olofos/rv321/hardware/memory-ram/memory-ram.kicad_pcb

## KiCad design hardware/memory-ram/memory-ram.kicad_pcb (2022-06-17)

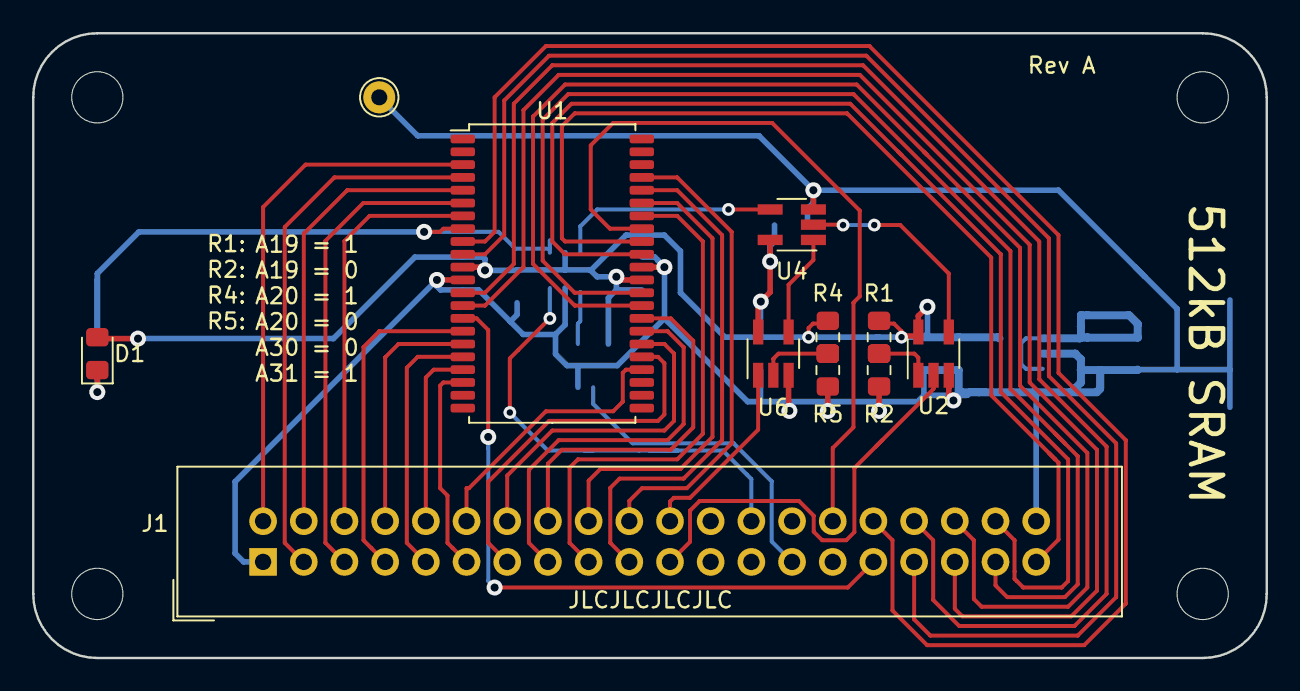
[picture p21: board memory-ram.kicad_pcb from above]

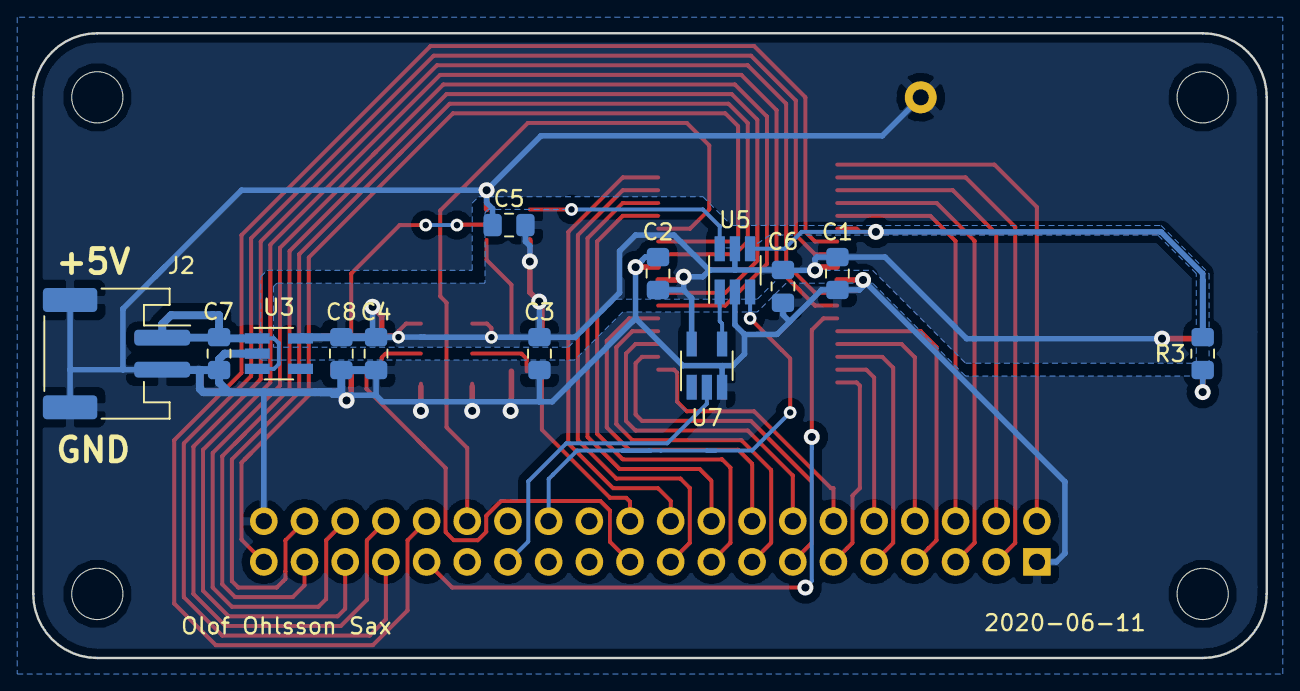
[picture p22: board memory-ram.kicad_pcb from below]

Board: 2 copper layers, 77.0 x 39.0 mm, 28 parts (13 on the bottom side), 44 nets.

Parts:
C1, C2, C3, C4, C5, C6: 100n; C_0805_2012Metric_Pad1.15x1.40mm_HandSolder
C7, C8: 1u; C_0805_2012Metric_Pad1.15x1.40mm_HandSolder
D1: LED; LED_0805_2012Metric_Pad1.15x1.40mm_HandSolder
H1, H2, H3, H4: MountingHole; MountingHole_3.2mm_M3
J1: Conn_Mem_Ext; IDC-Header_2x20_P2.54mm_Vertical
J2: Conn_Power; JST_PH_S2B-PH-SM4-TB_1x02-1MP_P2.00mm_Horizontal
R1, R2, R4, R5: 0; R_0805_2012Metric_Pad1.15x1.40mm_HandSolder
R3: 330; R_0805_2012Metric_Pad1.15x1.40mm_HandSolder
TP1: TestPoint; TestPoint_THTPad_D2.0mm_Drill1.0mm
U1: IS61WV5128EDBLL-10TLI; TSOP-II-44_10.16x18.41mm_P0.8mm
U2, U6: 74LVC1G86; SOT-23-5_HandSoldering
U3: MIC5504-3.3YM5; SOT-23-5_HandSoldering
U4: 74LVC1G32; SOT-23-5_HandSoldering
U5: 74LVC1G332; SOT-23-6_Handsoldering
U7: 74LVC1G04; SOT-23-5_HandSoldering

Connections:
/A0: J1.2, U1.3
/A1: J1.3, U1.4
/A2: J1.4, U1.5
/A3: J1.5, U1.6
/A4: J1.6, U1.7
/A5: J1.7, U1.16
/A6: J1.8, U1.17
/A7: J1.9, U1.18
/A8: J1.10, U1.19
/A9: J1.11, U1.20
/A10: J1.12, U1.26
/A11: J1.13, U1.27
/A12: J1.14, U1.28
/A13: J1.15, U1.29
/A14: J1.16, U1.30
/A15: J1.17, U1.38
/A16: J1.18, U1.39
/A17: J1.19, U1.40
/A18: J1.20, U1.41
/A19: J1.21, U2.2
/A19-20: U4.4, U5.6
/A20: J1.22, U6.1
/A30: J1.26, U5.3
/A31: J1.27, U7.2
/B19: R1.2, R2.1, U2.1
/B20: R4.2, R5.1, U6.2
/D0: J1.32, U1.9
/D1: J1.33, U1.10
/D2: J1.34, U1.13
/D3: J1.35, U1.14
/D4: J1.36, U1.31
/D5: J1.37, U1.32
/D6: J1.38, U1.35
/D7: J1.39, U1.36
/V_IN: C7.2, J2.1, U3.1, U3.3
/X19: U2.4, U4.2
/X20: U4.1, U6.4
/~A31: U5.1, U7.4
/~CE: R3.2, U1.8, U5.4
/~MEM_OE: J1.30, U1.37
/~MEM_WE: J1.31, U1.15
GND: C1.1, C2.1, C3.1, C4.1, C5.1, C6.1, C7.1, C8.1, J1.1, J1.40, J2.2, J2.MP, R2.2, R5.2, TP1.1, U1.12, U1.34, U2.3, U3.2, U4.3, U5.2, U6.3, U7.3
unnamed: D1.1, R3.1
VCC: C1.2, C2.2, C3.2, C4.2, C5.2, C6.2, C8.2, D1.2, R1.1, R4.1, U1.11, U1.33, U2.5, U3.5, U4.5, U5.5, U6.5, U7.5
