olofos/rv321/hardware/pc/pc.kicad_pcb

## KiCad design hardware/pc/pc.kicad_pcb (2022-06-17)

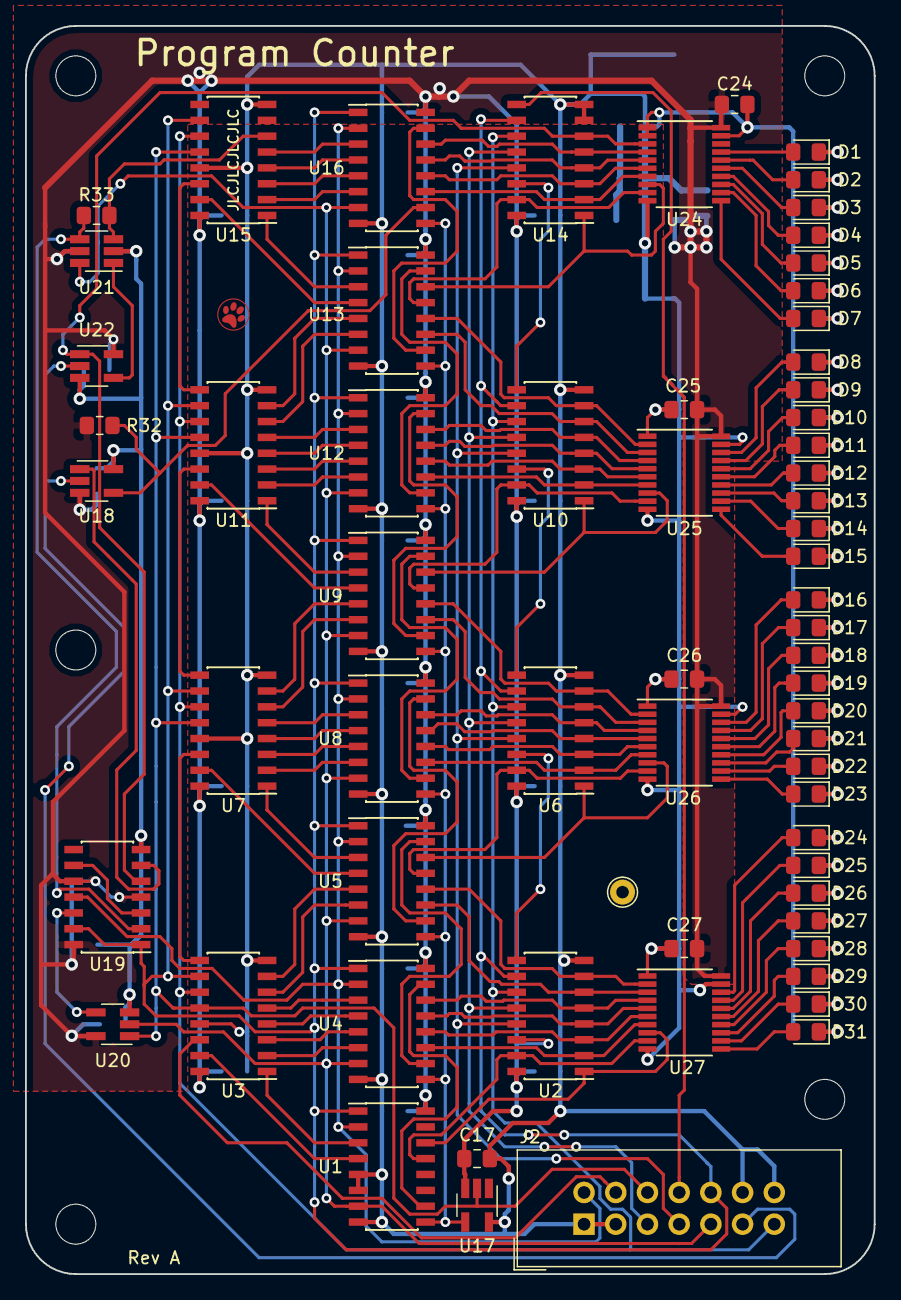
[picture p23: board pc.kicad_pcb from above]

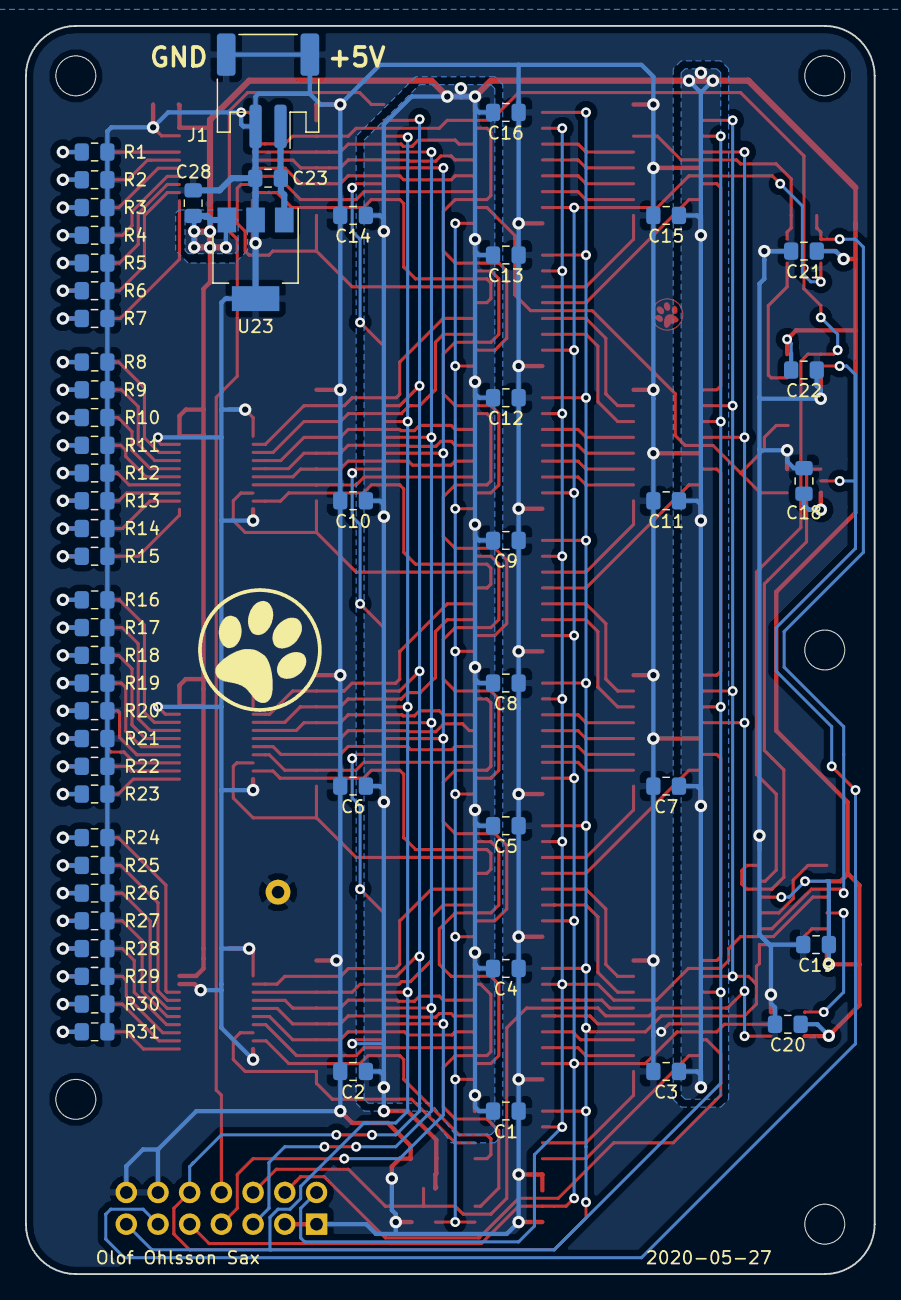
[picture p24: board pc.kicad_pcb from below]

Board: 2 copper layers, 68.0 x 100.0 mm, 127 parts (56 on the bottom side), 157 nets.

Parts:
C1, C2, C3, C4, C5, C6, C7, C8, C9, C10, C11, C12, C13, C14, C15, C16, C17, C18, C19, C20, C21, C22, C24, C25, C26, C27: 100n; C_0805_2012Metric_Pad1.15x1.40mm_HandSolder
C23: 4u7; C_0805_2012Metric_Pad1.15x1.40mm_HandSolder
C28: 1u; C_0805_2012Metric_Pad1.15x1.40mm_HandSolder
D1, D2, D3, D4, D5, D6, D7, D8, D9, D10, D11, D12, D13, D14, D15, D16, D17, D18, D19, D20, D21, D22, D23, D24, D25, D26, D27, D28, D29, D30, D31: LED; LED_0805_2012Metric_Pad1.15x1.40mm_HandSolder
H1, H2, H3, H5, H6: MountingHole; MountingHole_3.2mm_M3
J1: Conn_Power; JST_PH_S2B-PH-SM4-TB_1x02-1MP_P2.00mm_Horizontal
J2: Conn_PC; IDC-Header_2x07_P2.54mm_Vertical
R1, R2, R3, R4, R5, R6, R7, R8, R9, R10, R11, R12, R13, R14, R15, R16, R17, R18, R19, R20, R21, R22, R23, R24, R25, R26, R27, R28, R29, R30, R31: 330; R_0805_2012Metric_Pad1.15x1.40mm_HandSolder
R32, R33: 0; R_0805_2012Metric_Pad1.15x1.40mm_HandSolder
TP1: TestPoint; TestPoint_THTPad_D2.0mm_Drill1.0mm
U1, U4, U5, U8, U9, U12, U13, U16: 74HC161; SOIC-16_3.9x9.9mm_P1.27mm
U2, U6, U10, U14: 74HC597; SOIC-16_3.9x9.9mm_P1.27mm
U3, U7, U11, U15: 74HC595; SOIC-16_3.9x9.9mm_P1.27mm
U17: 74LVC1G04; SOT-23-5_HandSoldering
U18: 74LVC1G38; SOT-23-5_HandSoldering
U19: 74HC74; SOIC-14_3.9x8.7mm_P1.27mm
U20: 74LVC1G32; SOT-23-5_HandSoldering
U21: 74LVC1G157; SOT-23-6_Handsoldering
U22: 74LVC1G86; SOT-23-5_HandSoldering
U23: MCP1825S; SOT-223-3_TabPin2
U24, U25, U26, U27: 74HC541; TSSOP-20_4.4x6.5mm_P0.65mm

Connections:
/BUS_CLK: J2.13, U2.11, U3.11, U6.11, U7.11, U10.11, U11.11, U14.11, U15.11
/CLK: J2.2, U1.2, U4.2, U5.2, U8.2, U9.2, U12.2, U13.2, U16.2, U19.11
/CNT_2: J2.11, U18.2, U22.2
/CNT_EN: J2.9, U1.7, U4.7, U5.7, U8.7, U9.7, U12.7, U13.7, U16.7, U20.2, U21.6
/CNT_~PE: U1.9, U4.9, U5.9, U8.9, U9.9, U12.9, U13.9, U16.9, U17.4
/D1: R33.2, U15.6, U21.3
/D2: U15.5, U16.3
/D3: U15.4, U16.4
/D4: U15.3, U16.5
/D5: U15.2, U16.6
/D6: U13.3, U15.1
/D7: U13.4, U15.15
/D8: U11.7, U13.5
/D8': U11.9, U15.14
/D9: U11.6, U13.6
/D10: U11.5, U12.3
/D11: U11.4, U12.4
/D12: U11.3, U12.5
/D13: U11.2, U12.6
/D14: U9.3, U11.1
/D15: U9.4, U11.15
/D16: U7.7, U9.5
/D16': U7.9, U11.14
/D17: U7.6, U9.6
/D18: U7.5, U8.3
/D19: U7.4, U8.4
/D20: U7.3, U8.5
/D21: U7.2, U8.6
/D22: U5.3, U7.1
/D23: U5.4, U7.15
/D24: U3.7, U5.5
/D24': U3.9, U7.14
/D25: U3.6, U5.6
/D26: U3.5, U4.3
/D27: U3.4, U4.4
/D28: U3.3, U4.5
/D29: U3.2, U4.6
/D30: U1.3, U3.1
/D31: U1.4, U3.15
/IN: J2.4, U3.14
/IN_LATCH: J2.6, U3.12, U7.12, U11.12, U15.12, U17.2, U20.1
/OUT: J2.8, U14.9
/OUT_LATCH: J2.5, U2.12, U6.12, U10.12, U14.12
/OUT_S~P: J2.7, U2.13, U6.13, U10.13, U14.13
/Q1: U14.6, U19.5, U22.1, U24.3
/Q1_CLK: U19.12, U20.4
/Q1_FF_C: U19.3, U19.9
/Q1_FF_D: R33.1, U19.2, U21.4
/Q1_OR_~Q1: U21.1, U22.4
/Q2: U14.5, U16.14, U24.4
/Q3: U14.4, U16.13, U24.5
/Q4: U14.3, U16.12, U24.6
/Q5: U14.2, U16.11, U24.7
/Q6: U13.14, U14.1, U24.8
/Q7: U13.13, U14.15, U24.9
/Q8: U10.7, U13.12, U25.2
/Q8': U10.9, U14.14
/Q9: U10.6, U13.11, U25.3
/Q10: U10.5, U12.14, U25.4
/Q11: U10.4, U12.13, U25.5
/Q12: U10.3, U12.12, U25.6
/Q13: U10.2, U12.11, U25.7
/Q14: U9.14, U10.1, U25.8
/Q15: U9.13, U10.15, U25.9
/Q16: U6.7, U9.12, U26.2
/Q16': U6.9, U10.14
/Q17: U6.6, U9.11, U26.3
/Q18: U6.5, U8.14, U26.4
/Q19: U6.4, U8.13, U26.5
/Q20: U6.3, U8.12, U26.6
/Q21: U6.2, U8.11, U26.7
/Q22: U5.14, U6.1, U26.8
/Q23: U5.13, U6.15, U26.9
/Q24: U2.7, U5.12, U27.2
/Q24': U2.9, U6.14
/Q25: U2.6, U5.11, U27.3
/Q26: U2.5, U4.14, U27.4
/Q27: U2.4, U4.13, U27.5
/Q28: U2.3, U4.12, U27.6
/Q29: U2.2, U4.11, U27.7
/Q30: U1.14, U2.1, U27.8
/Q31: U1.13, U2.15, U27.9
/TC1: R32.2, U16.10, U18.4
/TC5: U13.10, U16.15
/TC9: U12.10, U13.15
/TC13: U9.10, U12.15
/TC17: U8.10, U9.15
/TC21: U5.10, U8.15
/TC25: U4.10, U5.15
/TC29: U1.10, U4.15
/V_IN: C23.1, J1.1, U23.1
/~Q1: U18.1, U19.6
/~RESET: J2.10, U1.1, U2.10, U3.10, U4.1, U5.1, U6.10, U7.10, U8.1, U9.1, U10.10, U11.10, U12.1, U13.1, U14.10, U15.10, U16.1, U19.1, U19.13
GND: C1.2, C2.2, C3.2, C4.2, C5.2, C6.2, C7.2, C8.2, C9.2, C10.2, C11.2, C12.2, C13.2, C14.2, C15.2, C16.2, C17.2, C18.2, C19.2, C20.2, C21.2, C22.2, C23.2, C24.2, C25.2, C26.2, C27.2, C28.2, J1.2, J1.MP, J2.1, J2.3, J2.12, J2.14, R1.2, R2.2, R3.2, R4.2, R5.2, R6.2, R7.2, R8.2, R9.2, R10.2, R11.2, R12.2, R13.2, R14.2, R15.2, R16.2, R17.2, R18.2, R19.2, R20.2, R21.2, R22.2, R23.2, R24.2, R25.2, R26.2, R27.2, R28.2, R29.2, R30.2, R31.2, TP1.1, U1.5, U1.6, U1.8, U2.8, U3.8, U3.13, U4.8, U5.8, U6.8, U7.8, U7.13, U8.8, U9.8, U10.8, U11.8, U11.13, U12.8, U13.8, U14.7, U14.8, U15.8, U15.13, U16.8, U17.5, U18.5, U19.7, U20.3, U21.2, U22.3, U23.2, U24.1, U24.2, U24.10, U24.19, U25.1, U25.10, U25.19, U26.1, U26.10, U26.19, U27.1, U27.10, U27.19
unnamed: D1.1, R1.1
unnamed: D1.2, U24.17
unnamed: D2.1, R2.1
unnamed: D2.2, U24.16
unnamed: D3.1, R3.1
unnamed: D3.2, U24.15
unnamed: D4.1, R4.1
unnamed: D4.2, U24.14
unnamed: D5.1, R5.1
unnamed: D5.2, U24.13
unnamed: D6.1, R6.1
unnamed: D6.2, U24.12
unnamed: D7.1, R7.1
unnamed: D7.2, U24.11
unnamed: D8.1, R8.1
unnamed: D8.2, U25.18
unnamed: D9.1, R9.1
unnamed: D9.2, U25.17
unnamed: D10.1, R10.1
unnamed: D10.2, U25.16
unnamed: D11.1, R11.1
unnamed: D11.2, U25.15
unnamed: D12.1, R12.1
unnamed: D12.2, U25.14
unnamed: D13.1, R13.1
unnamed: D13.2, U25.13
unnamed: D14.1, R14.1
unnamed: D14.2, U25.12
unnamed: D15.1, R15.1
unnamed: D15.2, U25.11
unnamed: D16.1, R16.1
unnamed: D16.2, U26.18
unnamed: D17.1, R17.1
unnamed: D17.2, U26.17
unnamed: D18.1, R18.1
unnamed: D18.2, U26.16
unnamed: D19.1, R19.1
unnamed: D19.2, U26.15
unnamed: D20.1, R20.1
unnamed: D20.2, U26.14
unnamed: D21.1, R21.1
unnamed: D21.2, U26.13
unnamed: D22.1, R22.1
unnamed: D22.2, U26.12
unnamed: D23.1, R23.1
unnamed: D23.2, U26.11
unnamed: D24.1, R24.1
unnamed: D24.2, U27.18
unnamed: D25.1, R25.1
unnamed: D25.2, U27.17
unnamed: D26.1, R26.1
unnamed: D26.2, U27.16
unnamed: D27.1, R27.1
unnamed: D27.2, U27.15
unnamed: D28.1, R28.1
unnamed: D28.2, U27.14
unnamed: D29.1, R29.1
unnamed: D29.2, U27.13
unnamed: D30.1, R30.1
unnamed: D30.2, U27.12
unnamed: D31.1, R31.1
unnamed: D31.2, U27.11
VCC: C1.1, C2.1, C3.1, C4.1, C5.1, C6.1, C7.1, C8.1, C9.1, C10.1, C11.1, C12.1, C13.1, C14.1, C15.1, C16.1, C17.1, C18.1, C19.1, C20.1, C21.1, C22.1, C24.1, C25.1, C26.1, C27.1, C28.1, R32.1, U1.16, U2.14, U2.16, U3.16, U4.16, U5.16, U6.16, U7.16, U8.16, U9.16, U10.16, U11.16, U12.16, U13.16, U14.16, U15.16, U16.16, U17.3, U18.3, U19.4, U19.10, U19.14, U20.5, U21.5, U22.5, U23.3, U24.20, U25.20, U26.20, U27.20
