olofos/rv321/hardware/alu/alu.kicad_pcb

## KiCad design hardware/alu/alu.kicad_pcb (2022-06-17)

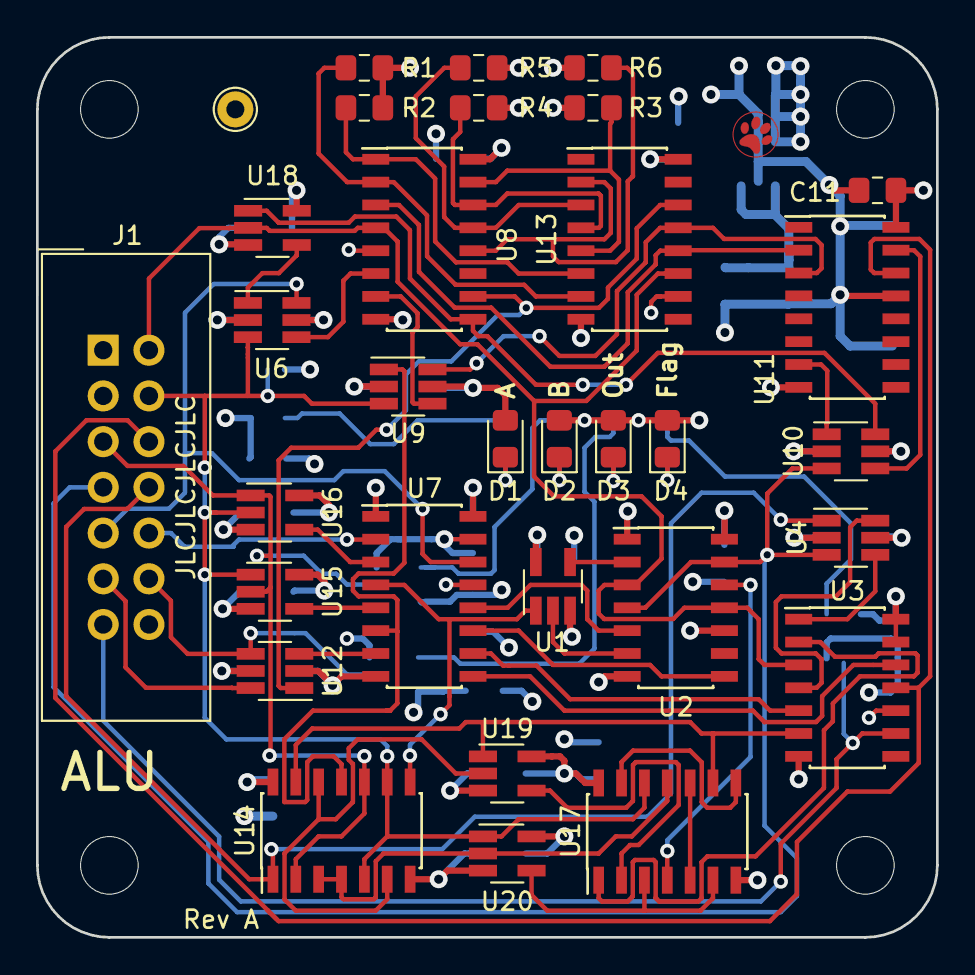
[picture p25: board alu.kicad_pcb from above]

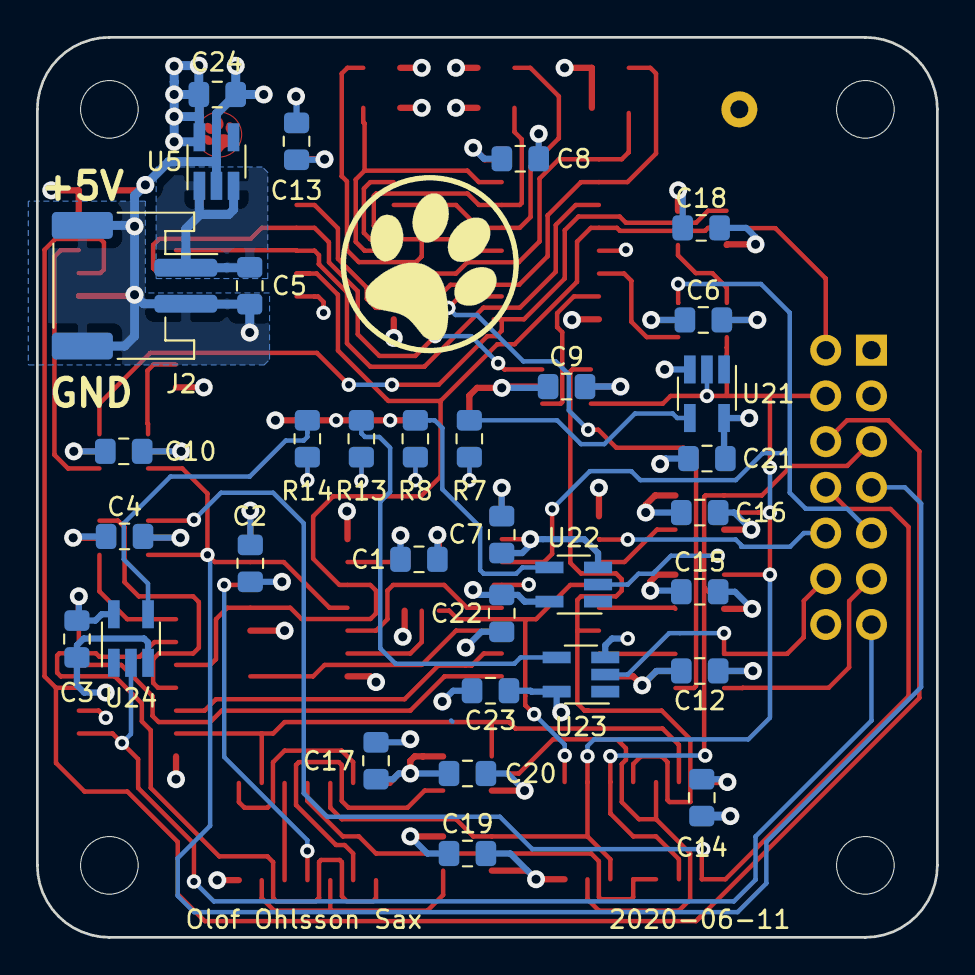
[picture p26: board alu.kicad_pcb from below]

Board: 4 copper layers, 50.0 x 50.0 mm, 69 parts (33 on the bottom side), 59 nets.

Parts:
C1, C2, C3, C4, C6, C7, C8, C9, C10, C11, C12, C13, C14, C15, C16, C17, C18, C19, C20, C21, C22, C23: 100n; C_0805_2012Metric_Pad1.15x1.40mm_HandSolder
C5, C24: 1u; C_0805_2012Metric_Pad1.15x1.40mm_HandSolder
D1, D2, D3, D4: LED; LED_0805_2012Metric_Pad1.15x1.40mm_HandSolder
H1, H2, H3, H4: MountingHole; MountingHole_3.2mm_M3
J1: Conn_ALU; IDC-Header_2x07_P2.54mm_Vertical
J2: Conn_Power; JST_PH_S2B-PH-SM4-TB_1x02-1MP_P2.00mm_Horizontal
R1, R2, R3, R4, R5, R6: 10k; R_0805_2012Metric_Pad1.15x1.40mm_HandSolder
R7, R8, R13, R14: 330; R_0805_2012Metric_Pad1.15x1.40mm_HandSolder
TP1: TestPoint; TestPoint_THTPad_D2.0mm_Drill1.0mm
U1: 74LVC1G02; SOT-23-5_HandSoldering
U2, U3: 74HC74; SOIC-14_3.9x8.7mm_P1.27mm
U4: 74LVC1G19; SOT-23-6_Handsoldering
U5: MIC5504-3.3YM5; SOT-23-5_HandSoldering
U6: 74LVC1G175; SOT-23-6_Handsoldering
U7: 74HC253; SOIC-16_3.9x9.9mm_P1.27mm
U8: HEF4557B; SOIC-16_3.9x9.9mm_P1.27mm
U9, U12: 74LVC1G157; SOT-23-6_Handsoldering
U10: 74AUC2G04; SOT-23-6_Handsoldering
U11: 74HC4017; SOIC-16_3.9x9.9mm_P1.27mm
U13: 74HC595; SOIC-16_3.9x9.9mm_P1.27mm
U14: 74HC86; SOIC-14_3.9x8.7mm_P1.27mm
U15: 74LVC1G32; SOT-23-5_HandSoldering
U16, U18, U19, U20: 74LVC1G08; SOT-23-5_HandSoldering
U17: 74HC02; SOIC-14_3.9x8.7mm_P1.27mm
U21, U22, U23, U24: 74LVC1G04; SOT-23-5_HandSoldering

Connections:
/(A+B)&C: U17.2, U19.4
/A&~B: U17.3, U17.6, U20.4
/A+B: U14.6, U14.12, U19.2
/ALU_AUX: J1.6, U3.11, U11.14
/ALU_S0: J1.9, U6.6, U7.14
/ALU_S1: J1.10, U7.2
/ALU_S2: J1.11, U12.6
/BUS_CLK: J1.2, U2.3, U2.11, U3.3, U8.4, U13.11, U18.2
/B_OR_~B: U14.3, U14.4, U17.11, U20.2
/C_TO_NEG: U17.5, U17.10
/DAH: D1.1, R7.2
/DAL: R7.1, U21.4
/DBH: D2.1, R8.2
/DBL: R8.1, U22.4
/DFH: D4.1, R14.2
/DFL: R14.1, U24.4
/DOH: D3.1, R13.2
/DOL: R13.1, U23.4
/EQUAL: U2.5, U7.12
/EQ_FF_D: U1.4, U2.2
/EQ_FF_~Q: U1.2, U2.6
/FLAG: U3.12, U7.9
/IN_A: J1.4, U6.3, U9.3, U14.5, U14.9, U15.1, U16.2, U17.12, U20.1, U21.2
/IN_B: J1.5, U14.2, U14.10, U15.2, U16.1, U22.2
/IN_C: U3.6, U14.13, U17.9, U19.1
/IN_N: J1.8, U4.1, U14.1
/L1: R1.2, U8.2, U13.7
/L2: R2.2, U8.1, U13.6
/L4: R3.2, U8.15, U13.5
/L8: R4.1, U8.14, U13.4
/L16: R5.2, U8.13, U13.3
/L32: R6.1, U8.12, U13.2
/LT: U2.8, U7.11
/LTU: U3.5, U7.10
/OUT: J1.12, U12.4, U23.2
/OUT_AND: U7.3, U16.4
/OUT_BIN: U7.7, U12.3
/OUT_FLAG: J1.13, U3.9, U24.2
/OUT_OR: U7.5, U15.4
/OUT_SHIFT: U8.10, U12.1, U13.14
/OUT_SUM: U7.6, U9.1, U14.11
/OUT_XOR: U1.1, U7.4, U14.8
/SH_4017_MR: U10.4, U11.15
/SH_IN: U8.7, U9.4
/SH_LOADLEN: U9.6, U11.3, U13.13
/SH_OUTPUT: U10.1, U11.7
/SH_RESET: U8.3, U11.2, U13.12
/SH_S_FF_C: U6.1, U18.4
/SH_S_FF_Q: U6.4, U8.6
/V_IN: C5.1, J2.1, U5.1, U5.3
/~ALU_RESET: J1.7, U2.4, U2.13, U4.3, U10.3
/~A&B: U17.8, U17.13
/~C_FF_~R: U3.1, U4.4
/~C_FF_~S: U3.4, U4.6
/~OUT_C: U3.2, U17.1
/~OUT_NEG: U2.12, U17.4
/~SH_OUTPUT: U8.9, U10.6, U18.1
GND: C1.2, C2.2, C3.2, C4.2, C5.2, C6.2, C7.2, C8.2, C9.2, C10.2, C11.2, C12.2, C13.2, C14.2, C15.2, C16.2, C17.2, C18.2, C19.2, C20.2, C21.2, C22.2, C23.2, C24.2, J1.1, J1.3, J1.14, J2.2, J2.MP, R4.2, R6.2, TP1.1, U1.3, U2.7, U3.7, U4.2, U5.2, U6.2, U7.1, U7.8, U7.13, U7.15, U8.5, U8.8, U9.2, U10.2, U11.8, U11.13, U12.2, U13.8, U14.7, U15.3, U16.3, U17.7, U18.3, U19.3, U20.3, U21.3, U22.3, U23.3, U24.3
VCC: C1.1, C2.1, C3.1, C4.1, C6.1, C7.1, C8.1, C9.1, C10.1, C11.1, C12.1, C13.1, C14.1, C15.1, C16.1, C17.1, C18.1, C19.1, C20.1, C21.1, C22.1, C23.1, C24.1, D1.2, D2.2, D3.2, D4.2, R1.1, R2.1, R3.1, R5.1, U1.5, U2.1, U2.10, U2.14, U3.10, U3.13, U3.14, U4.5, U5.5, U6.5, U7.16, U8.16, U9.5, U10.5, U11.16, U12.5, U13.10, U13.16, U14.14, U15.5, U16.5, U17.14, U18.5, U19.5, U20.5, U21.5, U22.5, U23.5, U24.5
