olofos/rv321/hardware/register-bank/register-bank.kicad_pcb

## KiCad design hardware/register-bank/register-bank.kicad_pcb (2022-06-17)

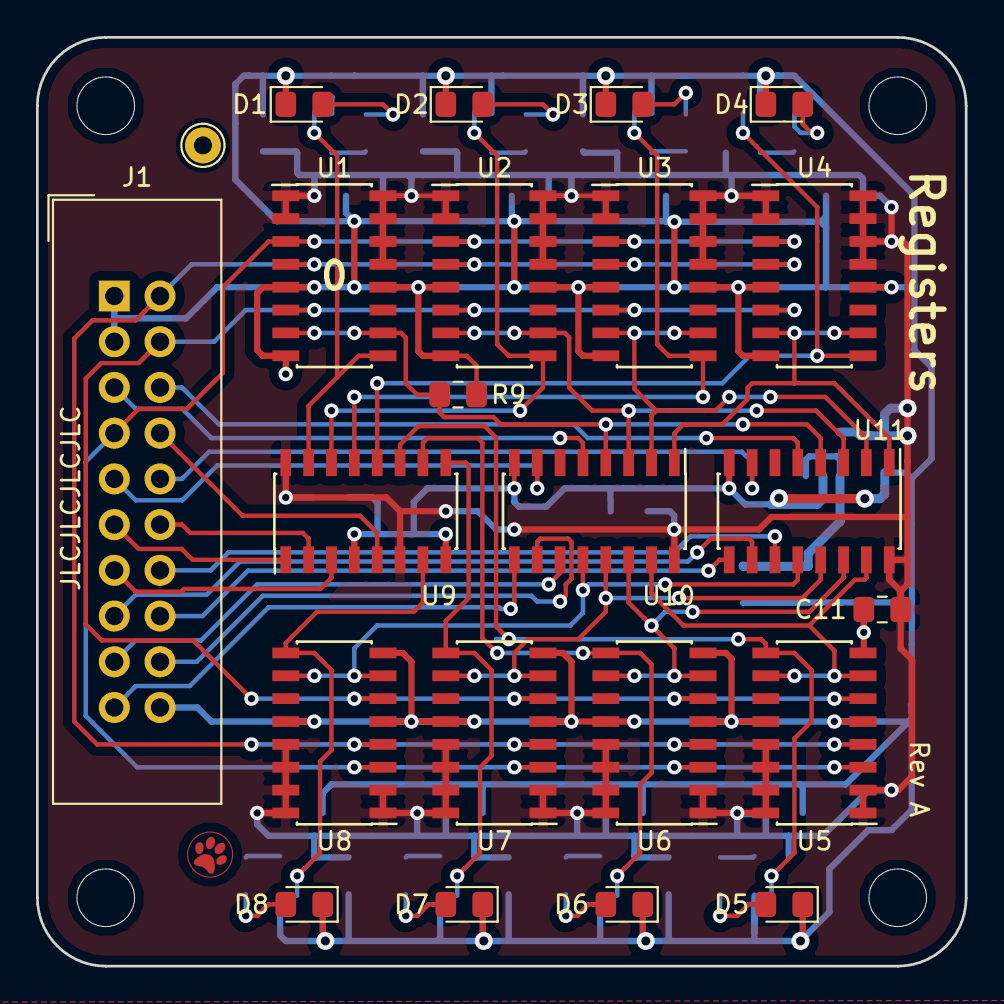
[picture p27: board register-bank.kicad_pcb from above]

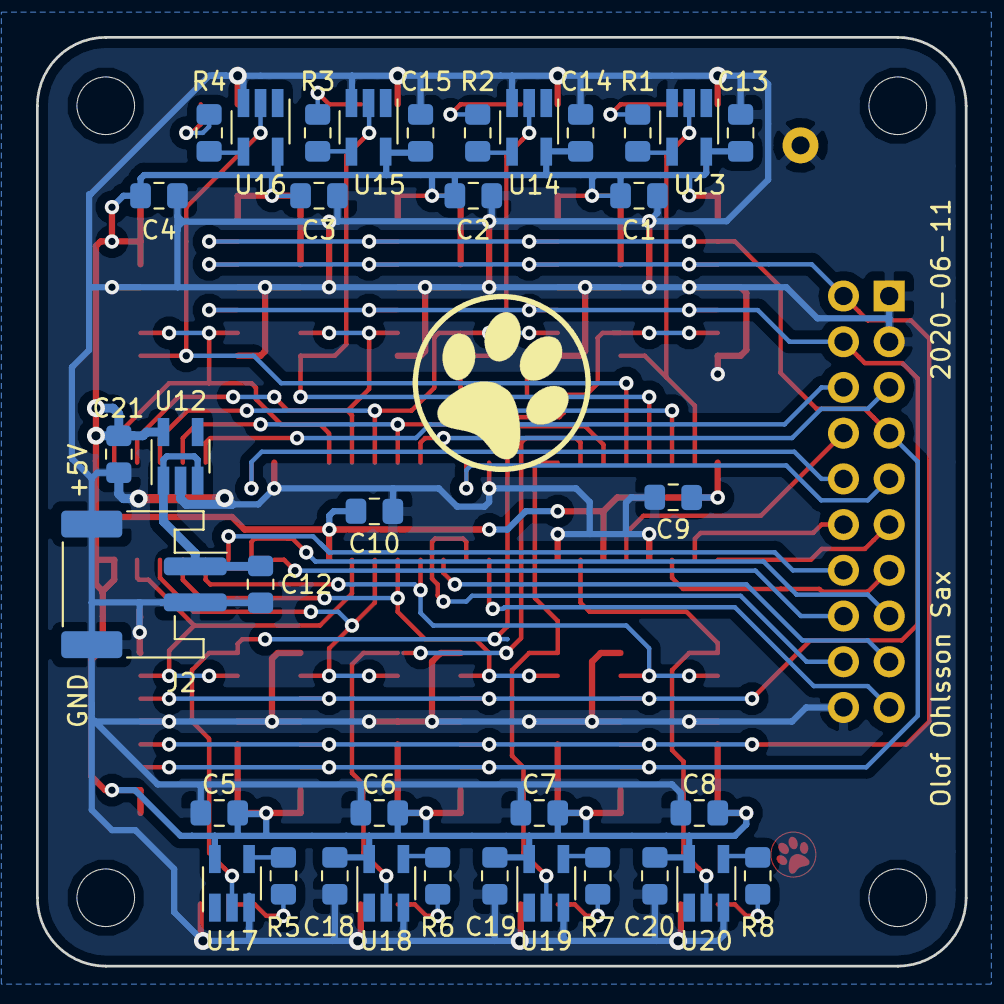
[picture p28: board register-bank.kicad_pcb from below]

Board: 2 copper layers, 51.6 x 51.6 mm, 63 parts (36 on the bottom side), 52 nets.

Parts:
C1, C2, C3, C4, C5, C6, C7, C8, C9, C10, C11, C13, C14, C15, C18, C19, C20: 100n; C_0805_2012Metric_Pad1.15x1.40mm_HandSolder
C12, C21: 1u; C_0805_2012Metric_Pad1.15x1.40mm_HandSolder
D1, D2, D3, D4, D5, D6, D7, D8: LED; LED_0805_2012Metric_Pad1.15x1.40mm_HandSolder
H1, H2, H3, H4: MountingHole; MountingHole_3.2mm_M3
J1: Conn_Reg; IDC-Header_2x10_P2.54mm_Vertical
J2: Conn_Power; JST_PH_S2B-PH-SM4-TB_1x02-1MP_P2.00mm_Horizontal
R1, R2, R3, R4, R5, R6, R7, R8: 330; R_0805_2012Metric_Pad1.15x1.40mm_HandSolder
R9: 0; R_0805_2012Metric_Pad1.15x1.40mm_HandSolder
TP1: TestPoint; TestPoint_THTPad_D2.0mm_Drill1.0mm
U1, U2, U3, U4, U5, U6, U7, U8: HEF4557B; SOIC-16_3.9x9.9mm_P1.27mm
U9: 74HC138; SOIC-16_3.9x9.9mm_P1.27mm
U10, U11: 74HC251; SOIC-16_3.9x9.9mm_P1.27mm
U12: MIC5504-3.3YM5; SOT-23-5_HandSoldering
U13, U14, U15, U16, U17, U18, U19, U20: 74LVC1G04; SOT-23-5_HandSoldering

Connections:
/BUS_CLK: J1.2, U1.4, U2.4, U3.4, U4.4, U5.4, U6.4, U7.4, U8.4
/RAOUT: J1.5, U10.5
/RAS0: J1.17, U10.11
/RAS1: J1.18, U10.10
/RAS2: J1.19, U10.9
/RBOUT: J1.6, U11.5
/RBS0: J1.14, U11.11
/RBS1: J1.15, U11.10
/RBS2: J1.16, U11.9
/RESET: J1.7, U1.3, U2.3, U3.3, U4.3, U5.3, U6.3, U7.3, U8.3
/RIN: J1.4, U1.6, U2.6, U3.6, U4.6, U5.6, U6.6, U7.6, U8.6
/RINS0: J1.11, U9.1
/RINS1: J1.12, U9.2
/RINS2: J1.13, U9.3
/ROUT0: R9.1, U1.7, U1.10, U10.4, U11.4
/ROUT1: U2.7, U2.10, U10.3, U11.3
/ROUT2: U3.7, U3.10, U10.2, U11.2
/ROUT3: U4.7, U4.10, U10.1, U11.1
/ROUT4: U5.7, U5.10, U10.15, U11.15
/ROUT5: U6.7, U6.10, U10.14, U11.14
/ROUT6: U7.7, U7.10, U10.13, U11.13
/ROUT7: U8.7, U8.10, U10.12, U11.12
/V_IN: C12.1, J2.1, U12.1, U12.3
/~RIN_EN0: U1.9, U9.15, U13.2
/~RIN_EN1: U2.9, U9.14, U14.2
/~RIN_EN2: U3.9, U9.13, U15.2
/~RIN_EN3: U4.9, U9.12, U16.2
/~RIN_EN4: U5.9, U9.11, U17.2
/~RIN_EN5: U6.9, U9.10, U18.2
/~RIN_EN6: U7.9, U9.9, U19.2
/~RIN_EN7: U8.9, U9.7, U20.2
/~RIN_EN: J1.8, U9.5
/~ROUT_EN_A: J1.9, U10.7
/~ROUT_EN_B: J1.10, U11.7
GND: C1.2, C2.2, C3.2, C4.2, C5.2, C6.2, C7.2, C8.2, C9.2, C10.2, C11.2, C12.2, C13.2, C14.2, C15.2, C18.2, C19.2, C20.2, C21.2, D1.1, D2.1, D3.1, D4.1, D5.1, D6.1, D7.1, D8.1, J1.1, J1.3, J1.20, J2.2, J2.MP, R9.2, TP1.1, U1.5, U1.8, U1.12, U2.5, U2.8, U2.12, U3.5, U3.8, U3.12, U4.5, U4.8, U4.12, U5.5, U5.8, U5.12, U6.5, U6.8, U6.12, U7.5, U7.8, U7.12, U8.5, U8.8, U8.12, U9.4, U9.8, U10.8, U11.8, U12.2, U13.3, U14.3, U15.3, U16.3, U17.3, U18.3, U19.3, U20.3
unnamed: D1.2, R1.1
unnamed: D2.2, R2.1
unnamed: D3.2, R3.1
unnamed: D4.2, R4.1
unnamed: D5.2, R5.1
unnamed: D6.2, R6.1
unnamed: D7.2, R7.1
unnamed: D8.2, R8.1
unnamed: R1.2, U13.4
unnamed: R2.2, U14.4
unnamed: R3.2, U15.4
unnamed: R4.2, U16.4
unnamed: R5.2, U17.4
unnamed: R6.2, U18.4
unnamed: R7.2, U19.4
unnamed: R8.2, U20.4
VCC: C1.1, C2.1, C3.1, C4.1, C5.1, C6.1, C7.1, C8.1, C9.1, C10.1, C11.1, C13.1, C14.1, C15.1, C18.1, C19.1, C20.1, C21.1, U1.1, U1.2, U1.13, U1.14, U1.15, U1.16, U2.1, U2.2, U2.13, U2.14, U2.15, U2.16, U3.1, U3.2, U3.13, U3.14, U3.15, U3.16, U4.1, U4.2, U4.13, U4.14, U4.15, U4.16, U5.1, U5.2, U5.13, U5.14, U5.15, U5.16, U6.1, U6.2, U6.13, U6.14, U6.15, U6.16, U7.1, U7.2, U7.13, U7.14, U7.15, U7.16, U8.1, U8.2, U8.13, U8.14, U8.15, U8.16, U9.6, U9.16, U10.16, U11.16, U12.5, U13.5, U14.5, U15.5, U16.5, U17.5, U18.5, U19.5, U20.5
