olofos/rv321/hardware/memory/memory.kicad_pcb

## KiCad design hardware/memory/memory.kicad_pcb (2022-06-17)

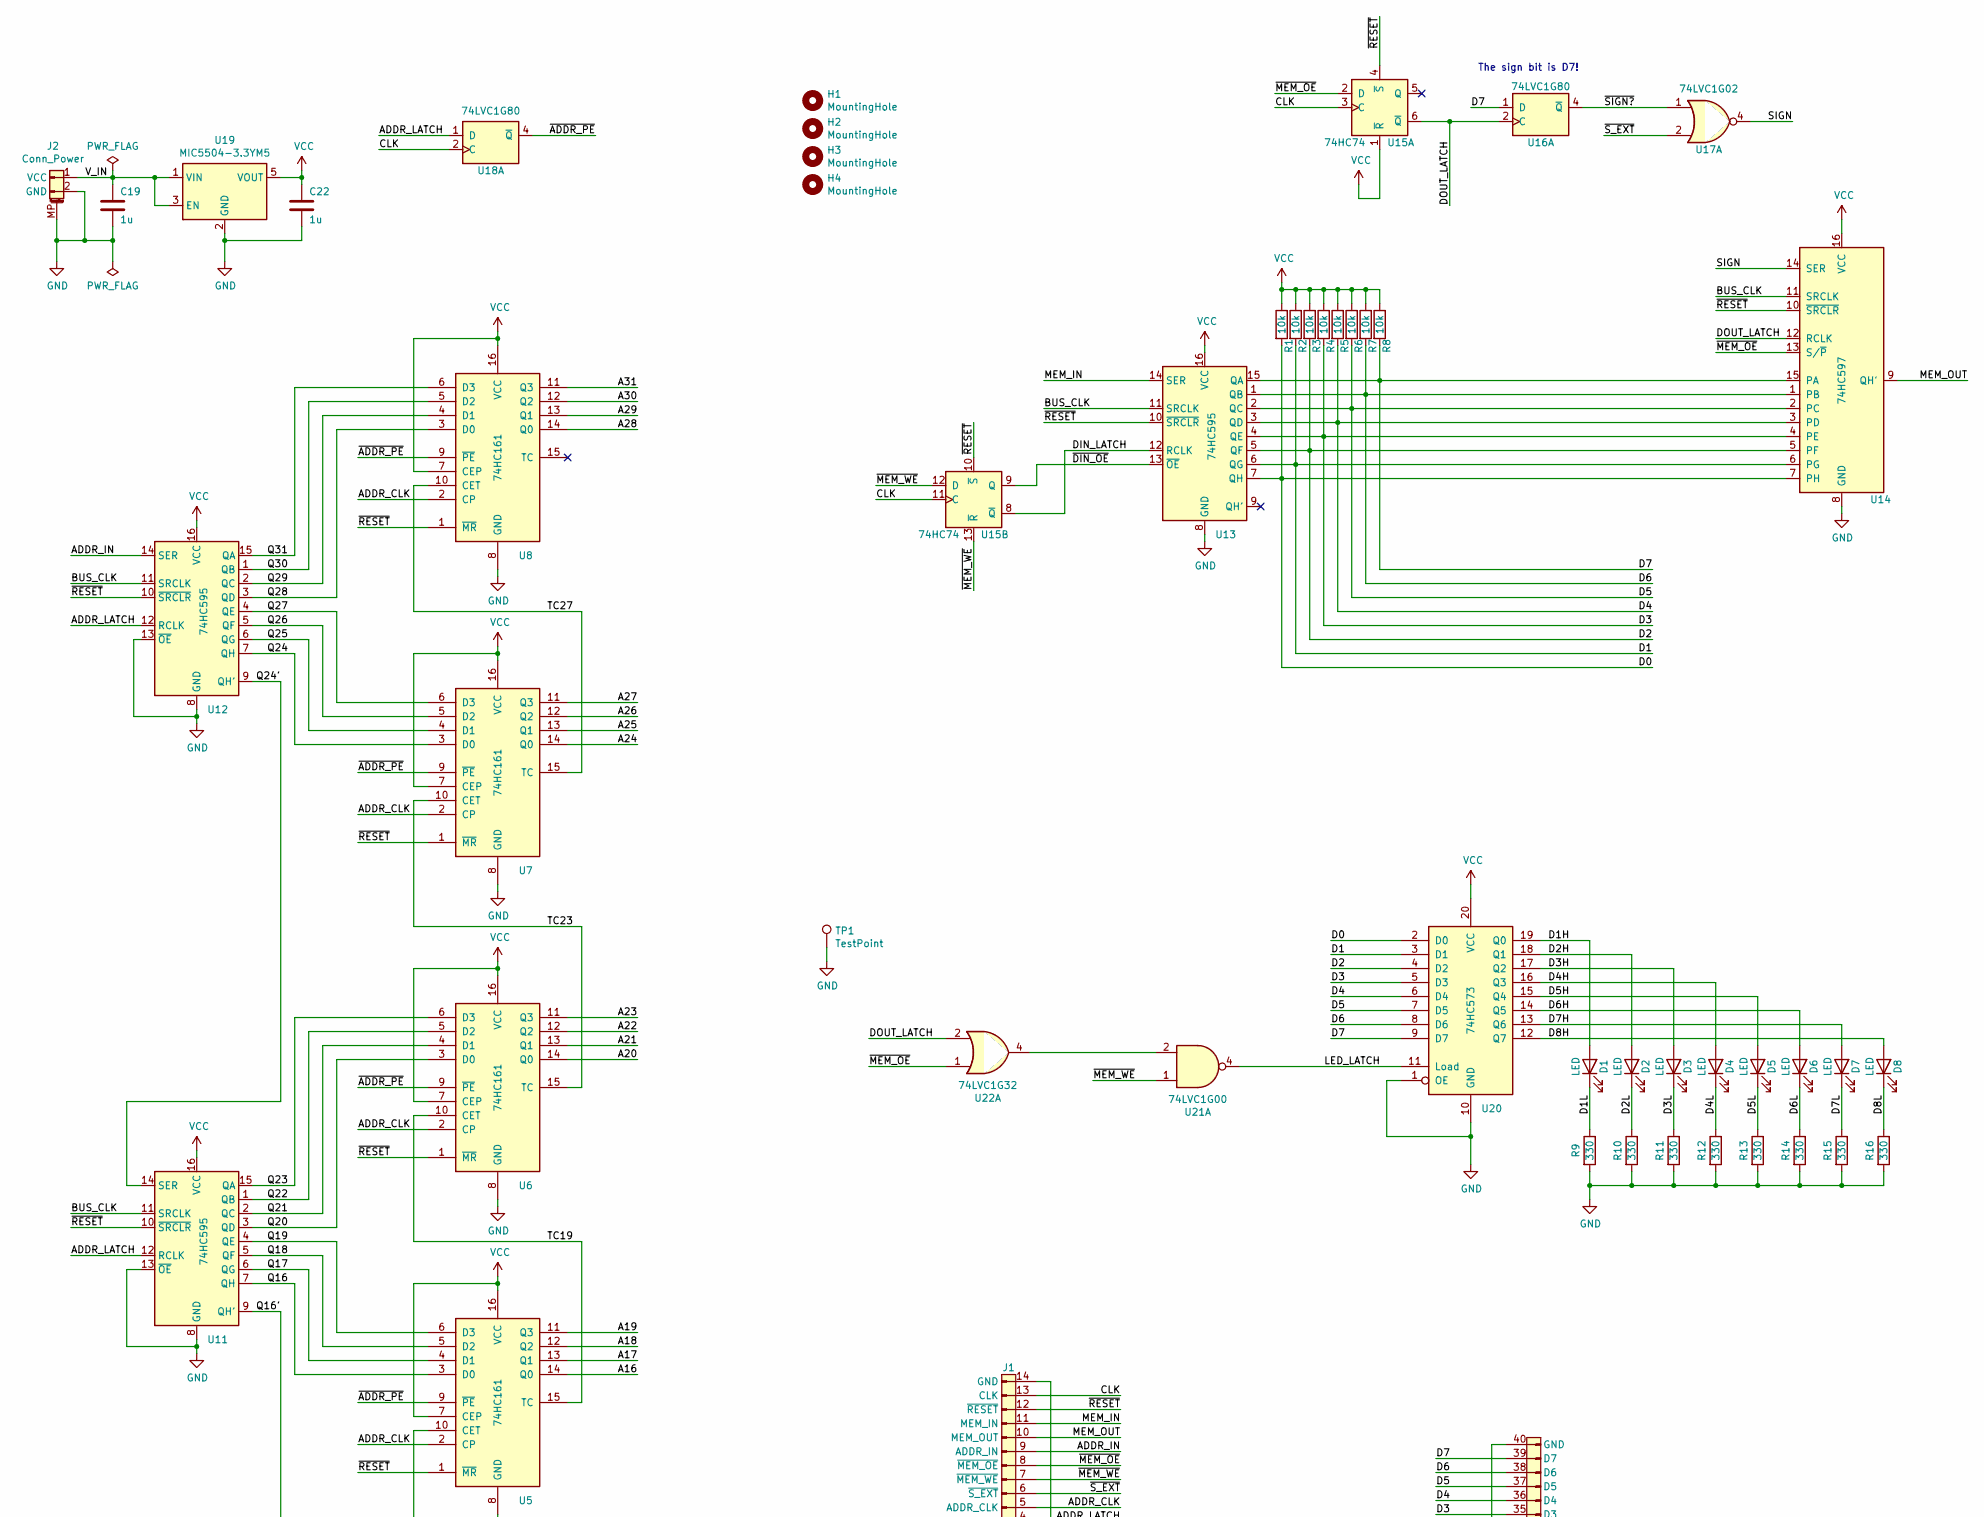
[picture p29: schematic memory.kicad_sch, part in row 1, column 1]

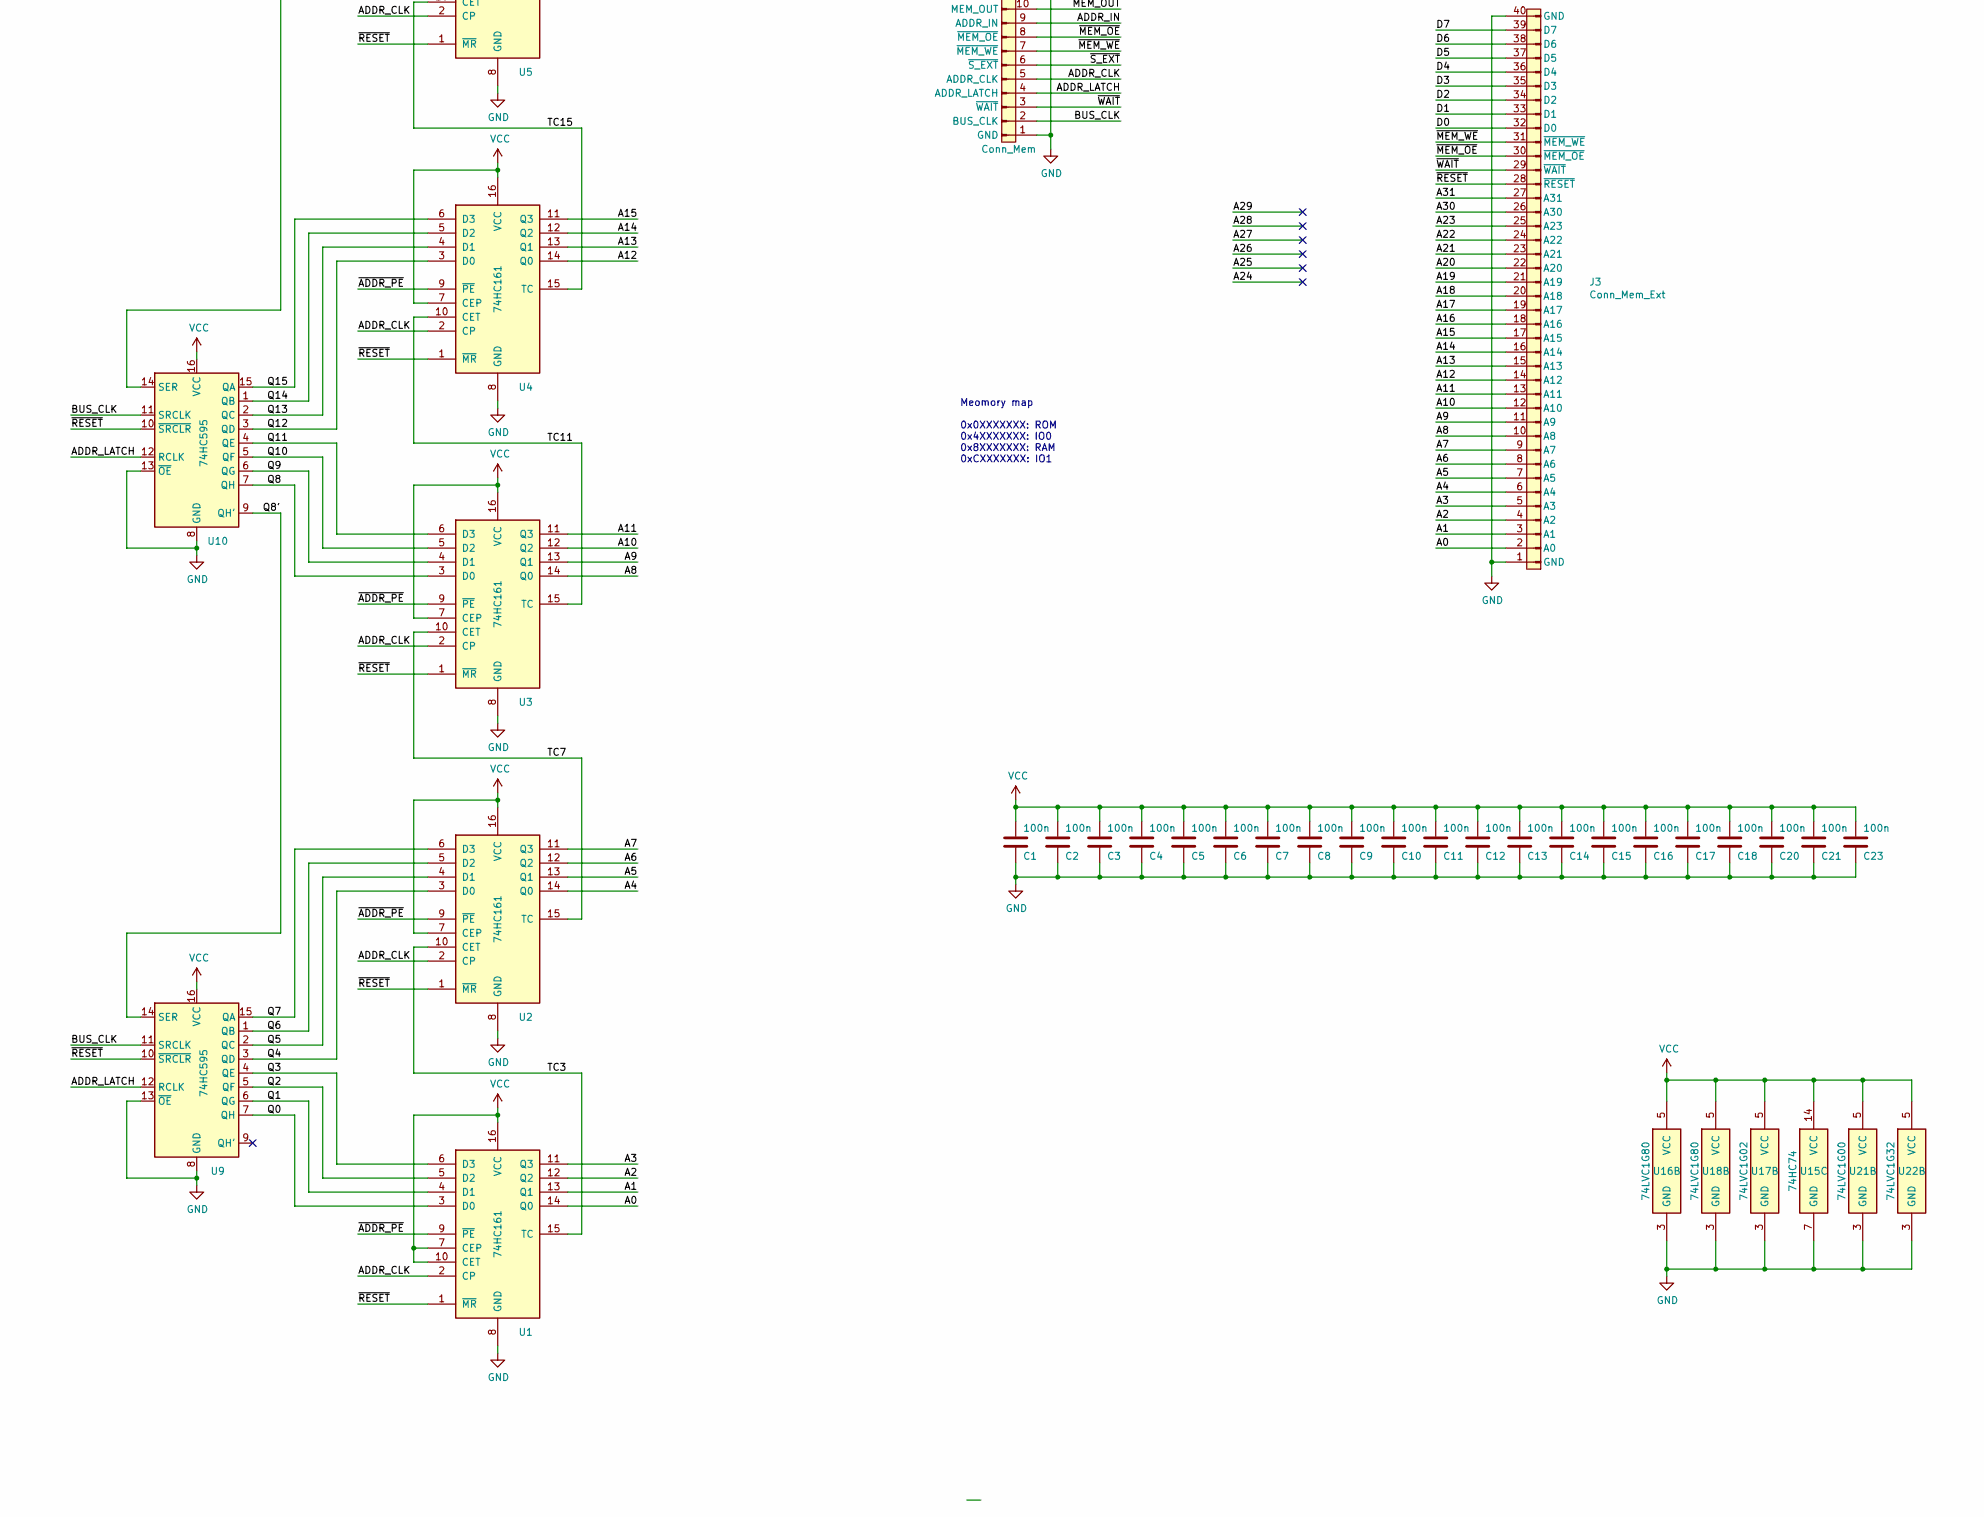
[picture p30: schematic memory.kicad_sch, part in row 2, column 1]

Parts:
C1, C2, C3, C4, C5, C6, C7, C8, C9, C10, C11, C12, C13, C14, C15, C16, C17, C18, C20, C21: 100n; C_0805_2012Metric_Pad1.15x1.40mm_HandSolder
C19, C22: 1u; C_0805_2012Metric_Pad1.15x1.40mm_HandSolder
C23: 100n; C_0805_2012Metric_Pad1.18x1.45mm_HandSolder
D1, D2, D3, D4, D5, D6, D7, D8: LED; LED_0805_2012Metric_Pad1.15x1.40mm_HandSolder
H1, H2, H3, H4: MountingHole; MountingHole_3.2mm_M3
J1: Conn_Mem; IDC-Header_2x07_P2.54mm_Vertical
J2: Conn_Power; JST_PH_S2B-PH-SM4-TB_1x02-1MP_P2.00mm_Horizontal
J3: Conn_Mem_Ext; IDC-Header_2x20_P2.54mm_Vertical
R1, R2, R3, R4, R5, R6, R7, R8: 10k; R_0805_2012Metric_Pad1.15x1.40mm_HandSolder
R9, R10, R11, R12, R13, R14, R15, R16: 330; R_0805_2012Metric_Pad1.15x1.40mm_HandSolder
TP1: TestPoint; TestPoint_THTPad_D2.0mm_Drill1.0mm
U1, U2, U3, U4, U5, U6, U7, U8: 74HC161; SOIC-16_3.9x9.9mm_P1.27mm
U9, U10, U11, U12, U13: 74HC595; SOIC-16_3.9x9.9mm_P1.27mm
U14: 74HC597; SOIC-16_3.9x9.9mm_P1.27mm
U15: 74HC74; SOIC-14_3.9x8.7mm_P1.27mm
U16, U18: 74LVC1G80; SOT-23-5_HandSoldering
U17: 74LVC1G02; SOT-23-5_HandSoldering
U19: MIC5504-3.3YM5; SOT-23-5_HandSoldering
U20: 74HC573; TSSOP-20_4.4x6.5mm_P0.65mm
U21: 74LVC1G00; SOT-23-5_HandSoldering
U22: 74LVC1G32; SOT-23-5_HandSoldering

Connections:
/A0: J3.2 (A0), U1.14 (Q0)
/A1: J3.3 (A1), U1.13 (Q1)
/A2: J3.4 (A2), U1.12 (Q2)
/A3: J3.5 (A3), U1.11 (Q3)
/A4: J3.6 (A4), U2.14 (Q0)
/A5: J3.7 (A5), U2.13 (Q1)
/A6: J3.8 (A6), U2.12 (Q2)
/A7: J3.9 (A7), U2.11 (Q3)
/A8: J3.10 (A8), U3.14 (Q0)
/A9: J3.11 (A9), U3.13 (Q1)
/A10: J3.12 (A10), U3.12 (Q2)
/A11: J3.13 (A11), U3.11 (Q3)
/A12: J3.14 (A12), U4.14 (Q0)
/A13: J3.15 (A13), U4.13 (Q1)
/A14: J3.16 (A14), U4.12 (Q2)
/A15: J3.17 (A15), U4.11 (Q3)
/A16: J3.18 (A16), U5.14 (Q0)
/A17: J3.19 (A17), U5.13 (Q1)
/A18: J3.20 (A18), U5.12 (Q2)
/A19: J3.21 (A19), U5.11 (Q3)
/A20: J3.22 (A20), U6.14 (Q0)
/A21: J3.23 (A21), U6.13 (Q1)
/A22: J3.24 (A22), U6.12 (Q2)
/A23: J3.25 (A23), U6.11 (Q3)
/A24: U7.14 (Q0)
/A25: U7.13 (Q1)
/A26: U7.12 (Q2)
/A27: U7.11 (Q3)
/A28: U8.14 (Q0)
/A29: U8.13 (Q1)
/A30: J3.26 (A30), U8.12 (Q2)
/A31: J3.27 (A31), U8.11 (Q3)
/ADDR_CLK: J1.5 (ADDR_CLK), U1.2 (CP), U2.2 (CP), U3.2 (CP), U4.2 (CP), U5.2 (CP), U6.2 (CP), U7.2 (CP), U8.2 (CP)
/ADDR_IN: J1.9 (ADDR_IN), U12.14 (SER)
/ADDR_LATCH: J1.4 (ADDR_LATCH), U9.12 (RCLK), U10.12 (RCLK), U11.12 (RCLK), U12.12 (RCLK), U18.1 (D)
/BUS_CLK: J1.2 (BUS_CLK), U9.11 (SRCLK), U10.11 (SRCLK), U11.11 (SRCLK), U12.11 (SRCLK), U13.11 (SRCLK), U14.11 (SRCLK)
/CLK: J1.13 (CLK), U15.3 (C), U15.11 (C), U18.2 (C)
/D0: J3.32 (D0), R1.2, U13.7 (QH), U14.7 (PH), U20.2 (D0)
/D1: J3.33 (D1), R2.2, U13.6 (QG), U14.6 (PG), U20.3 (D1)
/D1H: D1.2 (A), U20.19 (Q0)
/D1L: D1.1 (K), R9.1
/D2: J3.34 (D2), R3.2, U13.5 (QF), U14.5 (PF), U20.4 (D2)
/D2H: D2.2 (A), U20.18 (Q1)
/D2L: D2.1 (K), R10.1
/D3: J3.35 (D3), R4.2, U13.4 (QE), U14.4 (PE), U20.5 (D3)
/D3H: D3.2 (A), U20.17 (Q2)
/D3L: D3.1 (K), R11.1
/D4: J3.36 (D4), R5.2, U13.3 (QD), U14.3 (PD), U20.6 (D4)
/D4H: D4.2 (A), U20.16 (Q3)
/D4L: D4.1 (K), R12.1
/D5: J3.37 (D5), R6.2, U13.2 (QC), U14.2 (PC), U20.7 (D5)
/D5H: D5.2 (A), U20.15 (Q4)
/D5L: D5.1 (K), R13.1
/D6: J3.38 (D6), R7.2, U13.1 (QB), U14.1 (PB), U20.8 (D6)
/D6H: D6.2 (A), U20.14 (Q5)
/D6L: D6.1 (K), R14.1
/D7: J3.39 (D7), R8.2, U13.15 (QA), U14.15 (PA), U16.1 (D), U20.9 (D7)
/D7H: D7.2 (A), U20.13 (Q6)
/D7L: D7.1 (K), R15.1
/D8H: D8.2 (A), U20.12 (Q7)
/D8L: D8.1 (K), R16.1
/DIN_LATCH: U13.12 (RCLK), U15.8 (~Q)
/DOUT_LATCH: U14.12 (RCLK), U15.6 (~Q), U16.2 (C), U22.2
/LED_LATCH: U20.11 (Load), U21.4
/MEM_IN: J1.11 (MEM_IN), U13.14 (SER)
/MEM_OUT: J1.10 (MEM_OUT), U14.9 (QH')
/Q0: U1.3 (D0), U9.7 (QH)
/Q1: U1.4 (D1), U9.6 (QG)
/Q2: U1.5 (D2), U9.5 (QF)
/Q3: U1.6 (D3), U9.4 (QE)
/Q4: U2.3 (D0), U9.3 (QD)
/Q5: U2.4 (D1), U9.2 (QC)
/Q6: U2.5 (D2), U9.1 (QB)
/Q7: U2.6 (D3), U9.15 (QA)
/Q8: U3.3 (D0), U10.7 (QH)
/Q8': U9.14 (SER), U10.9 (QH')
/Q9: U3.4 (D1), U10.6 (QG)
/Q10: U3.5 (D2), U10.5 (QF)
/Q11: U3.6 (D3), U10.4 (QE)
/Q12: U4.3 (D0), U10.3 (QD)
/Q13: U4.4 (D1), U10.2 (QC)
/Q14: U4.5 (D2), U10.1 (QB)
/Q15: U4.6 (D3), U10.15 (QA)
/Q16: U5.3 (D0), U11.7 (QH)
/Q16': U10.14 (SER), U11.9 (QH')
/Q17: U5.4 (D1), U11.6 (QG)
/Q18: U5.5 (D2), U11.5 (QF)
/Q19: U5.6 (D3), U11.4 (QE)
/Q20: U6.3 (D0), U11.3 (QD)
/Q21: U6.4 (D1), U11.2 (QC)
/Q22: U6.5 (D2), U11.1 (QB)
/Q23: U6.6 (D3), U11.15 (QA)
/Q24: U7.3 (D0), U12.7 (QH)
/Q24': U11.14 (SER), U12.9 (QH')
/Q25: U7.4 (D1), U12.6 (QG)
/Q26: U7.5 (D2), U12.5 (QF)
/Q27: U7.6 (D3), U12.4 (QE)
/Q28: U8.3 (D0), U12.3 (QD)
/Q29: U8.4 (D1), U12.2 (QC)
/Q30: U8.5 (D2), U12.1 (QB)
/Q31: U8.6 (D3), U12.15 (QA)
/SIGN: U14.14 (SER), U17.4
/TC3: U1.15 (TC), U2.10 (CET)
/TC7: U2.15 (TC), U3.10 (CET)
/TC11: U3.15 (TC), U4.10 (CET)
/TC15: U4.15 (TC), U5.10 (CET)
/TC19: U5.15 (TC), U6.10 (CET)
/TC23: U6.15 (TC), U7.10 (CET)
/TC27: U7.15 (TC), U8.10 (CET)
/V_IN: C19.2, J2.1 (VCC), U19.1 (VIN), U19.3 (EN)
/~ADDR_PE: U1.9 (~PE), U2.9 (~PE), U3.9 (~PE), U4.9 (~PE), U5.9 (~PE), U6.9 (~PE), U7.9 (~PE), U8.9 (~PE), U18.4 (~Q)
/~DIN_OE: U13.13 (~OE), U15.9 (Q)
/~MEM_OE: J1.8 (~MEM_OE), J3.30 (~MEM_OE), U14.13 (S/~P), U15.2 (D), U22.1
/~MEM_WE: J1.7 (~MEM_WE), J3.31 (~MEM_WE), U15.12 (D), U15.13 (~R), U21.1
/~RESET: J1.12 (~RESET), J3.28 (~RESET), U1.1 (~MR), U2.1 (~MR), U3.1 (~MR), U4.1 (~MR), U5.1 (~MR), U6.1 (~MR), U7.1 (~MR), U8.1 (~MR), U9.10 (~SRCLR), U10.10 (~SRCLR), U11.10 (~SRCLR), U12.10 (~SRCLR), U13.10 (~SRCLR), U14.10 (~SRCLR), U15.4 (~S), U15.10 (~S)
/~SIGN?: U16.4 (~Q), U17.1
/~S_EXT: J1.6 (~S_EXT), U17.2
/~WAIT: J1.3 (~WAIT), J3.29 (~WAIT)
GND: C1.2, C2.2, C3.2, C4.2, C5.2, C6.2, C7.2, C8.2, C9.2, C10.2, C11.2, C12.2, C13.2, C14.2, C15.2, C16.2, C17.2, C18.2, C19.1, C20.2, C21.2, C22.1, C23.2, J1.1 (GND), J1.14 (GND), J2.2 (GND), J2.MP, J3.1 (GND), J3.40 (GND), R9.2, R10.2, R11.2, R12.2, R13.2, R14.2, R15.2, R16.2, TP1.1, U1.8 (GND), U2.8 (GND), U3.8 (GND), U4.8 (GND), U5.8 (GND), U6.8 (GND), U7.8 (GND), U8.8 (GND), U9.8 (GND), U9.13 (~OE), U10.8 (GND), U10.13 (~OE), U11.8 (GND), U11.13 (~OE), U12.8 (GND), U12.13 (~OE), U13.8 (GND), U14.8 (GND), U15.7 (GND), U16.3 (GND), U17.3 (GND), U18.3 (GND), U19.2 (GND), U20.1 (OE), U20.10 (GND), U21.3 (GND), U22.3 (GND)
unnamed: U21.2, U22.4
VCC: C1.1, C2.1, C3.1, C4.1, C5.1, C6.1, C7.1, C8.1, C9.1, C10.1, C11.1, C12.1, C13.1, C14.1, C15.1, C16.1, C17.1, C18.1, C20.1, C21.1, C22.2, C23.1, R1.1, R2.1, R3.1, R4.1, R5.1, R6.1, R7.1, R8.1, U1.7 (CEP), U1.10 (CET), U1.16 (VCC), U2.7 (CEP), U2.16 (VCC), U3.7 (CEP), U3.16 (VCC), U4.7 (CEP), U4.16 (VCC), U5.7 (CEP), U5.16 (VCC), U6.7 (CEP), U6.16 (VCC), U7.7 (CEP), U7.16 (VCC), U8.7 (CEP), U8.16 (VCC), U9.16 (VCC), U10.16 (VCC), U11.16 (VCC), U12.16 (VCC), U13.16 (VCC), U14.16 (VCC), U15.1 (~R), U15.14 (VCC), U16.5 (VCC), U17.5 (VCC), U18.5 (VCC), U19.5 (VOUT), U20.20 (VCC), U21.5 (VCC), U22.5 (VCC)

Notes on the sheet:
The sign bit is D7!
Meomory map 0x0XXXXXXX: ROM 0x4XXXXXXX: IO0 0x8XXXXXXX: RAM 0xCXXXXXXX: IO1

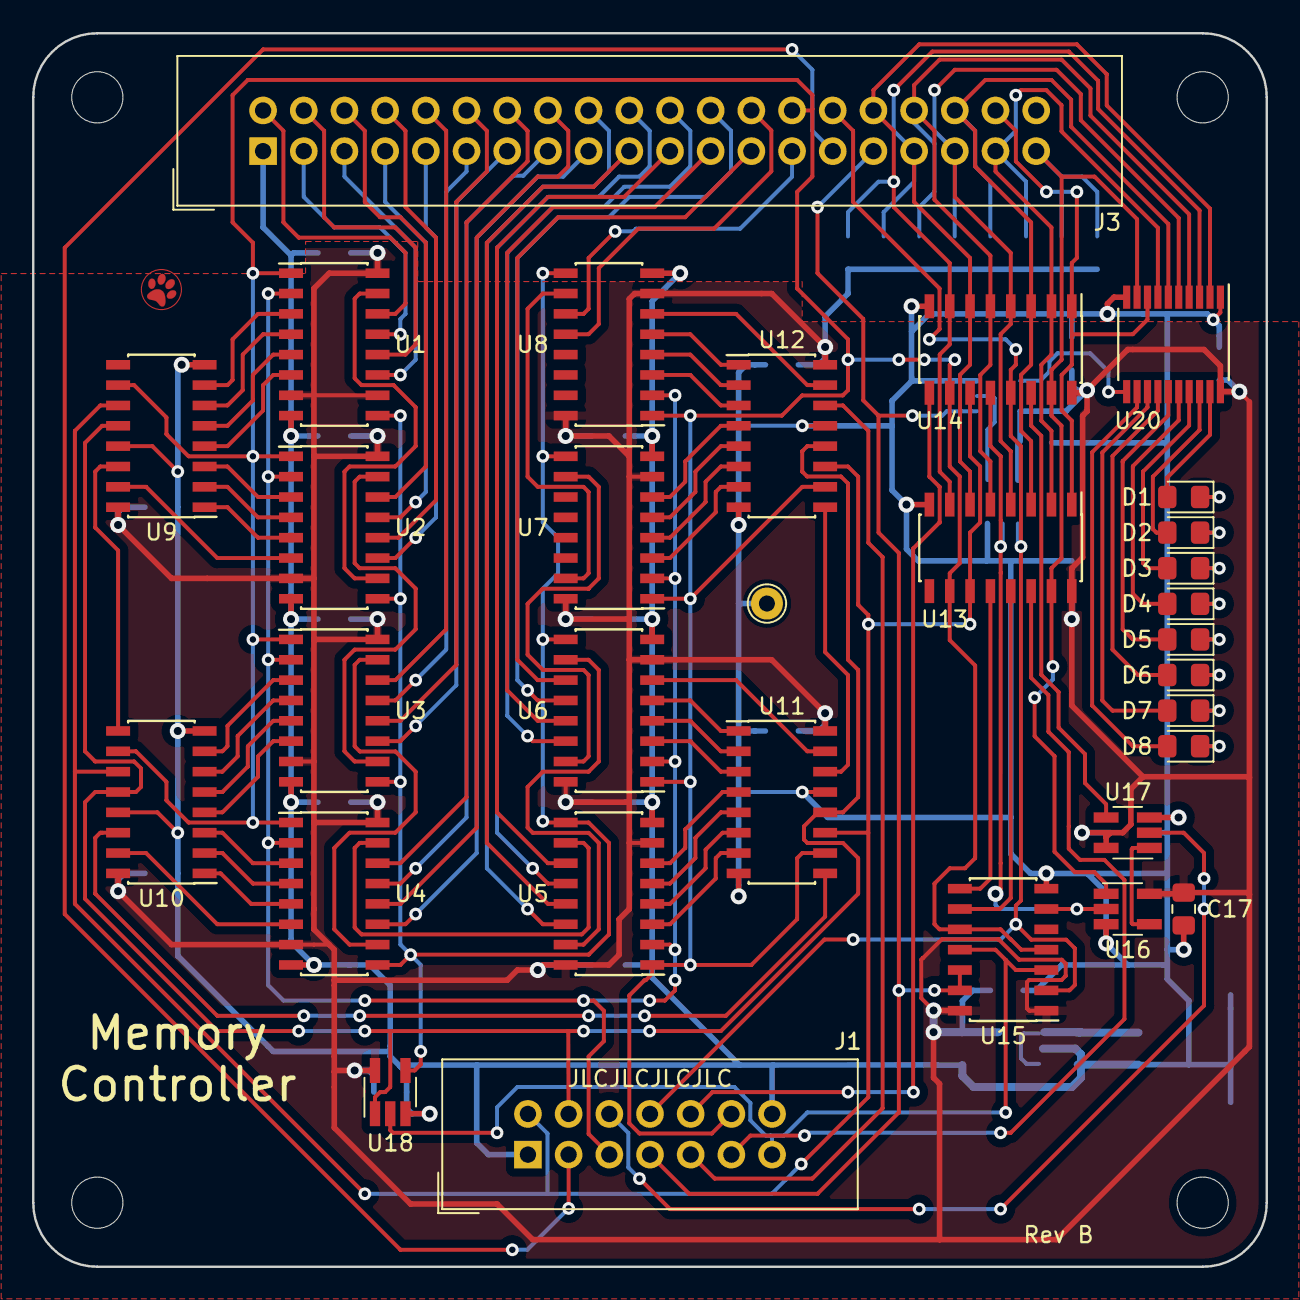
[picture p31: board memory.kicad_pcb from above]

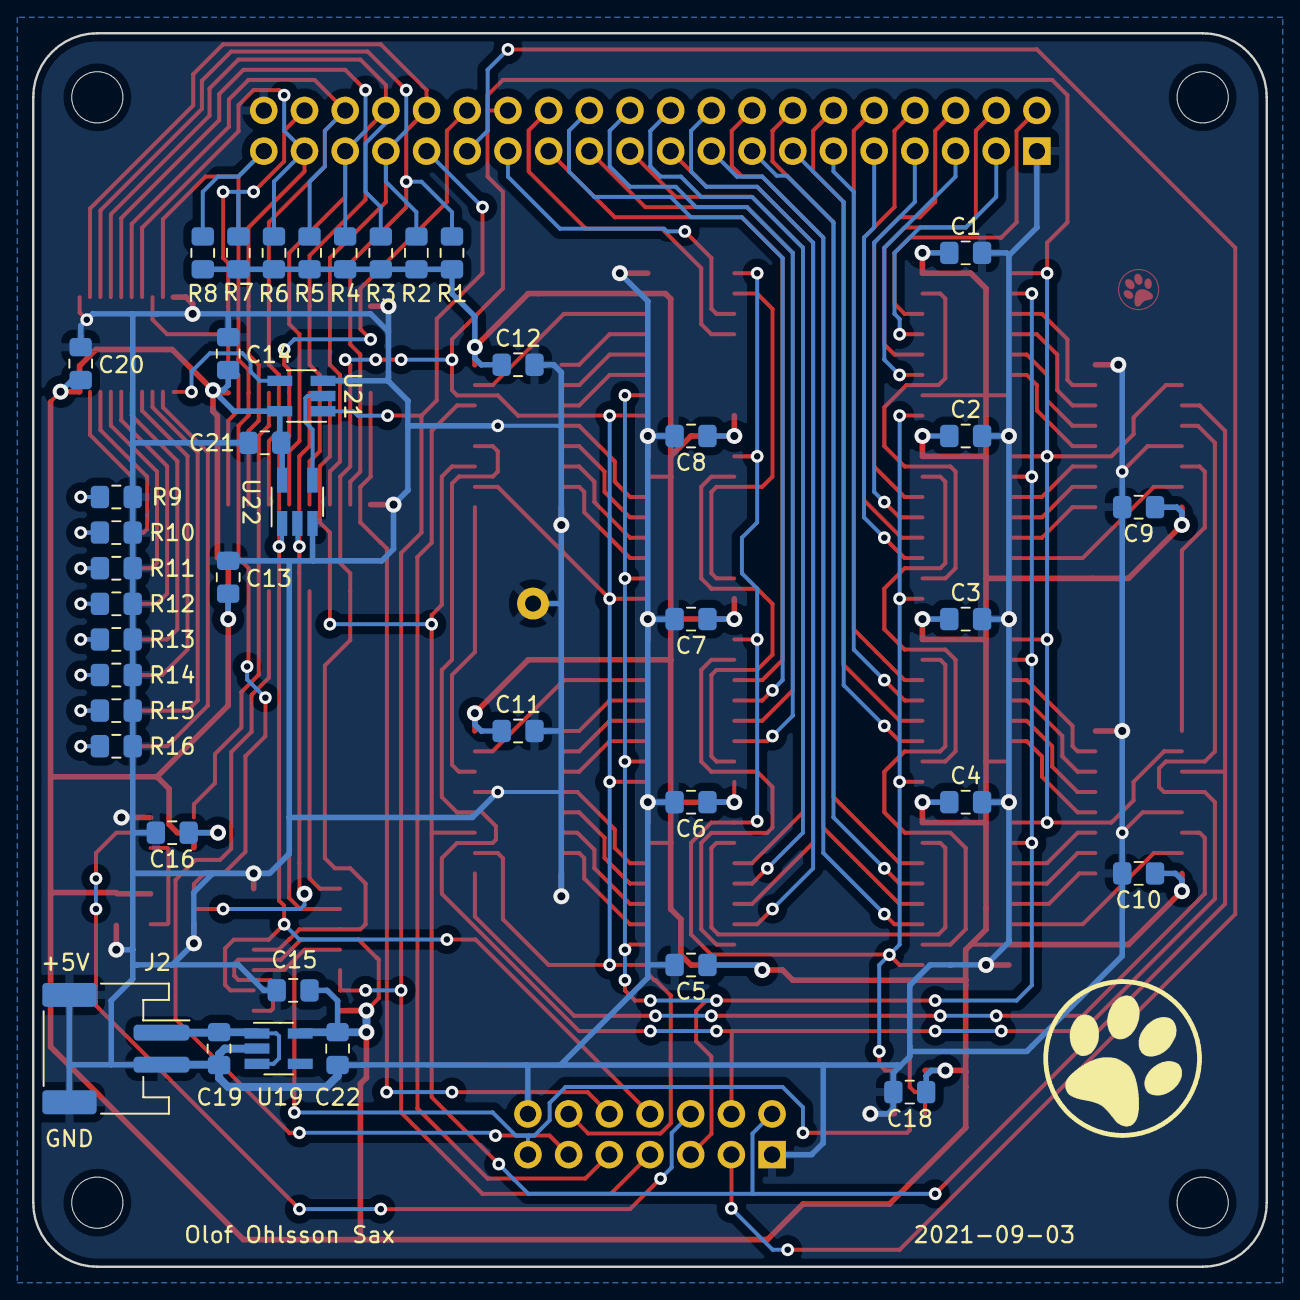
[picture p32: board memory.kicad_pcb from below]

Board: 2 copper layers, 77.0 x 77.0 mm, 76 parts (41 on the bottom side), 115 nets.
