olofos/rv321/hardware/memory-io/memory-io.kicad_pcb

## KiCad design hardware/memory-io/memory-io.kicad_pcb (2022-06-17)

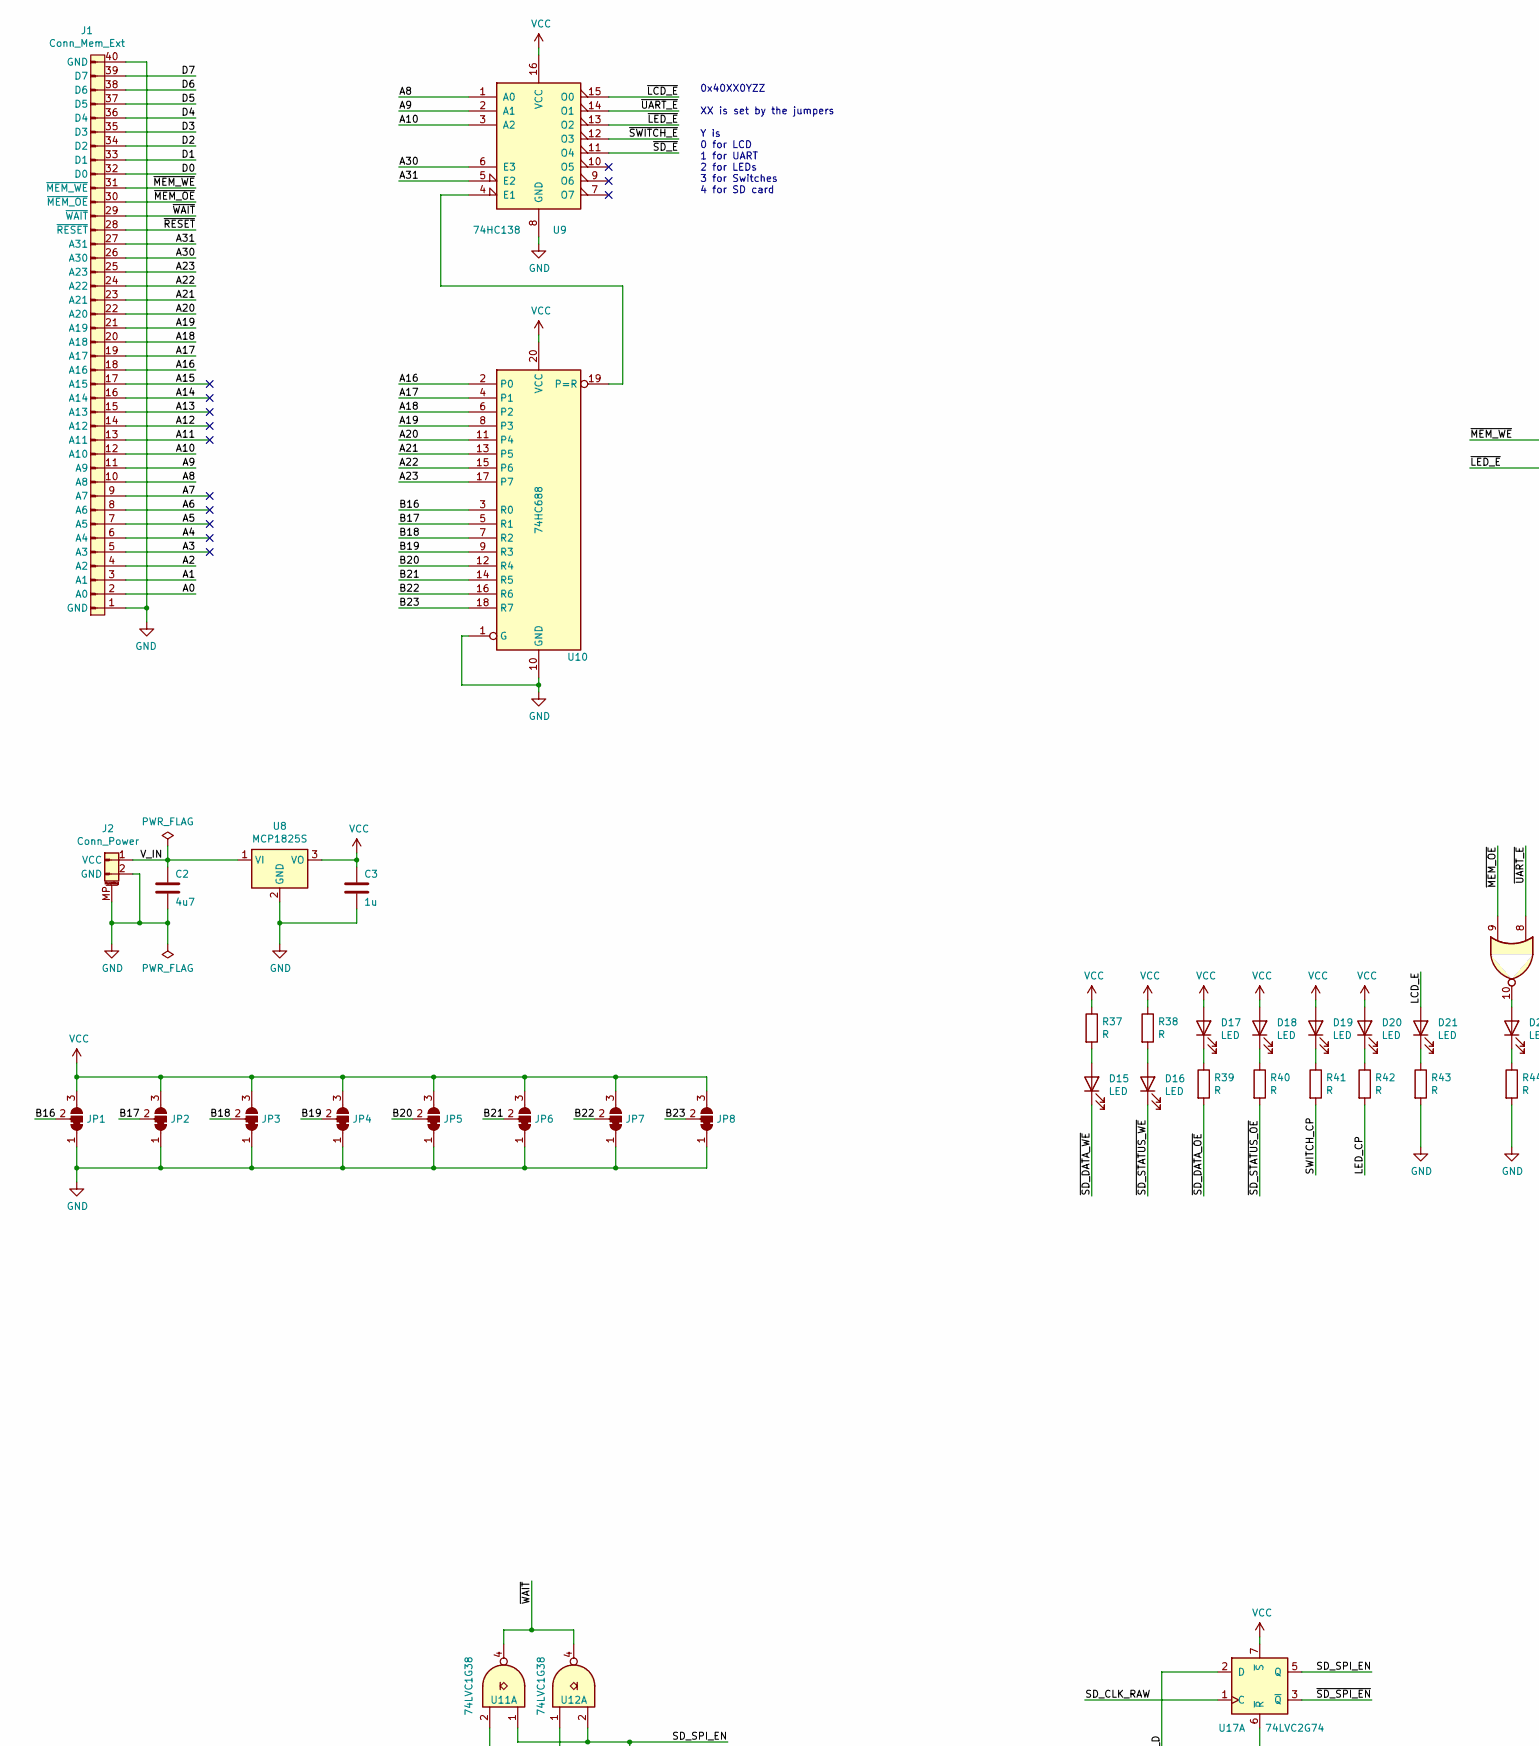
[picture p33: schematic memory-io.kicad_sch, part in row 1, column 1]

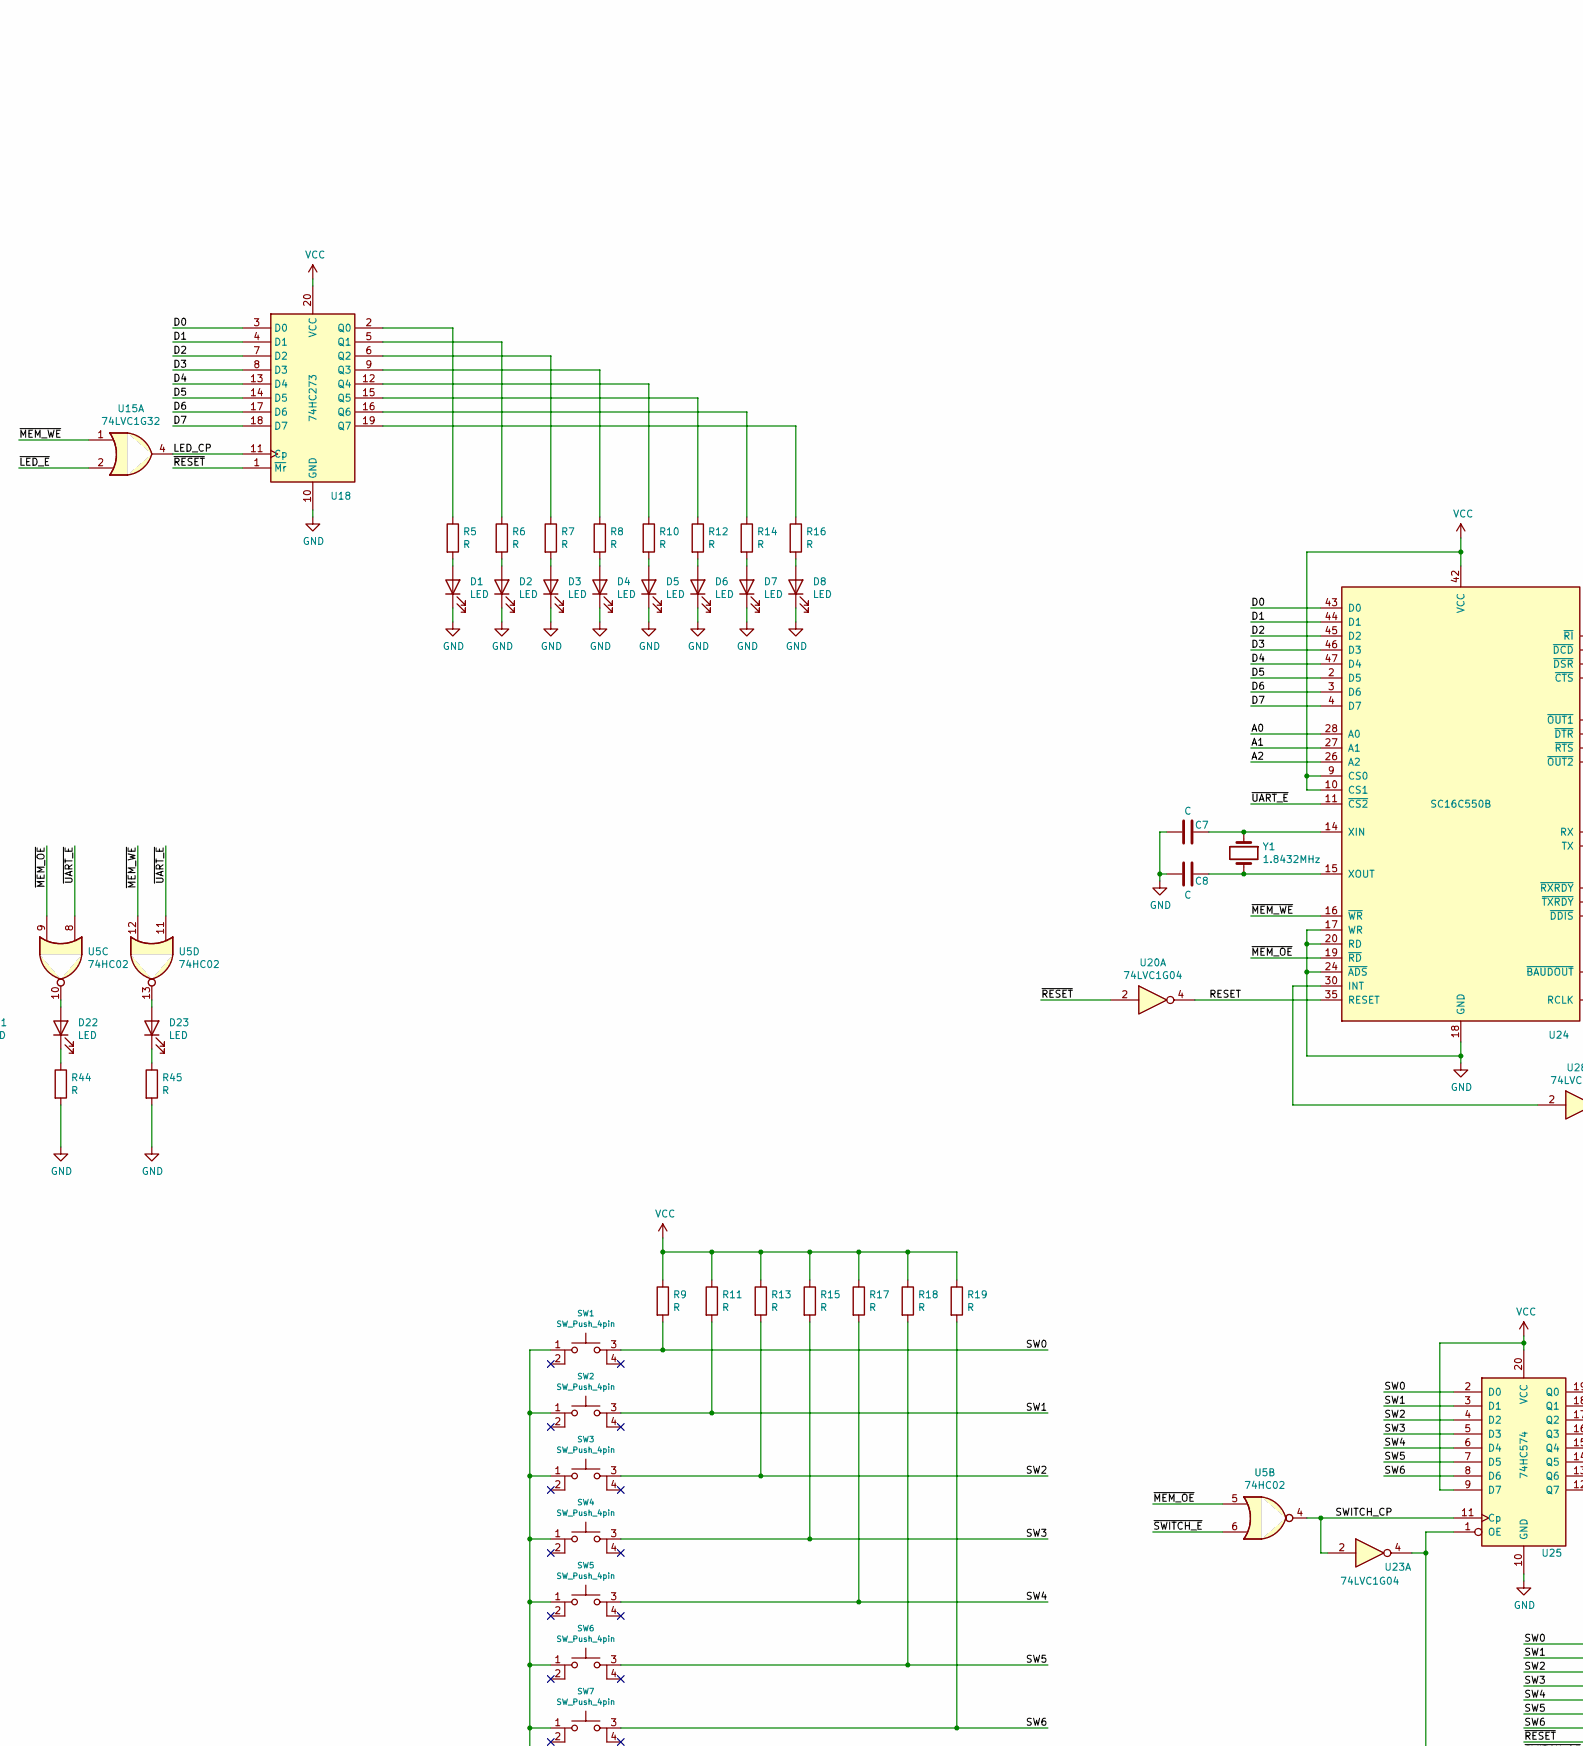
[picture p34: schematic memory-io.kicad_sch, part in row 1, column 2]

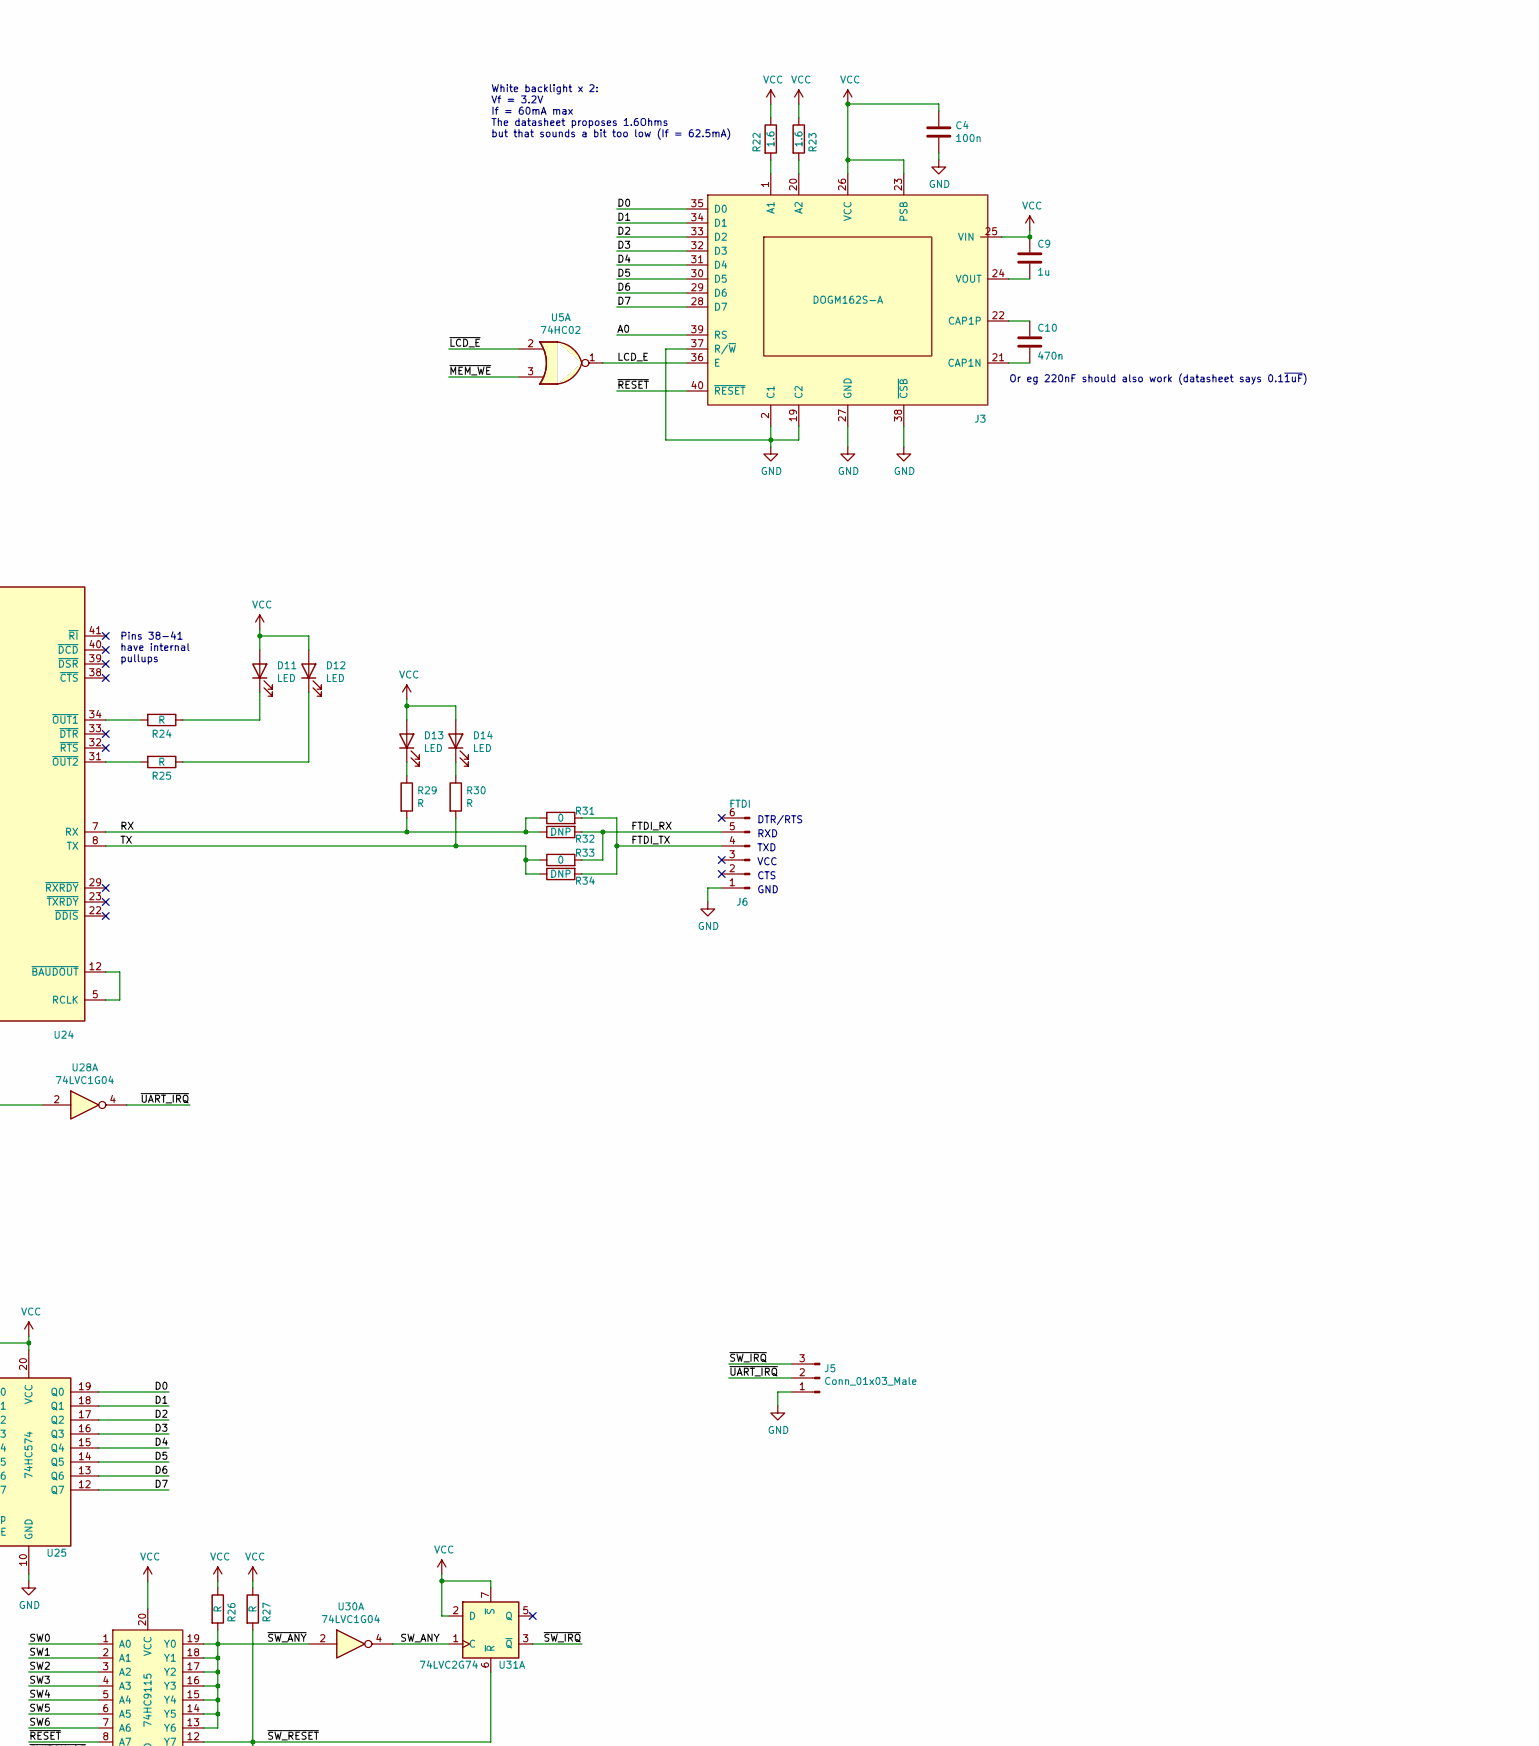
[picture p35: schematic memory-io.kicad_sch, part in row 1, column 3]

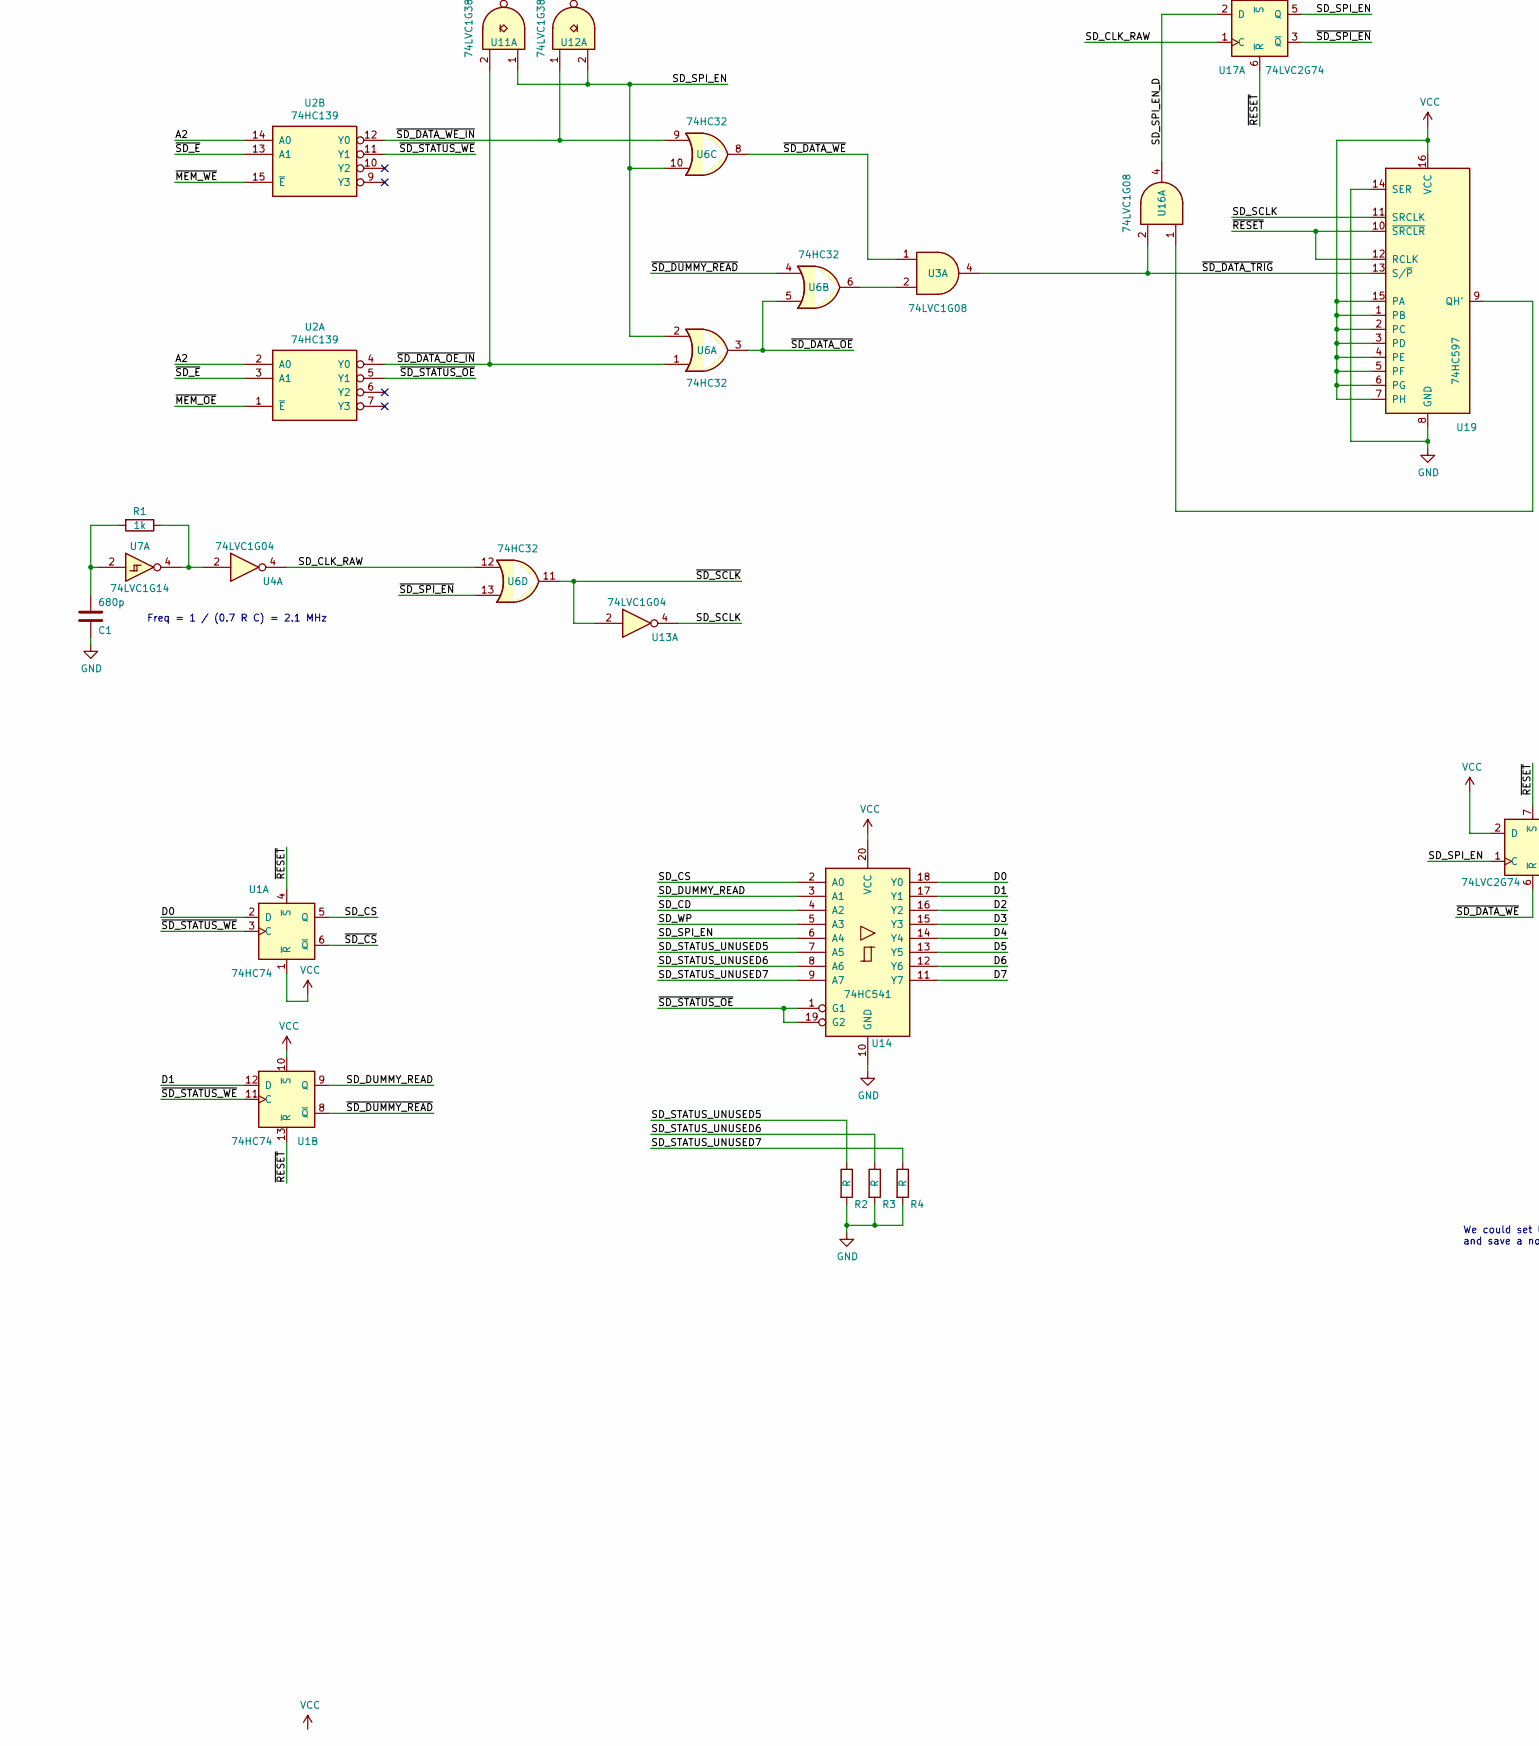
[picture p36: schematic memory-io.kicad_sch, part in row 2, column 1]

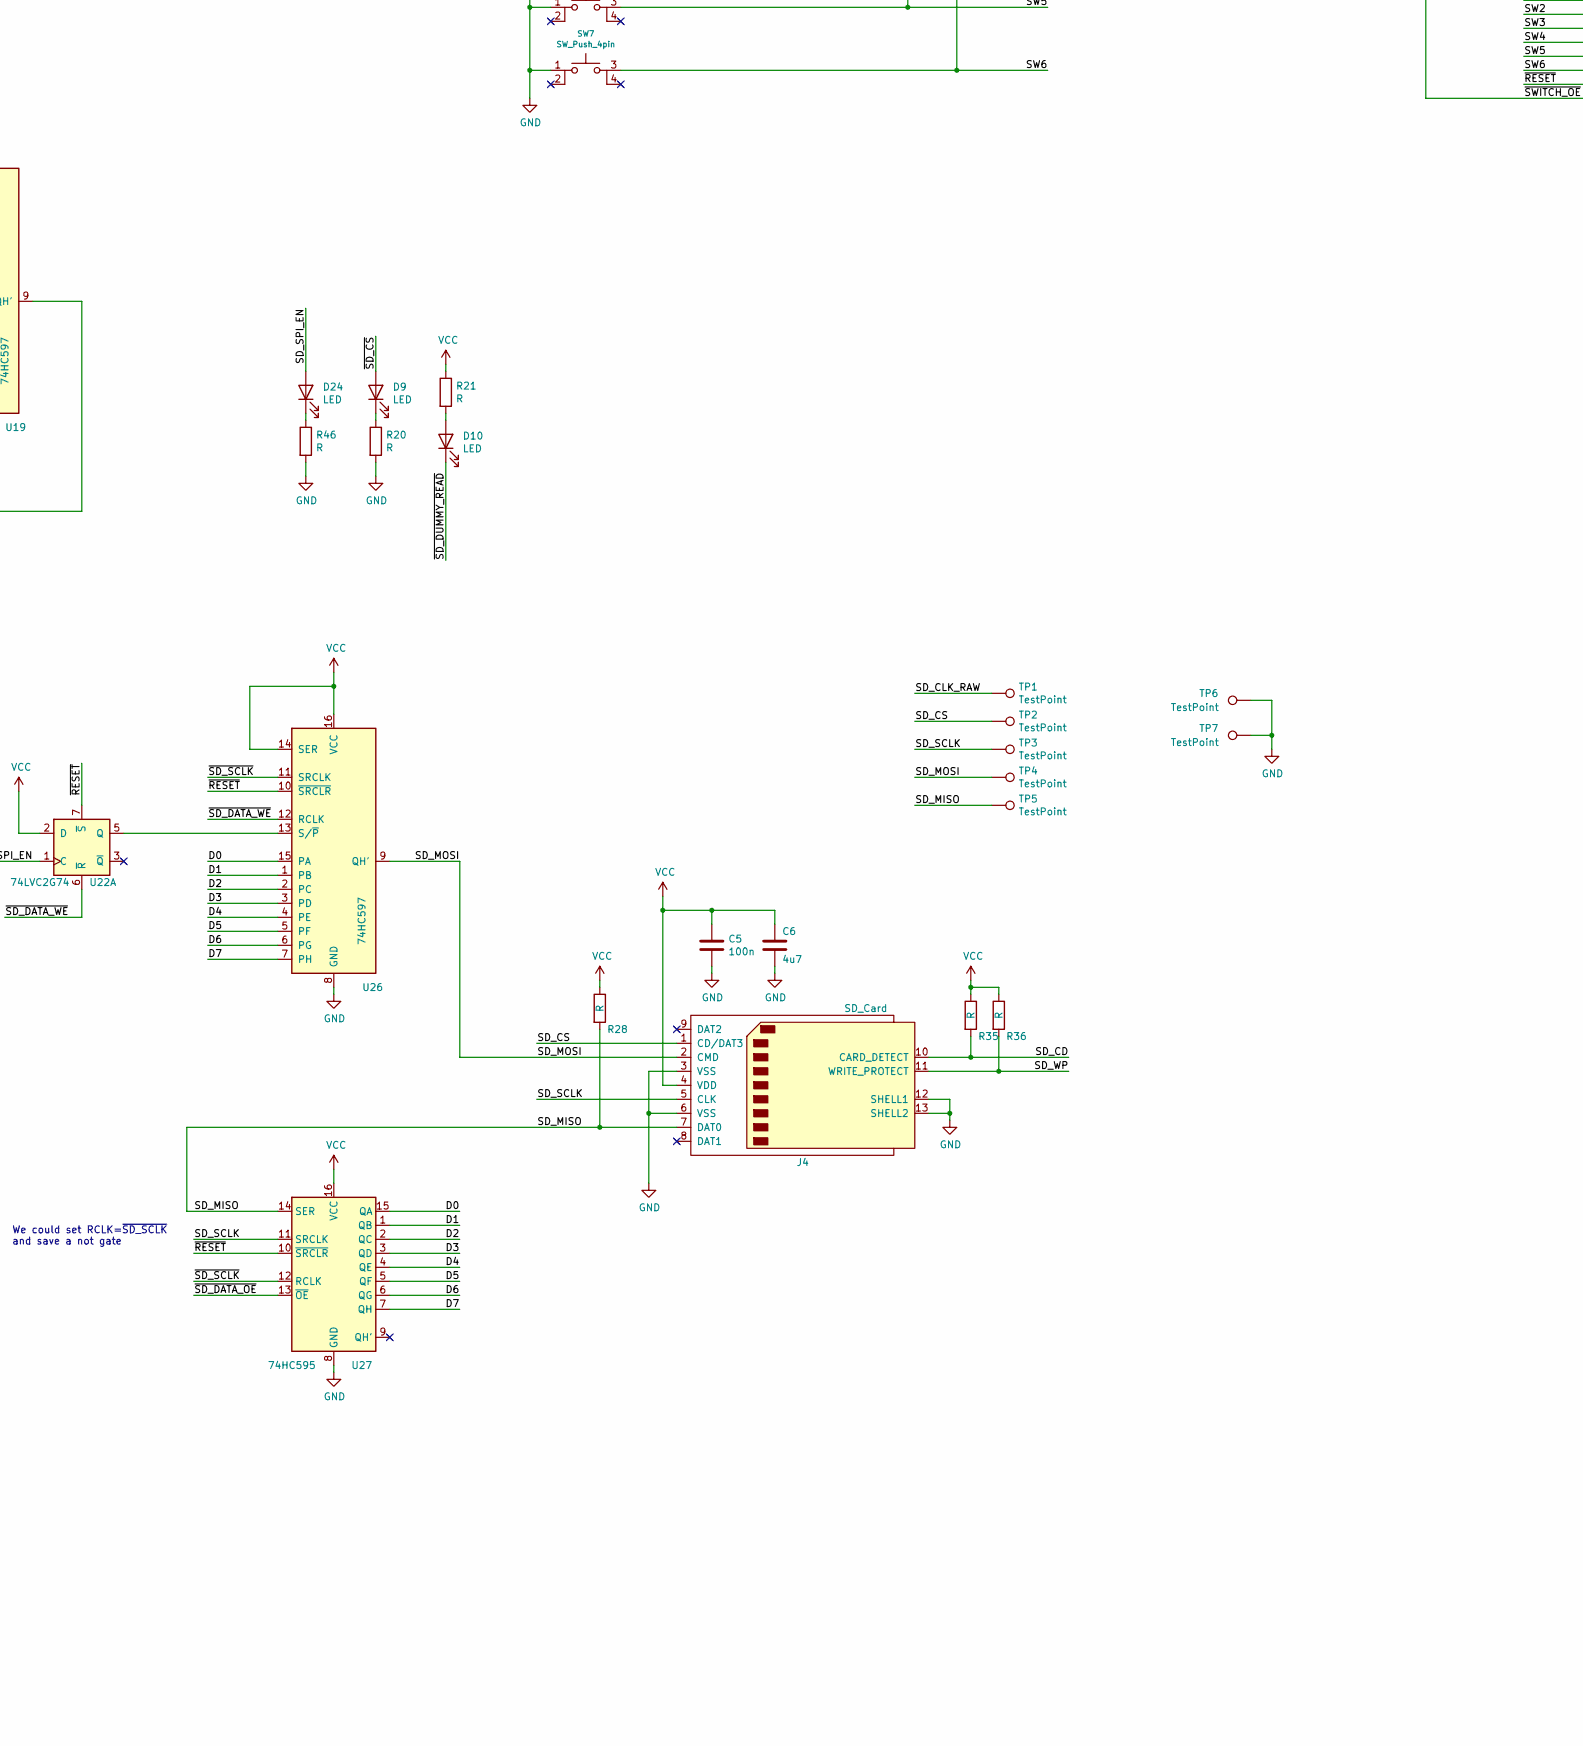
[picture p37: schematic memory-io.kicad_sch, part in row 2, column 2]

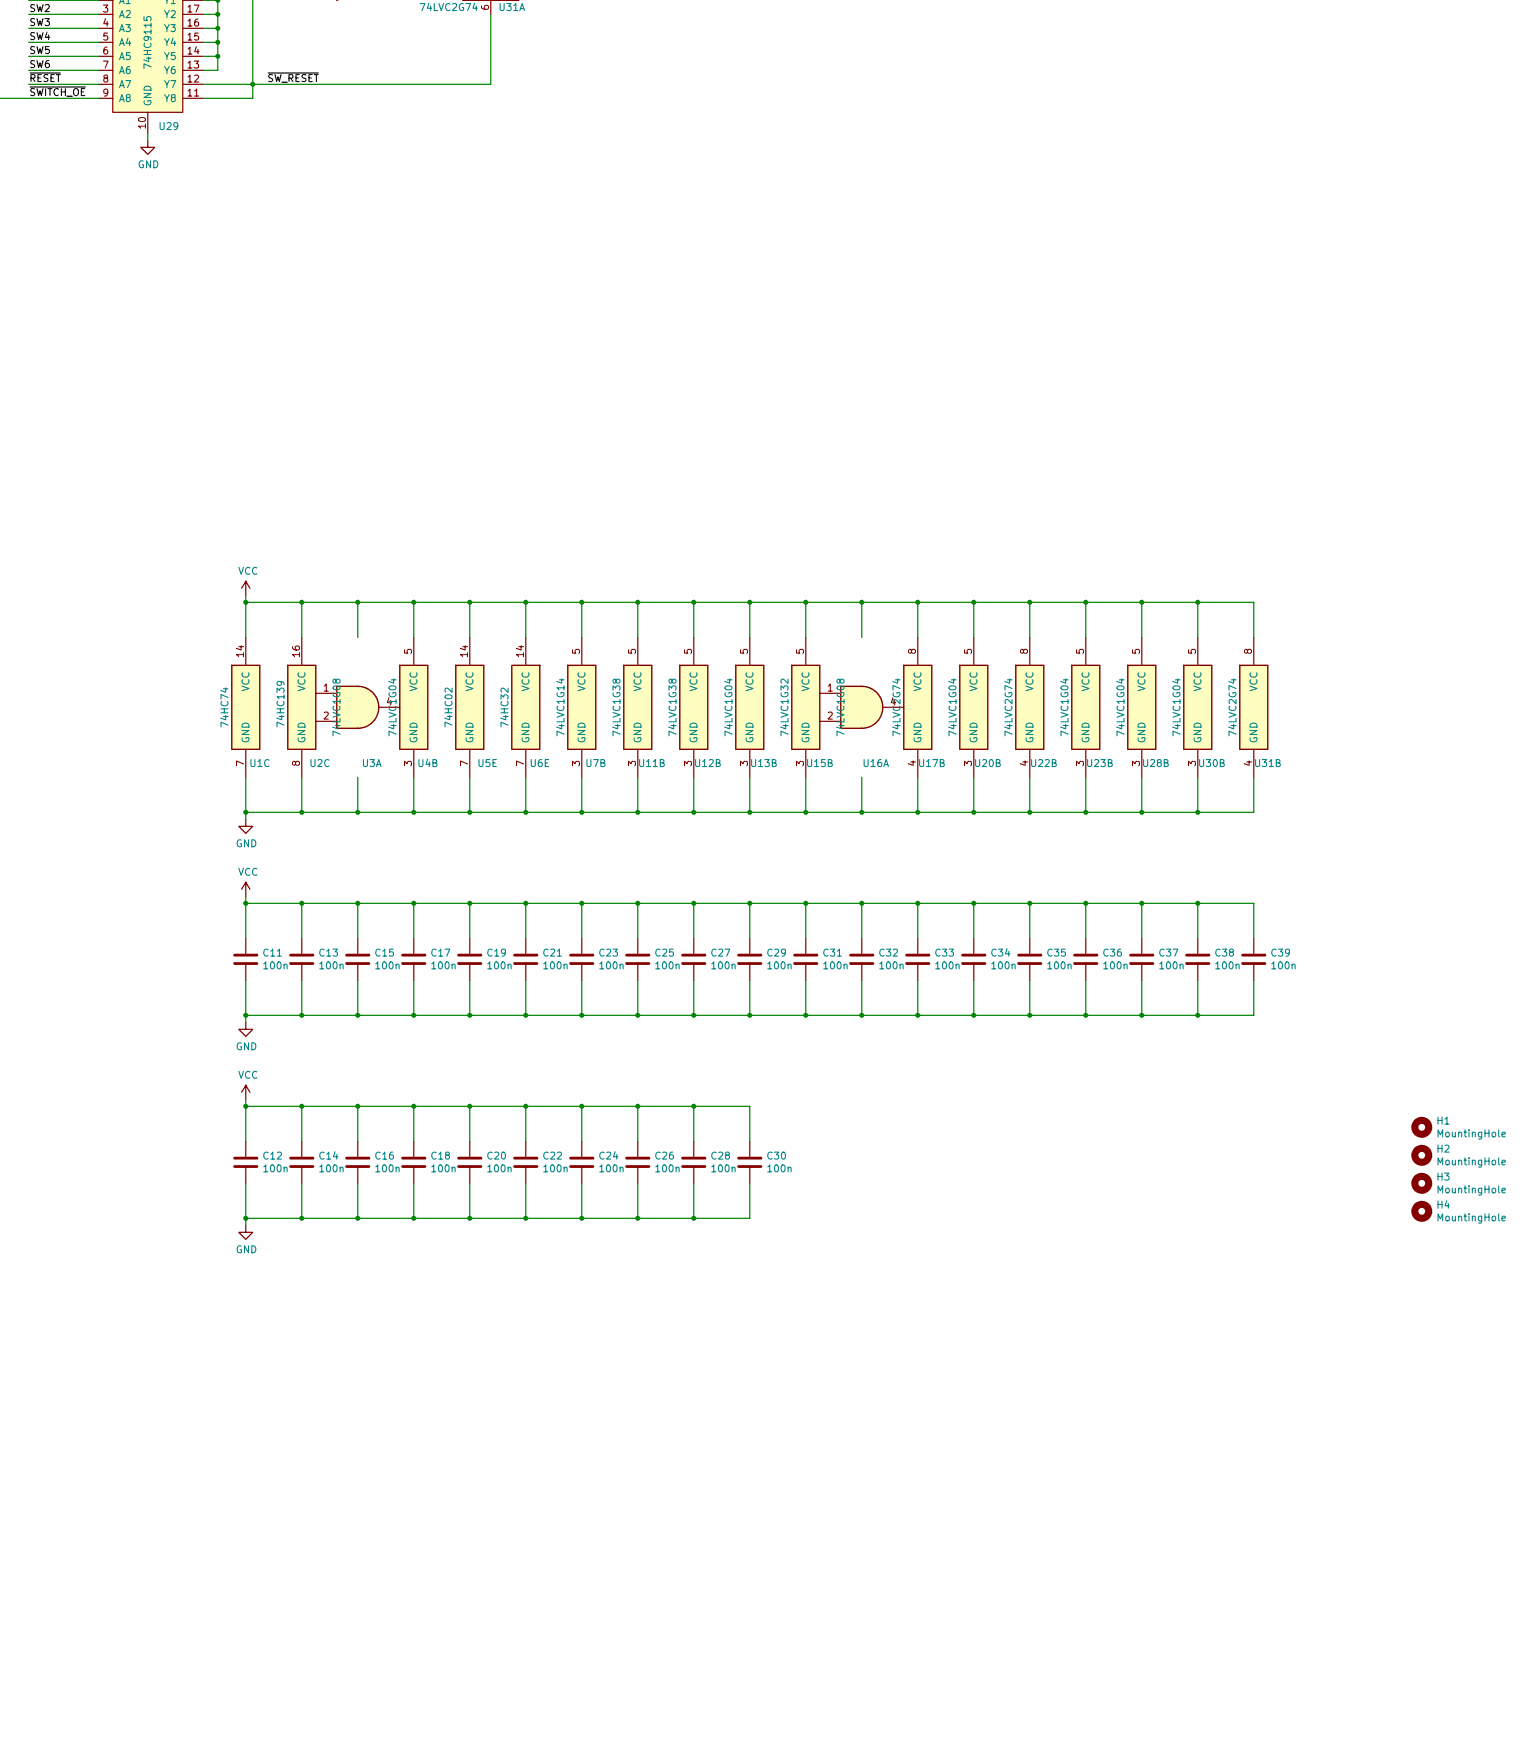
[picture p38: schematic memory-io.kicad_sch, part in row 2, column 3]

Parts:
C1: 680p; C_0805_2012Metric_Pad1.18x1.45mm_HandSolder
C2, C6: 4u7; C_0805_2012Metric_Pad1.18x1.45mm_HandSolder
C3, C9: 1u; C_0805_2012Metric_Pad1.18x1.45mm_HandSolder
C4, C5, C11, C12, C13, C14, C15, C16, C17, C18, C19, C20, C21, C22, C23, C24, C25, C26, C27, C28, C29, C30, C31, C32, C33, C34, C35, C36, C37, C38, C39: 100n; C_0805_2012Metric_Pad1.18x1.45mm_HandSolder
C7, C8: C; C_0805_2012Metric_Pad1.18x1.45mm_HandSolder
C10: 470n; C_0805_2012Metric_Pad1.18x1.45mm_HandSolder
D1, D2, D3, D4, D5, D6, D7, D8, D9, D10, D11, D12, D13, D14, D15, D16, D17, D18, D19, D20, D21, D22, D23, D24: LED; LED_0805_2012Metric_Pad1.15x1.40mm_HandSolder
H1, H2, H3, H4: MountingHole; MountingHole_3.2mm_M3
J1: Conn_Mem_Ext; IDC-Header_2x20_P2.54mm_Vertical
J2: Conn_Power; JST_PH_S2B-PH-SM4-TB_1x02-1MP_P2.00mm_Horizontal
J3: DOGM162S-A; EA-DOGM
J4: SD_Card; SD_Kyocera_145638009211859+
J5: Conn_01x03_Male; PinHeader_1x03_P2.54mm_Vertical
J6: FTDI; PinHeader_1x06_P2.54mm_Vertical
JP1, JP2, JP3, JP4, JP5, JP6, JP7, JP8: SolderJumper_3_Bridged12; SolderJumper-3_P1.3mm_Bridged2Bar12_RoundedPad1.0x1.5mm
R1: 1k; R_0805_2012Metric_Pad1.20x1.40mm_HandSolder
R2, R3, R4, R5, R6, R7, R8, R9, R10, R11, R12, R13, R14, R15, R16, R17, R18, R19, R20, R21, R24, R25, R26, R27, R28, R29, R30, R35, R36, R37, R38, R39, R40, R41, R42, R43, R44, R45, R46: R; R_0805_2012Metric_Pad1.20x1.40mm_HandSolder
R22, R23: 1.6; R_1206_3216Metric_Pad1.30x1.75mm_HandSolder
R31, R33: 0; R_0805_2012Metric_Pad1.20x1.40mm_HandSolder
R32, R34: DNP; R_0805_2012Metric_Pad1.20x1.40mm_HandSolder
SW1, SW2, SW3, SW4, SW5, SW6, SW7: SW_Push_4pin; SW_SPST_DTSM-6
TP1, TP2, TP3, TP4, TP5: TestPoint; TestPoint_THTPad_D1.5mm_Drill0.7mm
TP6, TP7: TestPoint; TestPoint_THTPad_D2.0mm_Drill1.0mm
U1: 74HC74; SOIC-14_3.9x8.7mm_P1.27mm
U2: 74HC139; SOIC-16_3.9x9.9mm_P1.27mm
U3, U16: 74LVC1G08; SOT-23-5_HandSoldering
U4, U13, U20, U23, U28, U30: 74LVC1G04; SOT-23-5_HandSoldering
U5: 74HC02; SOIC-14_3.9x8.7mm_P1.27mm
U6: 74HC32; SOIC-14_3.9x8.7mm_P1.27mm
U7: 74LVC1G14; SOT-23-5_HandSoldering
U8: MCP1825S; SOT-223-3_TabPin2
U9: 74HC138; SOIC-16_3.9x9.9mm_P1.27mm
U10: 74HC688; SOIC-20W_7.5x12.8mm_P1.27mm
U11, U12: 74LVC1G38; SOT-23-5_HandSoldering
U14: 74HC541; SOIC-20W_7.5x12.8mm_P1.27mm
U15: 74LVC1G32; SOT-23-5_HandSoldering
U17, U22: 74LVC2G74; SOT-23-8_Handsoldering
U18: 74HC273; SOIC-20W_7.5x12.8mm_P1.27mm
U19, U26: 74HC597; SOIC-16_3.9x9.9mm_P1.27mm
U24: SC16C550B; LQFP-48_7x7mm_P0.5mm
U25: 74HC574; SOIC-20W_7.5x12.8mm_P1.27mm
U27: 74HC595; SOIC-16_3.9x9.9mm_P1.27mm
U29: 74HC9115; SOIC-20W_7.5x12.8mm_P1.27mm
U31: 74LVC2G74; TSSOP-8_3x3mm_P0.65mm
Y1: 1.8432MHz; Crystal_HC49-U_Vertical

Connections:
/A0: J1.2 (A0), J3.39 (RS), U24.28 (A0)
/A1: J1.3 (A1), U24.27 (A1)
/A2: J1.4 (A2), U2.2 (A0), U2.14 (A0), U24.26 (A2)
/A3: J1.5 (A3)
/A4: J1.6 (A4)
/A5: J1.7 (A5)
/A6: J1.8 (A6)
/A7: J1.9 (A7)
/A8: J1.10 (A8), U9.1 (A0)
/A9: J1.11 (A9), U9.2 (A1)
/A10: J1.12 (A10), U9.3 (A2)
/A11: J1.13 (A11)
/A12: J1.14 (A12)
/A13: J1.15 (A13)
/A14: J1.16 (A14)
/A15: J1.17 (A15)
/A16: J1.18 (A16), U10.2 (P0)
/A17: J1.19 (A17), U10.4 (P1)
/A18: J1.20 (A18), U10.6 (P2)
/A19: J1.21 (A19), U10.8 (P3)
/A20: J1.22 (A20), U10.11 (P4)
/A21: J1.23 (A21), U10.13 (P5)
/A22: J1.24 (A22), U10.15 (P6)
/A23: J1.25 (A23), U10.17 (P7)
/A30: J1.26 (A30), U9.6 (E3)
/A31: J1.27 (A31), U9.5 (E2)
/B16: JP1.2 (C), U10.3 (R0)
/B17: JP2.2 (C), U10.5 (R1)
/B18: JP3.2 (C), U10.7 (R2)
/B19: JP4.2 (C), U10.9 (R3)
/B20: JP5.2 (C), U10.12 (R4)
/B21: JP6.2 (C), U10.14 (R5)
/B22: JP7.2 (C), U10.16 (R6)
/B23: JP8.2 (C), U10.18 (R7)
/D0: J1.32 (D0), J3.35 (D0), U1.2 (D), U14.18 (Y0), U18.3 (D0), U24.43 (D0), U25.19 (Q0), U26.15 (PA), U27.15 (QA)
/D1: J1.33 (D1), J3.34 (D1), U1.12 (D), U14.17 (Y1), U18.4 (D1), U24.44 (D1), U25.18 (Q1), U26.1 (PB), U27.1 (QB)
/D2: J1.34 (D2), J3.33 (D2), U14.16 (Y2), U18.7 (D2), U24.45 (D2), U25.17 (Q2), U26.2 (PC), U27.2 (QC)
/D3: J1.35 (D3), J3.32 (D3), U14.15 (Y3), U18.8 (D3), U24.46 (D3), U25.16 (Q3), U26.3 (PD), U27.3 (QD)
/D4: J1.36 (D4), J3.31 (D4), U14.14 (Y4), U18.13 (D4), U24.47 (D4), U25.15 (Q4), U26.4 (PE), U27.4 (QE)
/D5: J1.37 (D5), J3.30 (D5), U14.13 (Y5), U18.14 (D5), U24.2 (D5), U25.14 (Q5), U26.5 (PF), U27.5 (QF)
/D6: J1.38 (D6), J3.29 (D6), U14.12 (Y6), U18.17 (D6), U24.3 (D6), U25.13 (Q6), U26.6 (PG), U27.6 (QG)
/D7: J1.39 (D7), J3.28 (D7), U14.11 (Y7), U18.18 (D7), U24.4 (D7), U25.12 (Q7), U26.7 (PH), U27.7 (QH)
/FTDI_RX: J6.5, R32.2, R33.2
/FTDI_TX: J6.4, R31.2, R34.2
/LCD_E: D21.2 (A), J3.36 (E), U5.1
/LED_CP: R42.2, U15.4, U18.11 (Cp)
/RESET: U20.4, U24.35 (RESET)
/RX: R29.2, R31.1, R32.1, U24.7 (RX)
/SD_CD: J4.10 (CARD_DETECT), R35.2, U14.4 (A2)
/SD_CLK_RAW: TP1.1, U4.4, U6.12, U17.1 (C)
/SD_CS: J4.1 (CD/DAT3), TP2.1, U1.5 (Q), U14.2 (A0)
/SD_DUMMY_READ: U1.9 (Q), U14.3 (A1)
/SD_MISO: J4.7 (DAT0), R28.2, TP5.1, U27.14 (SER)
/SD_MOSI: J4.2 (CMD), TP4.1, U26.9 (QH')
/SD_SCLK: J4.5 (CLK), TP3.1, U13.4, U19.11 (SRCLK), U27.11 (SRCLK)
/SD_SPI_EN: D24.2 (A), U6.2, U6.10, U11.1, U12.2, U14.6 (A4), U17.5 (Q), U22.1 (C)
/SD_SPI_EN_D: U16.4, U17.2 (D)
/SD_STATUS_UNUSED5: R2.1, U14.7 (A5)
/SD_STATUS_UNUSED6: R3.1, U14.8 (A6)
/SD_STATUS_UNUSED7: R4.1, U14.9 (A7)
/SD_WP: J4.11 (WRITE_PROTECT), R36.2, U14.5 (A3)
/SW0: R9.2, SW1.3, U25.2 (D0), U29.1 (A0)
/SW1: R11.2, SW2.3, U25.3 (D1), U29.2 (A1)
/SW2: R13.2, SW3.3, U25.4 (D2), U29.3 (A2)
/SW3: R15.2, SW4.3, U25.5 (D3), U29.4 (A3)
/SW4: R17.2, SW5.3, U25.6 (D4), U29.5 (A4)
/SW5: R18.2, SW6.3, U25.7 (D5), U29.6 (A5)
/SW6: R19.2, SW7.3, U25.8 (D6), U29.7 (A6)
/SWITCH_CP: R41.2, U5.4, U23.2, U25.11 (Cp)
/SW_ANY: U30.4, U31.1 (C)
/TX: R30.2, R33.1, R34.1, U24.8 (TX)
/V_IN: C2.2, J2.1 (VCC), U8.1 (VI)
/~LCD_E: U5.2, U9.15 (O0)
/~LED_E: U9.13 (O2), U15.2
/~MEM_OE: J1.30 (~MEM_OE), U2.1 (~E), U5.5, U5.9, U24.19 (~RD)
/~MEM_WE: J1.31 (~MEM_WE), U2.15 (~E), U5.3, U5.12, U15.1, U24.16 (~WR)
/~RESET: J1.28 (~RESET), J3.40 (~RESET), U1.4 (~S), U1.13 (~R), U17.6 (~R), U18.1 (~Mr), U19.10 (~SRCLR), U19.12 (RCLK), U20.2, U22.7 (~S), U26.10 (~SRCLR), U27.10 (~SRCLR), U29.8 (A7)
/~SD_CS: D9.2 (A), U1.6 (~Q)
/~SD_DATA_OE_IN: U2.4 (Y0), U6.1, U11.2
/~SD_DATA_OE: R39.2, U6.3, U6.5, U27.13 (~OE)
/~SD_DATA_TRIG: U3.4, U16.2, U19.13 (S/~P)
/~SD_DATA_WE_IN: U2.12 (Y0), U6.9, U12.1
/~SD_DATA_WE: D15.1 (K), U3.1, U6.8, U22.6 (~R), U26.12 (RCLK)
/~SD_DUMMY_READ: D10.1 (K), U1.8 (~Q), U6.4
/~SD_E: U2.3 (A1), U2.13 (A1), U9.11 (O4)
/~SD_SCLK: U6.11, U13.2, U26.11 (SRCLK), U27.12 (RCLK)
/~SD_SPI_EN: U6.13, U17.3 (~Q)
/~SD_STATUS_OE: R40.2, U2.5 (Y1), U14.1 (G1), U14.19 (G2)
/~SD_STATUS_WE: D16.1 (K), U1.3 (C), U1.11 (C), U2.11 (Y1)
/~SWITCH_E: U5.6, U9.12 (O3)
/~SWITCH_OE: U23.4, U25.1 (OE), U29.9 (A8)
/~SW_ANY: R26.2, U29.13 (Y6), U29.14 (Y5), U29.15 (Y4), U29.16 (Y3), U29.17 (Y2), U29.18 (Y1), U29.19 (Y0), U30.2
/~SW_IRQ: J5.3, U31.3 (~Q)
/~SW_RESET: R27.2, U29.11 (Y8), U29.12 (Y7), U31.6 (~R)
/~UART_E: U5.8, U5.11, U9.14 (O1), U24.11 (~CS2)
/~UART_IRQ: J5.2, U28.4
/~WAIT: J1.29 (~WAIT), U11.4, U12.4
GND: C1.2, C2.1, C3.1, C4.2, C5.2, C6.1, C7.2, C8.2, C11.2, C12.2, C13.2, C14.2, C15.2, C16.2, C17.2, C18.2, C19.2, C20.2, C21.2, C22.2, C23.2, C24.2, C25.2, C26.2, C27.2, C28.2, C29.2, C30.2, C31.2, C32.2, C33.2, C34.2, C35.2, C36.2, C37.2, C38.2, C39.2, D1.1 (K), D2.1 (K), D3.1 (K), D4.1 (K), D5.1 (K), D6.1 (K), D7.1 (K), D8.1 (K), J1.1 (GND), J1.40 (GND), J2.2 (GND), J2.MP, J3.2 (C1), J3.19 (C2), J3.27 (GND), J3.37 (R/~W), J3.38 (~CSB), J4.3 (VSS), J4.6 (VSS), J4.12 (SHELL1), J4.13 (SHELL2), J5.1, J6.1, JP1.1 (A), JP2.1 (A), JP3.1 (A), JP4.1 (A), JP5.1 (A), JP6.1 (A), JP7.1 (A), JP8.1 (A), R2.2, R3.2, R4.2, R20.2, R43.2, R44.2, R45.2, R46.2, SW1.1, SW2.1, SW3.1, SW4.1, SW5.1, SW6.1, SW7.1, TP6.1, TP7.1, U1.7 (GND), U2.8 (GND), U3.3 (GND), U4.3 (GND), U5.7 (GND), U6.7 (GND), U7.3 (GND), U8.2 (GND), U9.8 (GND), U10.1 (G), U10.10 (GND), U11.3 (GND), U12.3 (GND), U13.3 (GND), U14.10 (GND), U15.3 (GND), U16.3 (GND), U17.4 (GND), U18.10 (GND), U19.8 (GND), U19.14 (SER), U20.3 (GND), U22.4 (GND), U23.3 (GND), U24.17 (WR), U24.18 (GND), U24.20 (RD), U24.24 (~ADS), U25.10 (GND), U26.8 (GND), U27.8 (GND), U28.3 (GND), U29.10 (GND), U30.3 (GND), U31.4 (GND)
unnamed: C1.1, R1.2, U7.2
unnamed: C7.1, U24.14 (XIN), Y1.1
unnamed: C8.1, U24.15 (XOUT), Y1.2
unnamed: C9.1, J3.24 (VOUT)
unnamed: C10.1, J3.21 (CAP1N)
unnamed: C10.2, J3.22 (CAP1P)
unnamed: D1.2 (A), R5.2
unnamed: D2.2 (A), R6.2
unnamed: D3.2 (A), R7.2
unnamed: D4.2 (A), R8.2
unnamed: D5.2 (A), R10.2
unnamed: D6.2 (A), R12.2
unnamed: D7.2 (A), R14.2
unnamed: D8.2 (A), R16.2
unnamed: D9.1 (K), R20.1
unnamed: D10.2 (A), R21.2
unnamed: D11.1 (K), R24.1
unnamed: D12.1 (K), R25.1
unnamed: D13.1 (K), R29.1
unnamed: D14.1 (K), R30.1
unnamed: D15.2 (A), R37.2
unnamed: D16.2 (A), R38.2
unnamed: D17.1 (K), R39.1
unnamed: D18.1 (K), R40.1
unnamed: D19.1 (K), R41.1
unnamed: D20.1 (K), R42.1
unnamed: D21.1 (K), R43.1
unnamed: D22.1 (K), R44.1
unnamed: D22.2 (A), U5.10
unnamed: D23.1 (K), R45.1
unnamed: D23.2 (A), U5.13
unnamed: D24.1 (K), R46.1
unnamed: J3.1 (A1), R22.2
unnamed: J3.20 (A2), R23.2
unnamed: R1.1, U4.2, U7.4
unnamed: R5.1, U18.2 (Q0)
unnamed: R6.1, U18.5 (Q1)
unnamed: R7.1, U18.6 (Q2)
unnamed: R8.1, U18.9 (Q3)
unnamed: R10.1, U18.12 (Q4)
unnamed: R12.1, U18.15 (Q5)
unnamed: R14.1, U18.16 (Q6)
unnamed: R16.1, U18.19 (Q7)
unnamed: R24.2, U24.34 (~OUT1)
unnamed: R25.2, U24.31 (~OUT2)
unnamed: U3.2, U6.6
unnamed: U9.4 (E1), U10.19 (P=R)
unnamed: U16.1, U19.9 (QH')
unnamed: U22.5 (Q), U26.13 (S/~P)
unnamed: U24.5 (RCLK), U24.12 (~BAUDOUT)
unnamed: U24.30 (INT), U28.2
VCC: C3.2, C4.1, C5.1, C6.2, C9.2, C11.1, C12.1, C13.1, C14.1, C15.1, C16.1, C17.1, C18.1, C19.1, C20.1, C21.1, C22.1, C23.1, C24.1, C25.1, C26.1, C27.1, C28.1, C29.1, C30.1, C31.1, C32.1, C33.1, C34.1, C35.1, C36.1, C37.1, C38.1, C39.1, D11.2 (A), D12.2 (A), D13.2 (A), D14.2 (A), D17.2 (A), D18.2 (A), D19.2 (A), D20.2 (A), J3.23 (PSB), J3.25 (VIN), J3.26 (VCC), J4.4 (VDD), JP1.3 (B), JP2.3 (B), JP3.3 (B), JP4.3 (B), JP5.3 (B), JP6.3 (B), JP7.3 (B), JP8.3 (B), R9.1, R11.1, R13.1, R15.1, R17.1, R18.1, R19.1, R21.1, R22.1, R23.1, R26.1, R27.1, R28.1, R35.1, R36.1, R37.1, R38.1, U1.1 (~R), U1.10 (~S), U1.14 (VCC), U2.16 (VCC), U3.5 (VCC), U4.5 (VCC), U5.14 (VCC), U6.14 (VCC), U7.5 (VCC), U8.3 (VO), U9.16 (VCC), U10.20 (VCC), U11.5 (VCC), U12.5 (VCC), U13.5 (VCC), U14.20 (VCC), U15.5 (VCC), U16.5 (VCC), U17.7 (~S), U17.8 (VCC), U18.20 (VCC), U19.1 (PB), U19.2 (PC), U19.3 (PD), U19.4 (PE), U19.5 (PF), U19.6 (PG), U19.7 (PH), U19.15 (PA), U19.16 (VCC), U20.5 (VCC), U22.2 (D), U22.8 (VCC), U23.5 (VCC), U24.9 (CS0), U24.10 (CS1), U24.42 (VCC), U25.9 (D7), U25.20 (VCC), U26.14 (SER), U26.16 (VCC), U27.16 (VCC), U28.5 (VCC), U29.20 (VCC), U30.5 (VCC), U31.2 (D), U31.7 (~S), U31.8 (VCC)

Notes on the sheet:
TXD
CTS
Pins 38-41 have internal pullups
GND
White backlight x 2: Vf = 3.2V If = 60mA max The datasheet proposes 1.6Ohms but that sounds a bit too low (If = 62.5mA)
RXD
We could set RCLK=~{SD_SCLK} and save a not gate
DTR/RTS
0x40XX0YZZ XX is set by the jumpers Y is 0 for LCD 1 for UART 2 for LEDs 3 for Switches 4 for SD card
Freq = 1 / (0.7 R C) = 2.1 MHz
VCC
Or eg 220nF should also work (datasheet says 0.1~{1uF})
