olofos/rv321/hardware/memory-io/memory-io.kicad_pcb

## KiCad design hardware/memory-io/memory-io.kicad_pcb (continued)

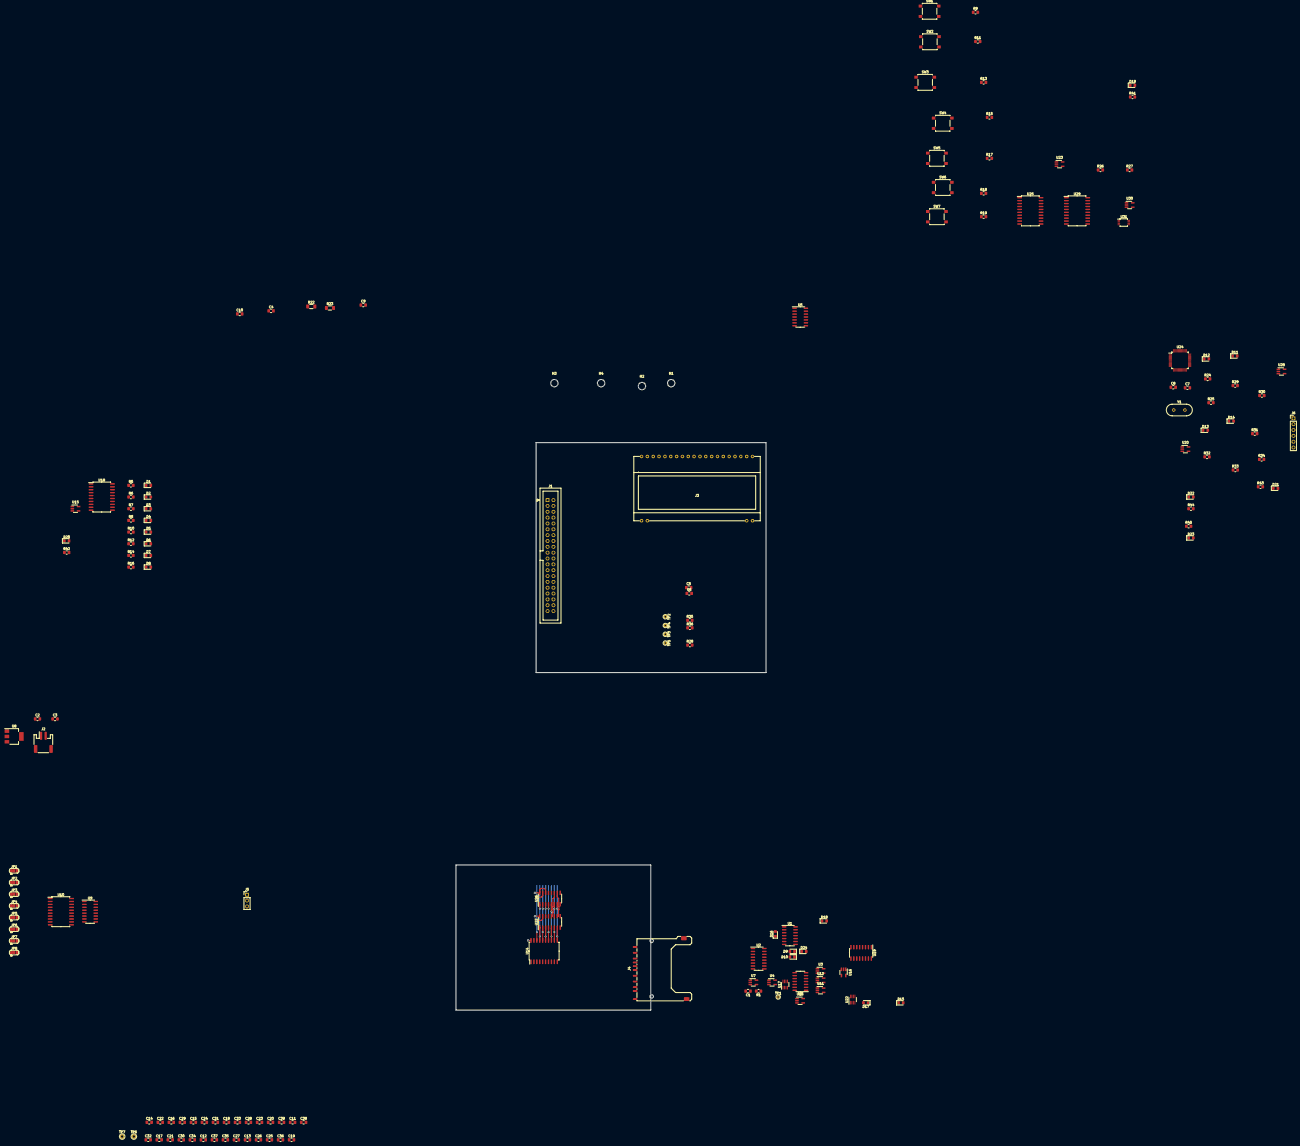
[picture p39: board memory-io.kicad_pcb from above]

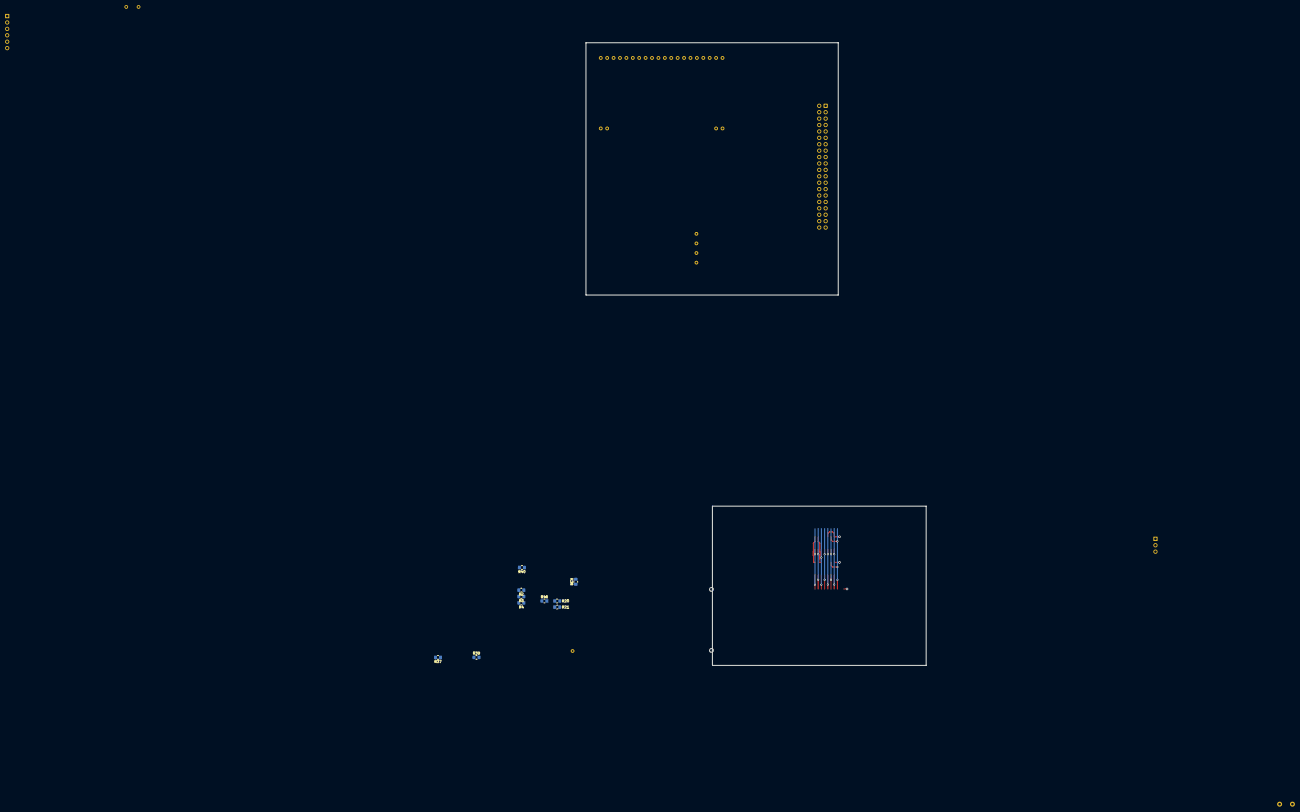
[picture p40: board memory-io.kicad_pcb from below]

Board: 4 copper layers, 172 parts (10 on the bottom side), 140 nets.
