olofos/rv321/hardware/test-bench/test-bench.kicad_pcb

## KiCad design hardware/test-bench/test-bench.kicad_pcb (2022-06-17)

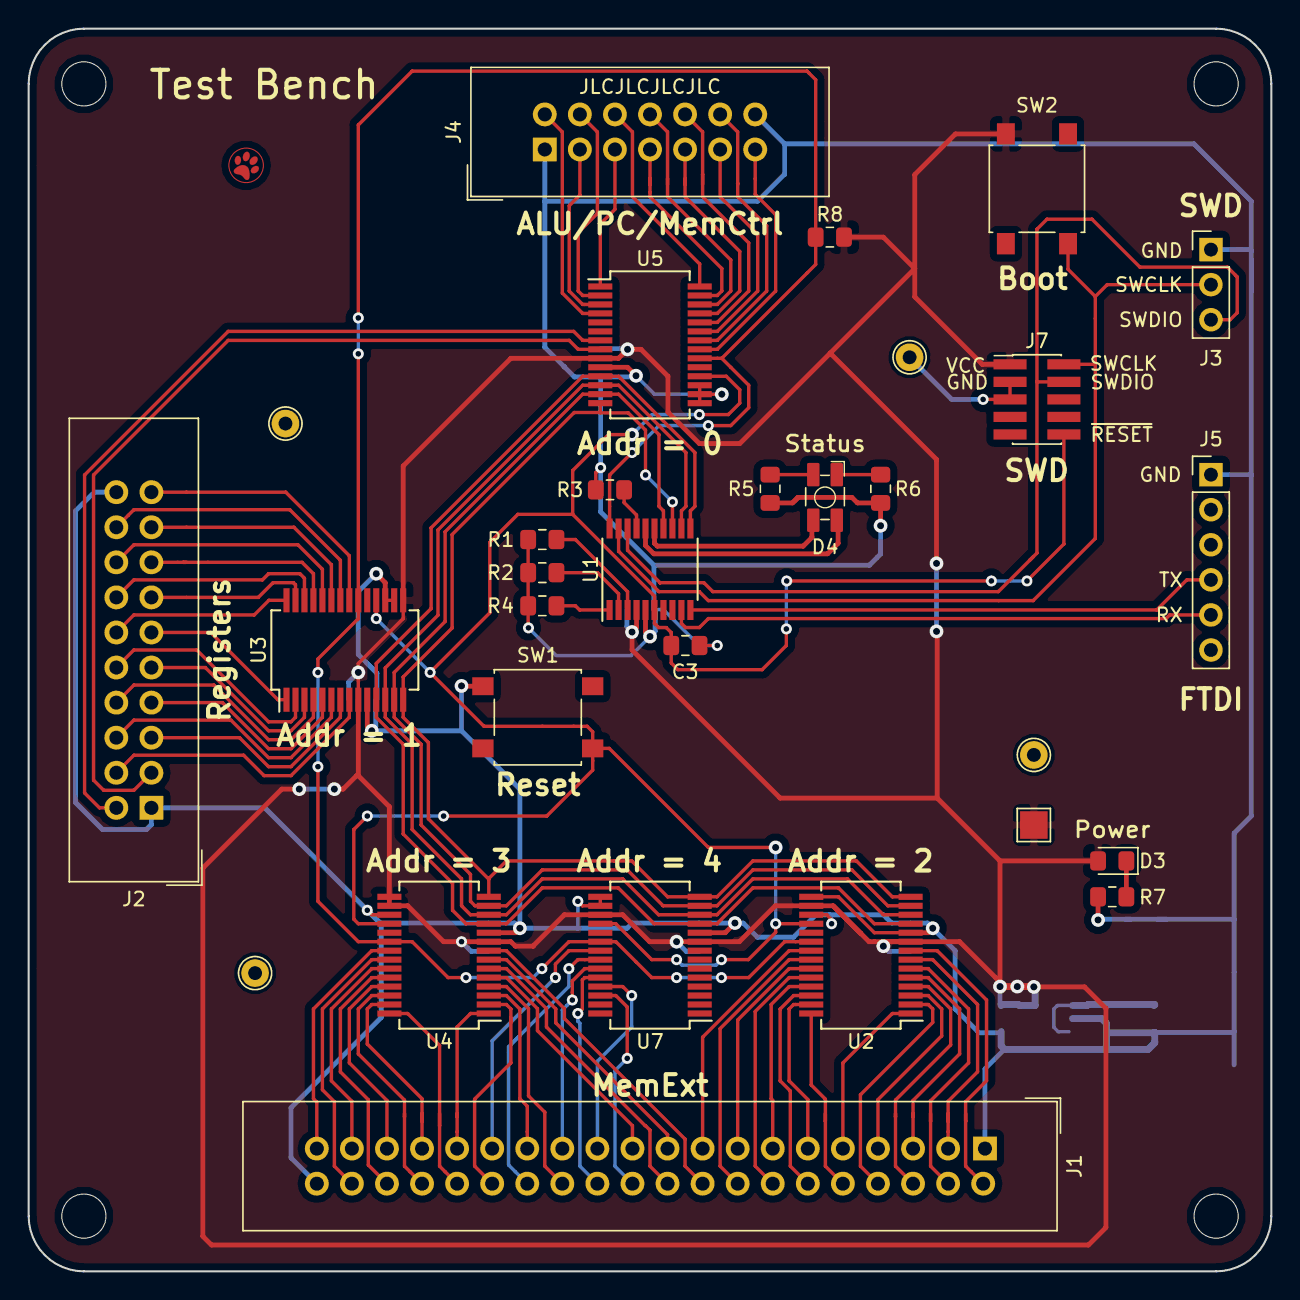
[picture p41: board test-bench.kicad_pcb from above]

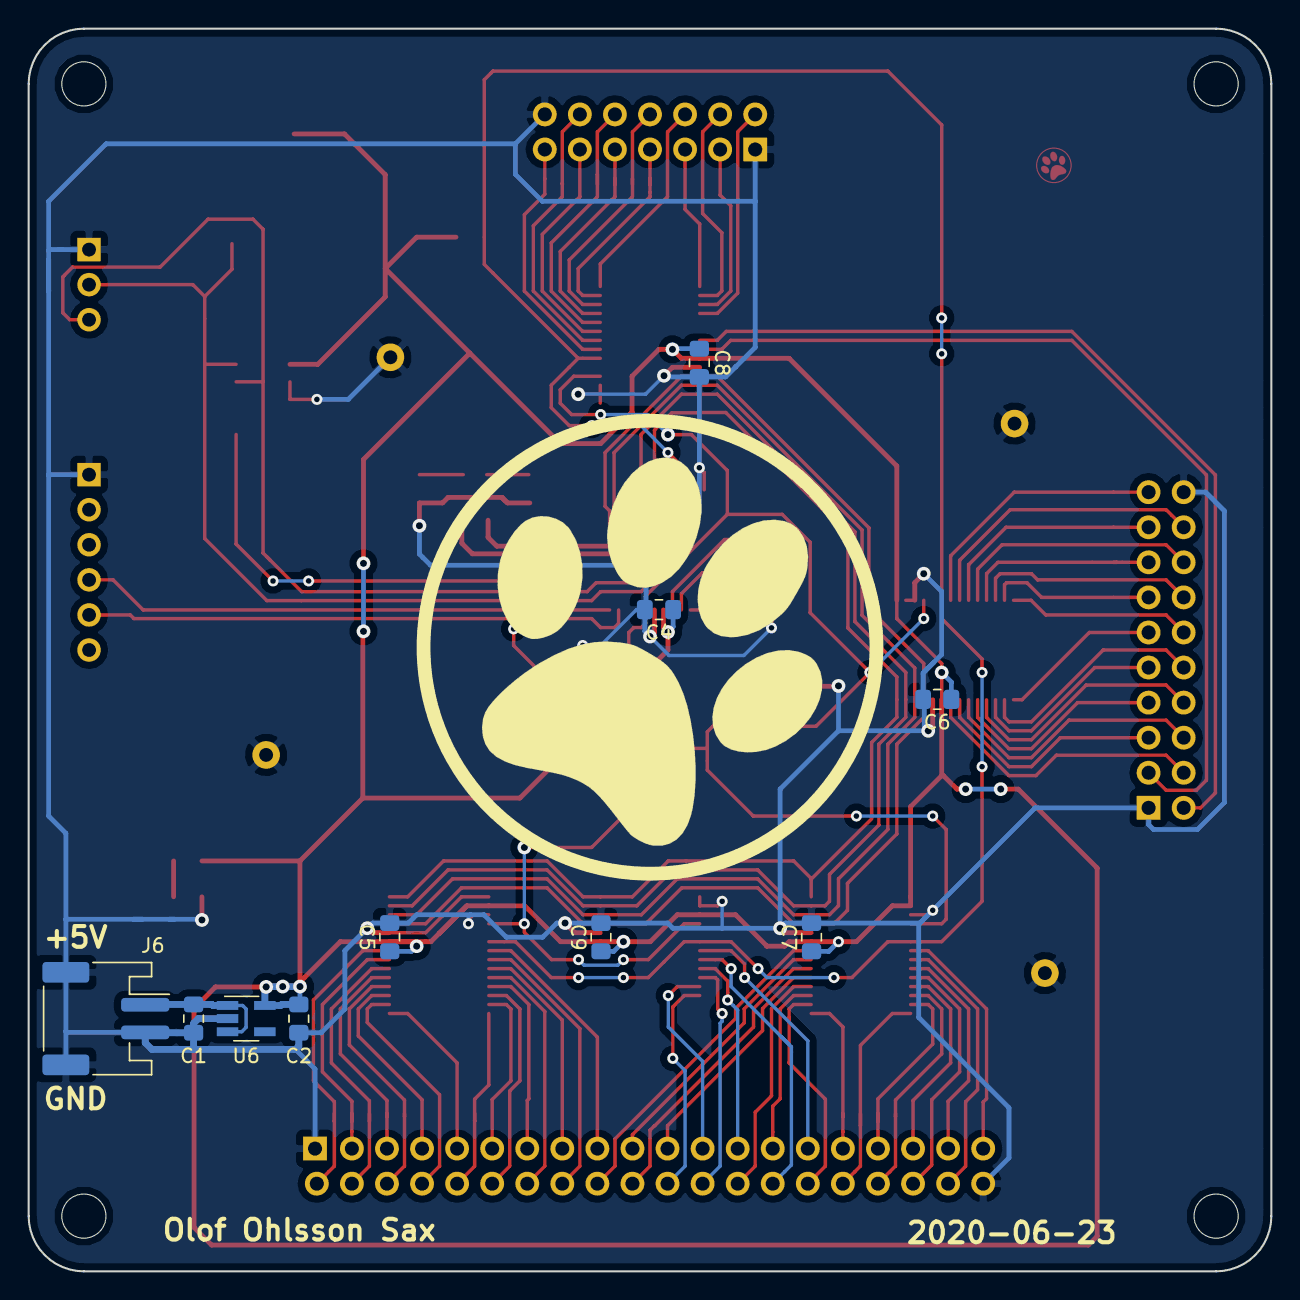
[picture p42: board test-bench.kicad_pcb from below]

Board: 2 copper layers, 90.0 x 90.0 mm, 44 parts (10 on the bottom side), 90 nets.

Parts:
C1, C2: 1u; C_0805_2012Metric_Pad1.15x1.40mm_HandSolder
C3, C4, C5, C6, C7, C8, C9: 100n; C_0805_2012Metric_Pad1.15x1.40mm_HandSolder
D3: Power; LED_0805_2012Metric_Pad1.15x1.40mm_HandSolder
D4: 150141RV73100; Wurth WL-SBTW
H1, H2, H3, H4: MountingHole; MountingHole_3.2mm_M3
J1: Conn_Mem_Ext; IDC-Header_2x20_P2.54mm_Vertical
J2: Conn_Reg; IDC-Header_2x10_P2.54mm_Vertical
J3: SWD; PinHeader_1x03_P2.54mm_Vertical
J4: Conn_Mem; IDC-Header_2x07_P2.54mm_Vertical
J5: FTDI; PinHeader_1x06_P2.54mm_Vertical
J6: Conn_Power; JST_PH_S2B-PH-SM4-TB_1x02-1MP_P2.00mm_Horizontal
J7: J_LINK_SWD; PinHeader_2x05_P1.27mm_Vertical_SMD
R1, R2, R3, R4, R8: 10k; R_0805_2012Metric_Pad1.15x1.40mm_HandSolder
R5, R6: 220; R_0805_2012Metric_Pad1.15x1.40mm_HandSolder
R7: 330; R_0805_2012Metric_Pad1.15x1.40mm_HandSolder
SW1, SW2: SW_Push_4pin; SW_SPST_DTSM-6
TP1, TP2, TP3, TP4: TestPoint; TestPoint_THTPad_D2.0mm_Drill1.0mm
TP5: TestPoint; TestPoint_Pad_2.0x2.0mm
U1: STM32G030F6; TSSOP-20_4.4x6.5mm_P0.65mm
U2, U3, U4, U5, U7: MCP23S17_SS; SSOP-28_5.3x10.2mm_P0.65mm
U6: MIC5504-3.3YM5; SOT-23-5_HandSoldering

Connections:
/FTDI_RX: J5.5, U1.9
/FTDI_TX: J5.4, U1.10
/GREEN: D4.2, U1.15
/INT: R8.1, U1.20, U2.20, U3.20, U4.20, U5.20, U7.20
/IO0A0: J4.13, U5.21
/IO0A1: J4.12, U5.22
/IO0A2: J4.11, U5.23
/IO0A3: J4.10, U5.24
/IO0A4: J4.9, U5.25
/IO0A5: J4.8, U5.26
/IO0A6: J4.7, U5.27
/IO0A7: J4.6, U5.28
/IO0B0: J4.5, U5.1
/IO0B1: J4.4, U5.2
/IO0B2: J4.3, U5.3
/IO0B3: J4.2, U5.4
/IO0B6: J2.2, U5.7
/IO0B7: J2.3, U5.8
/IO1A0: J2.19, U3.21
/IO1A1: J2.18, U3.22
/IO1A2: J2.17, U3.23
/IO1A3: J2.16, U3.24
/IO1A4: J2.15, U3.25
/IO1A5: J2.14, U3.26
/IO1A6: J2.13, U3.27
/IO1A7: J2.12, U3.28
/IO1B0: J2.11, U3.1
/IO1B1: J2.10, U3.2
/IO1B2: J2.9, U3.3
/IO1B3: J2.8, U3.4
/IO1B4: J2.7, U3.5
/IO1B5: J2.6, U3.6
/IO1B6: J2.5, U3.7
/IO1B7: J2.4, U3.8
/IO2A0: J1.17, U2.21
/IO2A1: J1.16, U2.22
/IO2A2: J1.15, U2.23
/IO2A3: J1.14, U2.24
/IO2A4: J1.13, U2.25
/IO2A5: J1.12, U2.26
/IO2A6: J1.11, U2.27
/IO2A7: J1.10, U2.28
/IO2B0: J1.9, U2.1
/IO2B1: J1.8, U2.2
/IO2B2: J1.7, U2.3
/IO2B3: J1.6, U2.4
/IO2B4: J1.5, U2.5
/IO2B5: J1.4, U2.6
/IO2B6: J1.3, U2.7
/IO2B7: J1.2, U2.8
/IO3A0: J1.39, U4.21
/IO3A1: J1.38, U4.22
/IO3A2: J1.37, U4.23
/IO3A3: J1.36, U4.24
/IO3A4: J1.35, U4.25
/IO3A5: J1.34, U4.26
/IO3A6: J1.33, U4.27
/IO3A7: J1.32, U4.28
/IO3B0: J1.31, U4.1
/IO3B1: J1.30, U4.2
/IO3B2: J1.27, U4.3
/IO3B3: J1.26, U4.4
/IO3B4: J1.21, U4.5
/IO3B5: J1.20, U4.6
/IO3B6: J1.19, U4.7
/IO3B7: J1.18, U4.8
/IO4A0: J1.29, U7.21
/IO4A1: J1.28, U7.22
/IO4A2: J1.25, U7.23
/IO4A3: J1.24, U7.24
/IO4A4: J1.23, U7.25
/IO4A5: J1.22, U7.26
/LED_G_K: D4.4, R5.2
/LED_POWER_K: D3.1, R7.2
/LED_R_K: D4.3, R6.2
/MISO: U1.13, U2.14, U3.14, U4.14, U5.14, U7.14
/MOSI: U1.14, U2.13, U3.13, U4.13, U5.13, U7.13
/PA14: R3.2, U1.17
/PB7: R4.2, U1.1
/PC14: R2.2, U1.2
/PC15: R1.2, U1.3
/RED: D4.1, U1.16
/SCK: U1.12, U2.12, U3.12, U4.12, U5.12, U7.12
/SWCLK: J3.2, J7.2, SW2.3, U1.19
/SWDIO: J3.3, J7.4, U1.18
/V_IN: C1.1, J6.1, U6.1, U6.3
/~CS: U1.11, U2.11, U3.11, U4.11, U5.11, U7.11
/~RESET: C3.1, J7.10, SW1.4, U1.6, U2.18, U3.18, U4.18, U5.18, U7.18
GND: C1.2, C2.2, C3.2, C4.2, C5.2, C6.2, C7.2, C8.2, C9.2, J1.1, J1.40, J2.1, J2.20, J3.1, J4.1, J4.14, J5.1, J6.2, J6.MP, J7.3, J7.5, R1.1, R2.1, R3.1, R4.1, R5.1, R6.1, R7.1, SW1.1, TP1.1, TP2.1, TP3.1, TP4.1, U1.5, U2.10, U2.15, U2.17, U3.10, U3.16, U3.17, U4.10, U4.17, U5.10, U5.15, U5.16, U5.17, U6.2, U7.10, U7.15, U7.16
VCC: C2.1, C4.1, C5.1, C6.1, C7.1, C8.1, C9.1, D3.2, J7.1, R8.2, SW2.2, TP5.1, U1.4, U2.9, U2.16, U3.9, U3.15, U4.9, U4.15, U4.16, U5.9, U6.5, U7.9, U7.17
