olofos/rv321/hardware/ribbon-viewer/ribbon-viewer.kicad_pcb

## KiCad design hardware/ribbon-viewer/ribbon-viewer.kicad_pcb (2022-06-17)

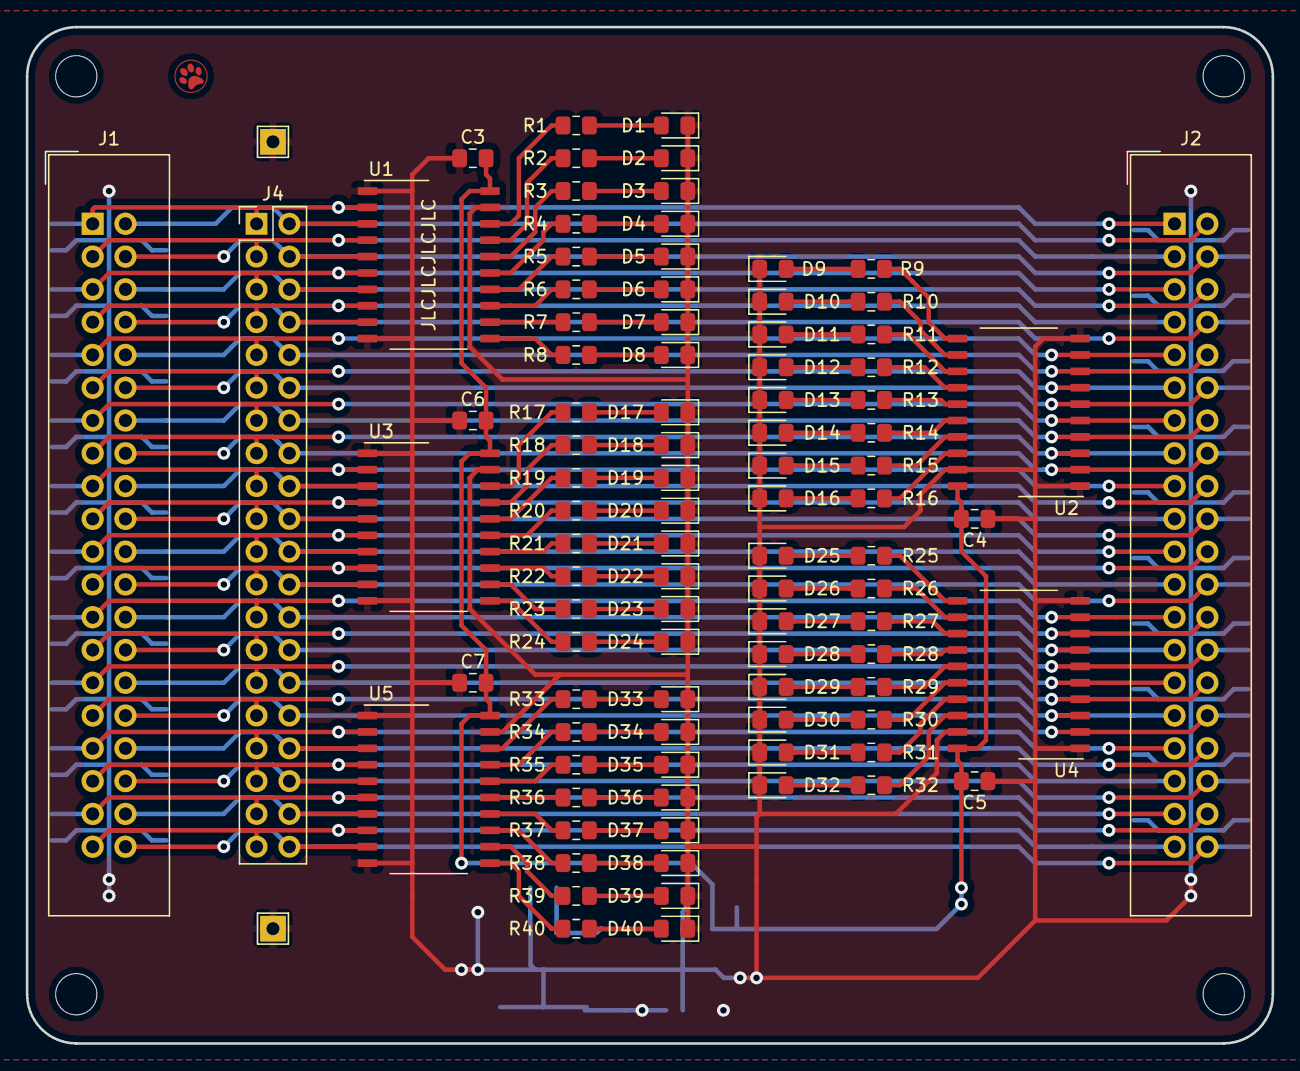
[picture p43: board ribbon-viewer.kicad_pcb from above]

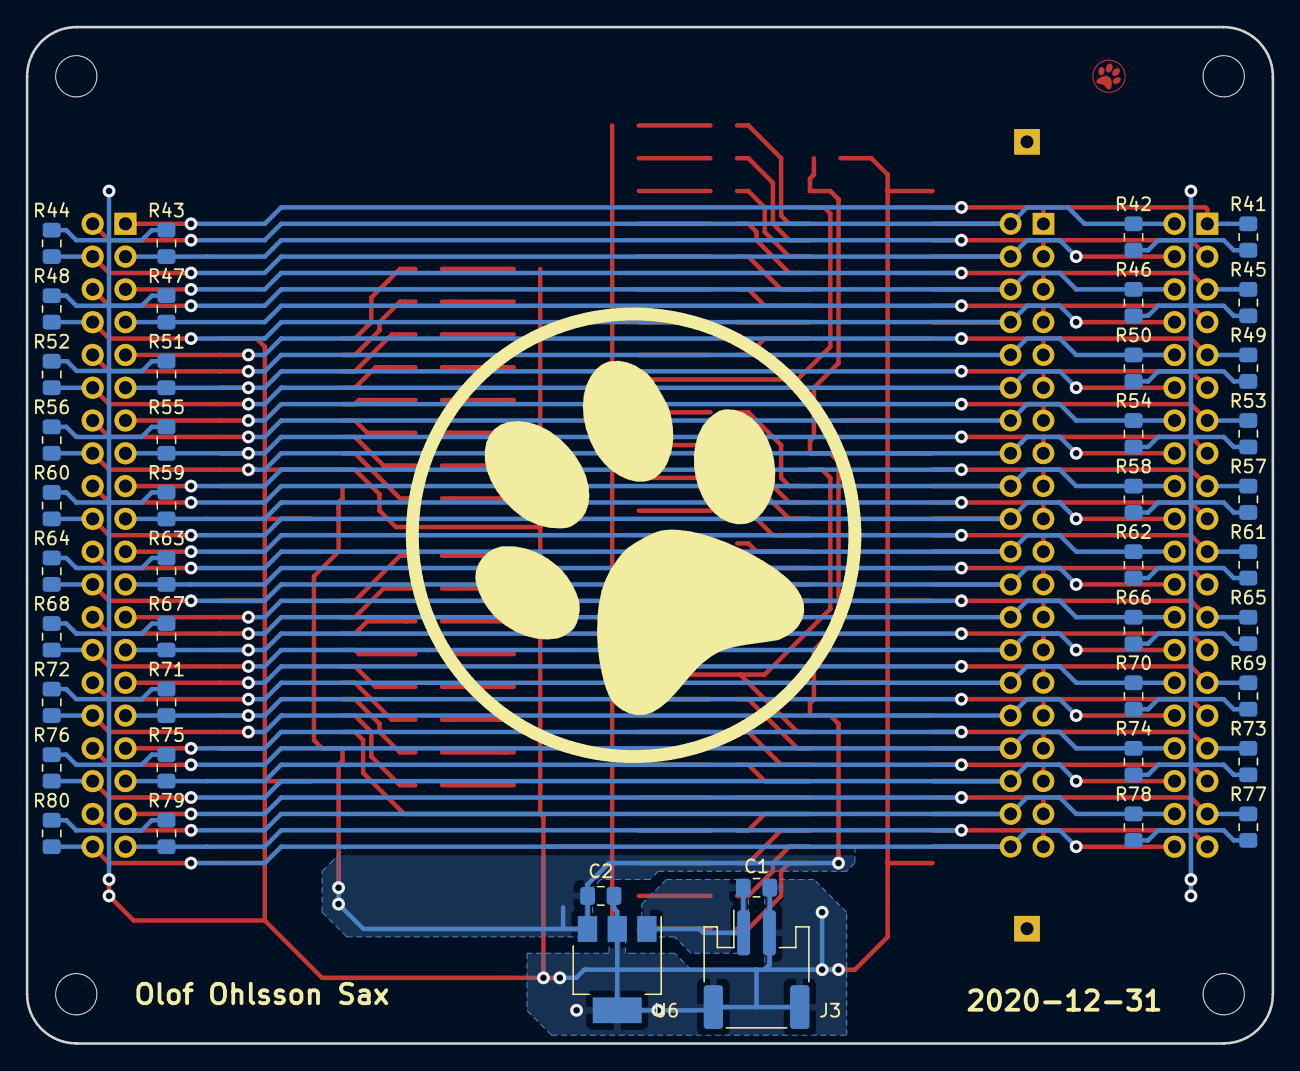
[picture p44: board ribbon-viewer.kicad_pcb from below]

Board: 2 copper layers, 96.5 x 78.7 mm, 145 parts (45 on the bottom side), 123 nets.

Parts:
C1: 4u7; C_0805_2012Metric_Pad1.15x1.40mm_HandSolder
C2: 1u; C_0805_2012Metric_Pad1.15x1.40mm_HandSolder
C3, C4, C5, C6, C7: 100n; C_0805_2012Metric_Pad1.15x1.40mm_HandSolder
D1, D2, D3, D4, D5, D6, D7, D8, D9, D10, D11, D12, D13, D14, D15, D16, D17, D18, D19, D20, D21, D22, D23, D24, D25, D26, D27, D28, D29, D30, D31, D32, D33, D34, D35, D36, D37, D38, D39, D40: LED; LED_0805_2012Metric_Pad1.15x1.40mm_HandSolder
G1: Logo_Open_Hardware_Small; paw-cu-circ
G2: Logo_Open_Hardware_Small; paw-larger-screen
H1, H2, H3, H4: MountingHole; MountingHole_3.2mm_M3
J1, J2: Conn_01x40; IDC-Header_2x20_P2.54mm_Vertical
J3: Power; JST_PH_S2B-PH-SM4-TB_1x02-1MP_P2.00mm_Horizontal
J4: Conn_01x40; PinHeader_2x20_P2.54mm_Vertical
R1, R2, R3, R4, R5, R6, R7, R8, R9, R10, R11, R12, R13, R14, R15, R16, R17, R18, R19, R20, R21, R22, R23, R24, R25, R26, R27, R28, R29, R30, R31, R32, R33, R34, R35, R36, R37, R38, R39, R40, R41, R42, R43, R44, R45, R46, R47, R48, R49, R50, R51, R52, R53, R54, R55, R56, R57, R58, R59, R60, R61, R62, R63, R64, R65, R66, R67, R68, R69, R70, R71, R72, R73, R74, R75, R76, R77, R78, R79, R80: R; R_0805_2012Metric_Pad1.15x1.40mm_HandSolder
TP41, TP42: TestPoint; TestPoint_THTPad_2.0x2.0mm_Drill1.0mm
U1, U2, U3, U4, U5: 74HC541; SO-20_12.8x7.5mm_P1.27mm
U6: MCP1825S; SOT-223-3_TabPin2

Connections:
/D1: J1.1, J2.1, J4.1, R41.2, U1.2
/D2: J1.2, J2.2, J4.2, R42.2, U1.3
/D3: J1.3, J2.3, J4.3, R43.2, U1.4
/D4: J1.4, J2.4, J4.4, R44.2, U1.5
/D5: J1.5, J2.5, J4.5, R45.2, U1.6
/D6: J1.6, J2.6, J4.6, R46.2, U1.7
/D7: J1.7, J2.7, J4.7, R47.2, U1.8
/D8: J1.8, J2.8, J4.8, R48.2, U1.9
/D9: J1.9, J2.9, J4.9, R49.2, U2.9
/D10: J1.10, J2.10, J4.10, R50.2, U2.8
/D11: J1.11, J2.11, J4.11, R51.2, U2.7
/D12: J1.12, J2.12, J4.12, R52.2, U2.6
/D13: J1.13, J2.13, J4.13, R53.2, U2.5
/D14: J1.14, J2.14, J4.14, R54.2, U2.4
/D15: J1.15, J2.15, J4.15, R55.2, U2.3
/D16: J1.16, J2.16, J4.16, R56.2, U2.2
/D17: J1.17, J2.17, J4.17, R57.2, U3.2
/D18: J1.18, J2.18, J4.18, R58.2, U3.3
/D19: J1.19, J2.19, J4.19, R59.2, U3.4
/D20: J1.20, J2.20, J4.20, R60.2, U3.5
/D21: J1.21, J2.21, J4.21, R61.2, U3.6
/D22: J1.22, J2.22, J4.22, R62.2, U3.7
/D23: J1.23, J2.23, J4.23, R63.2, U3.8
/D24: J1.24, J2.24, J4.24, R64.2, U3.9
/D25: J1.25, J2.25, J4.25, R65.2, U4.9
/D26: J1.26, J2.26, J4.26, R66.2, U4.8
/D27: J1.27, J2.27, J4.27, R67.2, U4.7
/D28: J1.28, J2.28, J4.28, R68.2, U4.6
/D29: J1.29, J2.29, J4.29, R69.2, U4.5
/D30: J1.30, J2.30, J4.30, R70.2, U4.4
/D31: J1.31, J2.31, J4.31, R71.2, U4.3
/D32: J1.32, J2.32, J4.32, R72.2, U4.2
/D33: J1.33, J2.33, J4.33, R73.2, U5.2
/D34: J1.34, J2.34, J4.34, R74.2, U5.3
/D35: J1.35, J2.35, J4.35, R75.2, U5.4
/D36: J1.36, J2.36, J4.36, R76.2, U5.5
/D37: J1.37, J2.37, J4.37, R77.2, U5.6
/D38: J1.38, J2.38, J4.38, R78.2, U5.7
/D39: J1.39, J2.39, J4.39, R79.2, U5.8
/D40: J1.40, J2.40, J4.40, R80.2, U5.9
/VIN: C1.1, J3.1, U6.1
GND: C1.2, C2.2, C3.2, C4.2, C5.2, C6.2, C7.2, D1.1, D2.1, D3.1, D4.1, D5.1, D6.1, D7.1, D8.1, D9.1, D10.1, D11.1, D12.1, D13.1, D14.1, D15.1, D16.1, D17.1, D18.1, D19.1, D20.1, D21.1, D22.1, D23.1, D24.1, D25.1, D26.1, D27.1, D28.1, D29.1, D30.1, D31.1, D32.1, D33.1, D34.1, D35.1, D36.1, D37.1, D38.1, D39.1, D40.1, J3.2, J3.MP, R41.1, R42.1, R43.1, R44.1, R45.1, R46.1, R47.1, R48.1, R49.1, R50.1, R51.1, R52.1, R53.1, R54.1, R55.1, R56.1, R57.1, R58.1, R59.1, R60.1, R61.1, R62.1, R63.1, R64.1, R65.1, R66.1, R67.1, R68.1, R69.1, R70.1, R71.1, R72.1, R73.1, R74.1, R75.1, R76.1, R77.1, R78.1, R79.1, R80.1, TP41.1, TP42.1, U1.1, U1.10, U1.19, U2.1, U2.10, U2.19, U3.1, U3.10, U3.19, U4.1, U4.10, U4.19, U5.1, U5.10, U5.19, U6.2
unnamed: D1.2, R1.2
unnamed: D2.2, R2.2
unnamed: D3.2, R3.2
unnamed: D4.2, R4.2
unnamed: D5.2, R5.2
unnamed: D6.2, R6.2
unnamed: D7.2, R7.2
unnamed: D8.2, R8.2
unnamed: D9.2, R9.2
unnamed: D10.2, R10.2
unnamed: D11.2, R11.2
unnamed: D12.2, R12.2
unnamed: D13.2, R13.2
unnamed: D14.2, R14.2
unnamed: D15.2, R15.2
unnamed: D16.2, R16.2
unnamed: D17.2, R17.2
unnamed: D18.2, R18.2
unnamed: D19.2, R19.2
unnamed: D20.2, R20.2
unnamed: D21.2, R21.2
unnamed: D22.2, R22.2
unnamed: D23.2, R23.2
unnamed: D24.2, R24.2
unnamed: D25.2, R25.2
unnamed: D26.2, R26.2
unnamed: D27.2, R27.2
unnamed: D28.2, R28.2
unnamed: D29.2, R29.2
unnamed: D30.2, R30.2
unnamed: D31.2, R31.2
unnamed: D32.2, R32.2
unnamed: D33.2, R33.2
unnamed: D34.2, R34.2
unnamed: D35.2, R35.2
unnamed: D36.2, R36.2
unnamed: D37.2, R37.2
unnamed: D38.2, R38.2
unnamed: D39.2, R39.2
unnamed: D40.2, R40.2
unnamed: R1.1, U1.18
unnamed: R2.1, U1.17
unnamed: R3.1, U1.16
unnamed: R4.1, U1.15
unnamed: R5.1, U1.14
unnamed: R6.1, U1.13
unnamed: R7.1, U1.12
unnamed: R8.1, U1.11
unnamed: R9.1, U2.11
unnamed: R10.1, U2.12
unnamed: R11.1, U2.13
unnamed: R12.1, U2.14
unnamed: R13.1, U2.15
unnamed: R14.1, U2.16
unnamed: R15.1, U2.17
unnamed: R16.1, U2.18
unnamed: R17.1, U3.18
unnamed: R18.1, U3.17
unnamed: R19.1, U3.16
unnamed: R20.1, U3.15
unnamed: R21.1, U3.14
unnamed: R22.1, U3.13
unnamed: R23.1, U3.12
unnamed: R24.1, U3.11
unnamed: R25.1, U4.11
unnamed: R26.1, U4.12
unnamed: R27.1, U4.13
unnamed: R28.1, U4.14
unnamed: R29.1, U4.15
unnamed: R30.1, U4.16
unnamed: R31.1, U4.17
unnamed: R32.1, U4.18
unnamed: R33.1, U5.18
unnamed: R34.1, U5.17
unnamed: R35.1, U5.16
unnamed: R36.1, U5.15
unnamed: R37.1, U5.14
unnamed: R38.1, U5.13
unnamed: R39.1, U5.12
unnamed: R40.1, U5.11
VCC: C2.1, C3.1, C4.1, C5.1, C6.1, C7.1, U1.20, U2.20, U3.20, U4.20, U5.20, U6.3
