olofos/rv321/hardware/power-splitter/power-splitter.kicad_pcb

## KiCad design hardware/power-splitter/power-splitter.kicad_pcb (2022-06-17)

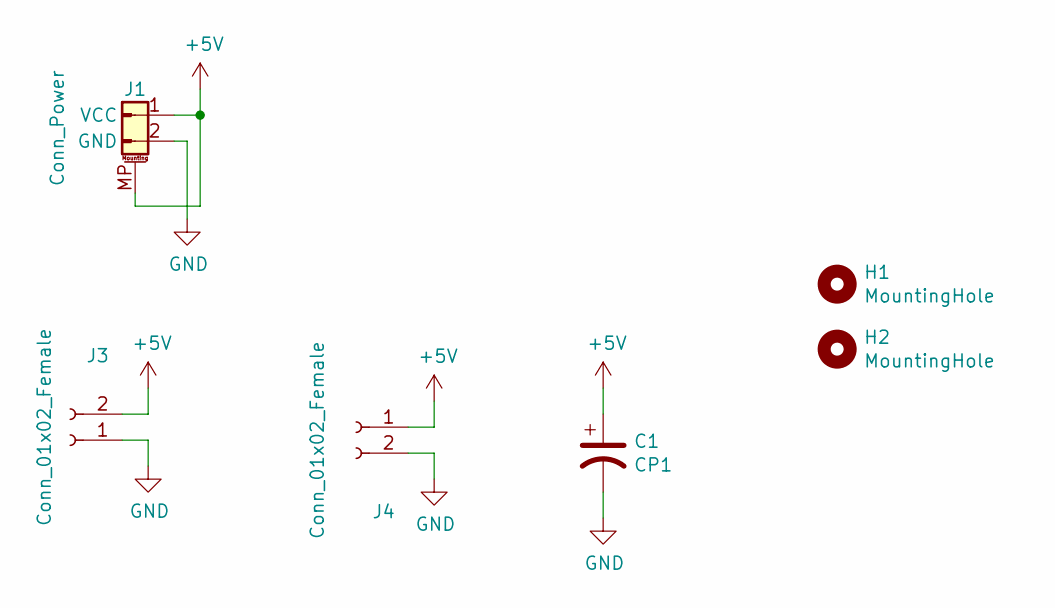
[picture p45: schematic power-splitter.kicad_sch]

Parts:
C1: CP1; CP_Elec_5x5.3
H1, H2: MountingHole; MountingHole_3.2mm_M3
J1: Conn_Power; JST_PH_S2B-PH-SM4-TB_1x02-1MP_P2.00mm_Horizontal
J3, J4: Conn_01x02_Female; TerminalBlock_01x02_p5.08

Connections:
+5V: C1.1, J1.1 (VCC), J1.MP, J3.2, J4.1
GND: C1.2, J1.2 (GND), J3.1, J4.2

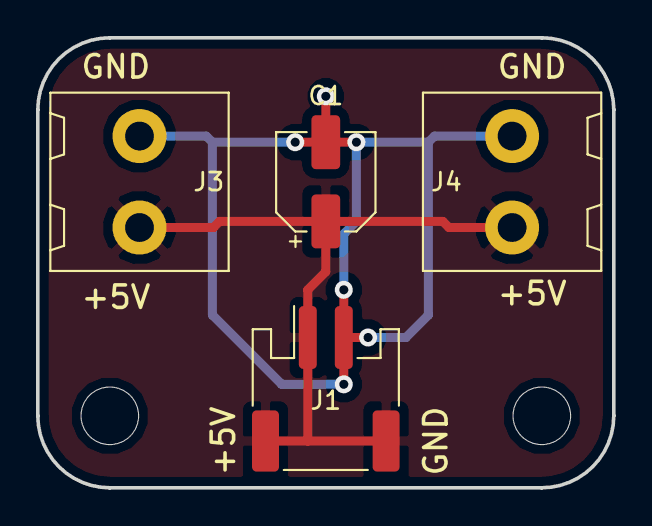
[picture p46: board power-splitter.kicad_pcb from above]

Board: 2 copper layers, 32.0 x 25.0 mm, 6 parts (0 on the bottom side), 2 nets.
