olofos/rv321/hardware/memory-lcd/memory-lcd.kicad_pcb

## KiCad design hardware/memory-lcd/memory-lcd.kicad_pcb (2022-06-17)

Schematic: memory-lcd.kicad_sch

Parts:
C1, C2: 1u; C_0805_2012Metric_Pad1.15x1.40mm_HandSolder
C3, C4, C5: 100n; C_0805_2012Metric_Pad1.15x1.40mm_HandSolder
H1, H2, H3, H4: MountingHole; MountingHole_3.2mm_M3
J1: NHD-0220FZ
J2: Conn_Mem_Ext; IDC-Header_2x20_P2.54mm_Vertical
J3: Conn_Power; JST_PH_S2B-PH-SM4-TB_1x02-1MP_P2.00mm_Horizontal
JP1, JP2, JP3, JP4, JP5, JP6: SolderJumper_3_Bridged12; SolderJumper-3_P1.3mm_Bridged2Bar12_RoundedPad1.0x1.5mm
RV1: 10k; Potentiometer_Bourns_3386P_Vertical
U1: 74HC688; SO-20_12.8x7.5mm_P1.27mm
U2: 74LVC1G08; SOT-23-5_HandSoldering
U3: MIC5504-3.3YM5; SOT-23-5_HandSoldering
U4: 74LVC1G04; SOT-23-5_HandSoldering

Connections:
/A0: J1.4 (RS), J2.2 (A0)
/A1: J2.3 (A1), U1.6 (P2)
/A2: J2.4 (A2), U1.8 (P3)
/A3: J2.5 (A3), U1.11 (P4)
/A4: J2.6 (A4), U1.13 (P5)
/A5: J2.7 (A5), U1.15 (P6)
/A6: J2.8 (A6), U1.17 (P7)
/A7: J2.9 (A7)
/A8: J2.10 (A8)
/A9: J2.11 (A9)
/A10: J2.12 (A10)
/A11: J2.13 (A11)
/A12: J2.14 (A12)
/A13: J2.15 (A13)
/A14: J2.16 (A14)
/A15: J2.17 (A15)
/A16: J2.18 (A16)
/A17: J2.19 (A17)
/A18: J2.20 (A18)
/A19: J2.21 (A19)
/A20: J2.22 (A20)
/A21: J2.23 (A21)
/A22: J2.24 (A22)
/A23: J2.25 (A23)
/A30: J2.26 (A30), U1.2 (P0)
/A31: J2.27 (A31), U1.4 (P1)
/B1: JP1.2 (C), U1.7 (R2)
/B2: JP2.2 (C), U1.9 (R3)
/B3: JP3.2 (C), U1.12 (R4)
/B4: JP4.2 (C), U1.14 (R5)
/B5: JP5.2 (C), U1.16 (R6)
/B6: JP6.2 (C), U1.18 (R7)
/D0: J1.14 (DB7), J2.32 (D0)
/D1: J1.13 (DB6), J2.33 (D1)
/D2: J1.12 (DB5), J2.34 (D2)
/D3: J1.11 (DB4), J2.35 (D3)
/D4: J1.10 (DB3), J2.36 (D4)
/D5: J1.9 (DB2), J2.37 (D5)
/D6: J1.8 (DB1), J2.38 (D6)
/D7: J1.7 (DB0), J2.39 (D7)
/LCD_E: J1.6 (E), U4.4
/V_IN: C1.2, J3.1 (VCC), U3.1 (VIN), U3.3 (EN)
/~LCD_E: U1.19 (P=R), U4.2
/~MEM_E: U1.1 (G), U2.4
/~MEM_OE: J2.30 (~MEM_OE), U2.1
/~MEM_WE: J1.5 (R/~W), J2.31 (~MEM_WE), U2.2
/~RESET: J2.28 (~RESET)
/~WAIT: J2.29 (~WAIT)
GND: C1.1, C2.1, C3.1, C4.1, C5.1, J1.1 (GND), J1.16 (K-), J2.1 (GND), J2.40 (GND), J3.2 (GND), J3.MP, JP1.1 (A), JP2.1 (A), JP3.1 (A), JP4.1 (A), JP5.1 (A), JP6.1 (A), RV1.3, U1.5 (R1), U1.10 (GND), U2.3 (GND), U3.2 (GND), U4.3 (GND)
unnamed: J1.3 (Vcontr), RV1.2
VCC: C2.2, C3.2, C4.2, C5.2, J1.2 (VCC), J1.15 (A+), JP1.3 (B), JP2.3 (B), JP3.3 (B), JP4.3 (B), JP5.3 (B), JP6.3 (B), RV1.1, U1.3 (R0), U1.20 (VCC), U2.5 (VCC), U3.5 (VOUT), U4.5 (VCC)

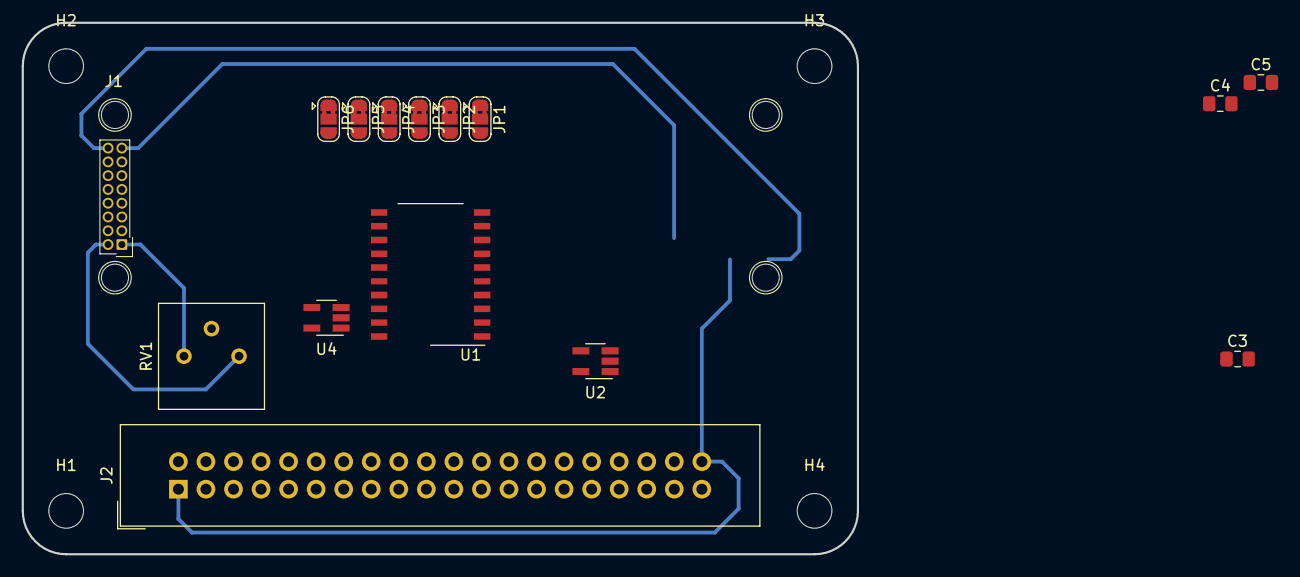
[picture p47: board memory-lcd.kicad_pcb from above]

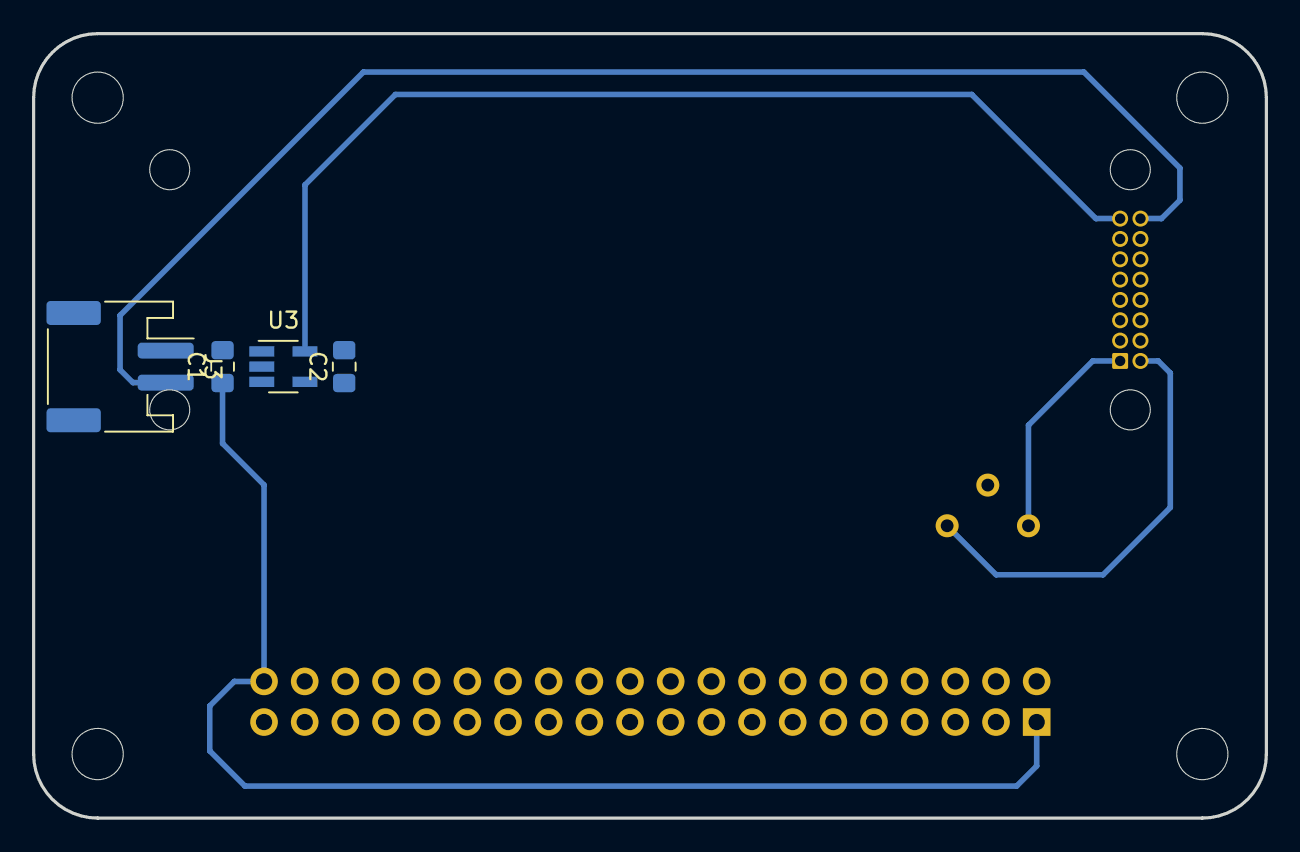
[picture p48: board memory-lcd.kicad_pcb from below]

Board: 2 copper layers, 77.0 x 49.0 mm, 23 parts (4 on the bottom side), 32 nets.
