olofos/rv321/tb/firmware/src/console-io.c

#include <unistd.h>

#include "console.h"
#include "uart.h"
#include "cbuf.h"

void console_write(const char *buf, unsigned len)
{
    uart_puts(buf, len);
}

int console_getchar(void)
{
    if(cbuf_empty(rx_cbuf)) {
        return -1;
    }
    return cbuf_pop(rx_cbuf);
}
