olofos/rv321/tb/firmware/src/systick.c

#include <stdint.h>

#include "defines.h"
#include "systick.h"
#include "startup.h"

volatile uint32_t systick = 0;

void systick_init(void)
{
    SysTick->CTRL = 0;
    SysTick->LOAD = (uint32_t) (CPU_FREQ / 1000) - 1;
    SysTick->VAL = 0;
    SysTick->CTRL = SysTick_CTRL_ENABLE_Msk | SysTick_CTRL_TICKINT_Msk | SysTick_CTRL_CLKSOURCE_Msk;
}

void systick_pause(void)
{
    SysTick->CTRL = 0;
}

void systick_resume(void)
{
    SysTick->CTRL = SysTick_CTRL_ENABLE_Msk | SysTick_CTRL_TICKINT_Msk | SysTick_CTRL_CLKSOURCE_Msk;
}

void delay(uint32_t millis)
{
    for(uint32_t tick = systick; systick - tick < millis;) {
        __WFI();
    }
}

void SysTick_Handler(void)
{
    systick++;
}
